lukeswitz/AntiHunter/docs/img/csi-motion.jpg

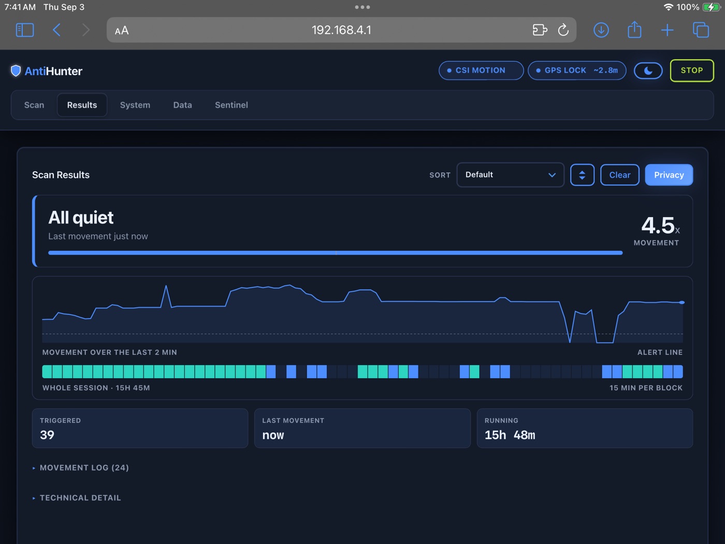
docs/img/csi-motion.jpg
