lukeswitz/AntiHunter/docs/img/hardware-node.jpg

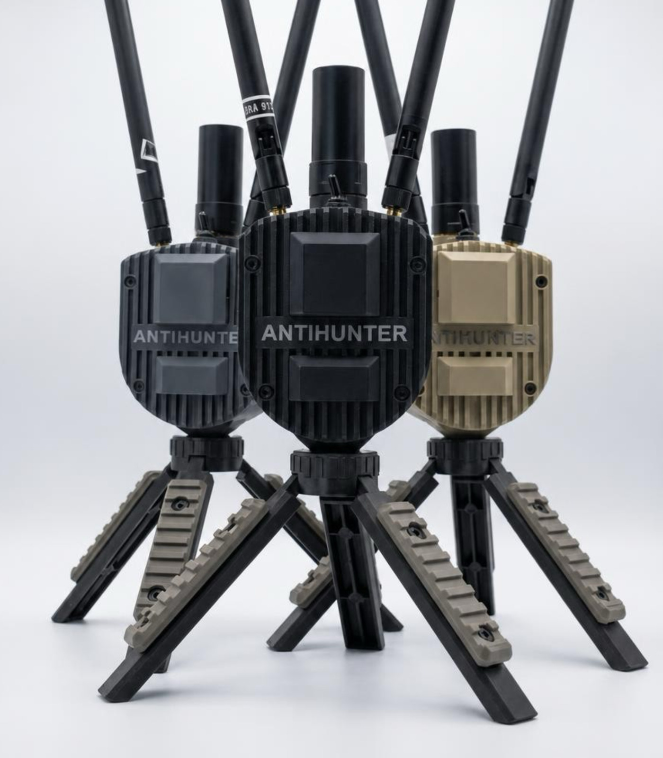
docs/img/hardware-node.jpg
