lukeswitz/AntiHunter/docs/img/node-photo.jpg

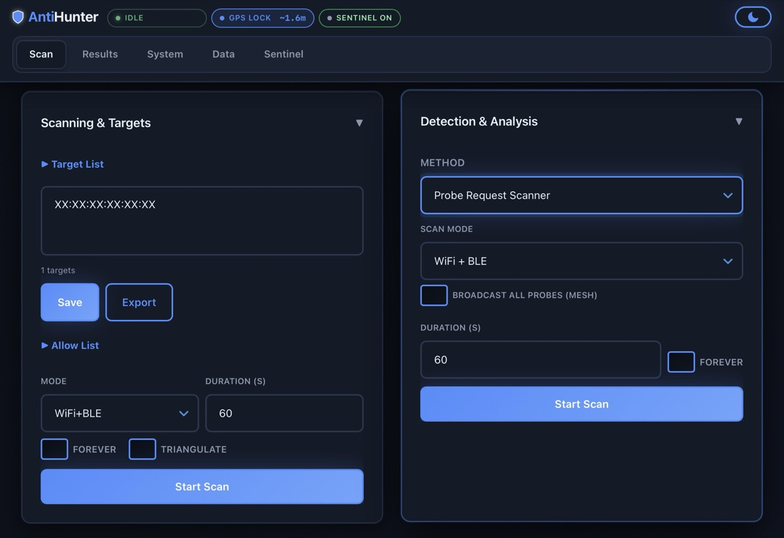
docs/img/node-photo.jpg
