lukeswitz/AntiHunter/hw/Prototype_STL_Files/AHPuckCase/puck_top.stl

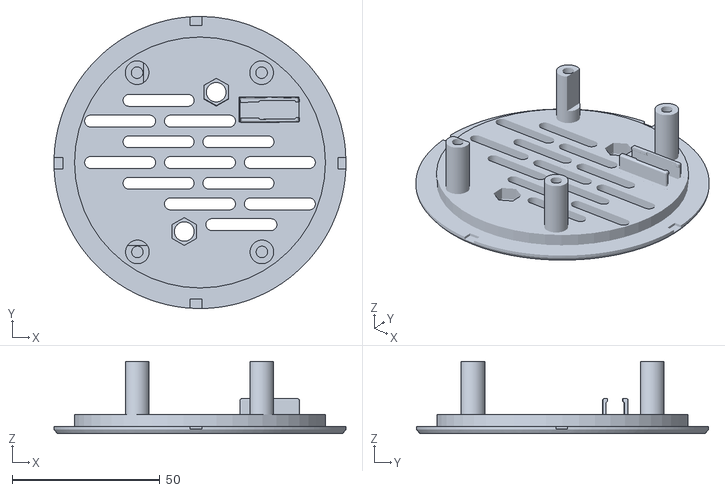
[picture p51: CAD file, 2025-11-10]
hw/Prototype_STL_Files/AHPuckCase/puck_top.stl
98.7 x 98.7 x 24.4
