lukeswitz/AntiHunter/hw/Prototype_STL_Files/AH-DIGINODE-v2/BackCover.stl

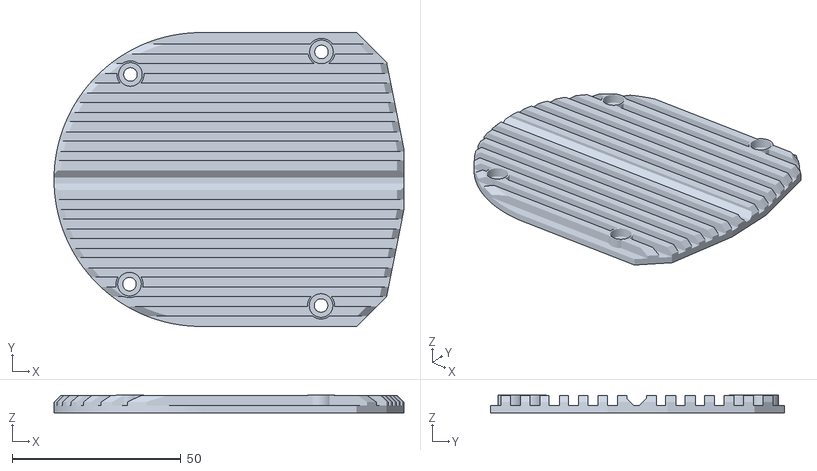
[picture p52: CAD file, 2026-02-04]
hw/Prototype_STL_Files/AH-DIGINODE-v2/BackCover.stl
103.6 x 87.0 x 5.30
