lukeswitz/AntiHunter/hw/Prototype_STL_Files/AH-DIGINODE-v2/Extentions/RadarMOD/Radar-extention-housing-fat.stl

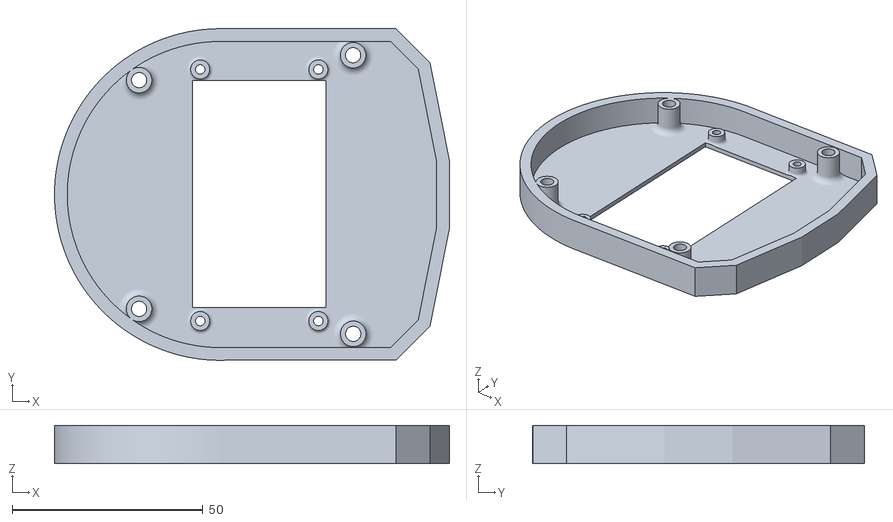
[picture p53: CAD file, 2026-02-06]
hw/Prototype_STL_Files/AH-DIGINODE-v2/Extentions/RadarMOD/Radar-extention-housing-fat.stl
103.6 x 87.0 x 10.0
