lukeswitz/AntiHunter/hw/Prototype_STL_Files/AH-DIGINODE-v2/Extentions/SEALS/Radar-SEAL.stl

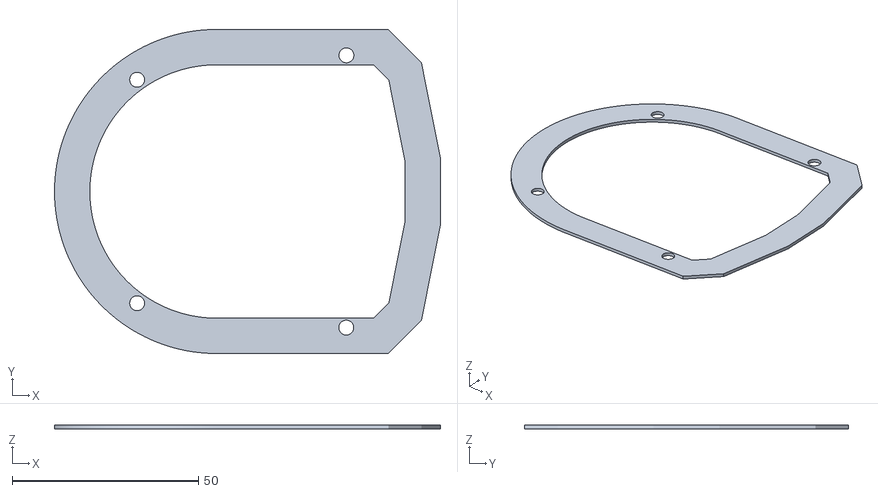
[picture p54: CAD file, 2026-02-06]
hw/Prototype_STL_Files/AH-DIGINODE-v2/Extentions/SEALS/Radar-SEAL.stl
103.6 x 87.0 x 1.00
