lukeswitz/AntiHunter/hw/Prototype_STL_Files/AHPuckCase/puck_body.stl

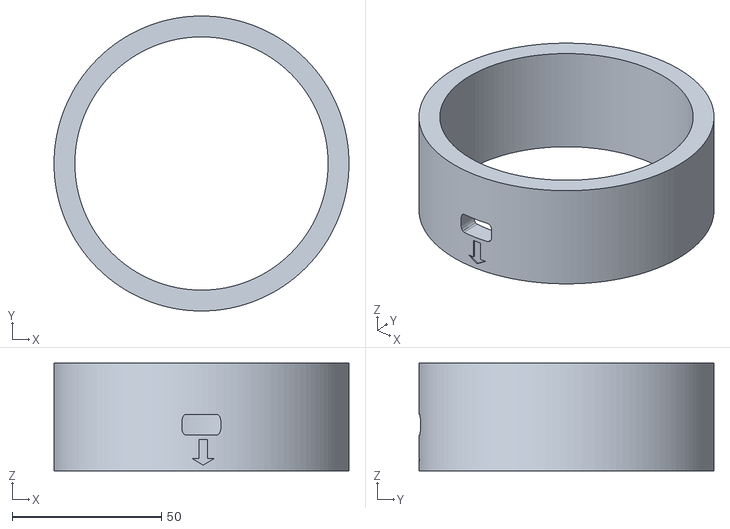
[picture p55: CAD file, 2025-11-10]
hw/Prototype_STL_Files/AHPuckCase/puck_body.stl
98.7 x 98.7 x 36.0
