lukeswitz/AntiHunter/hw/Prototype_STL_Files/AH-DIGINODE-v2/Extentions/SEALS/BatteryHousing-SEAL.stl

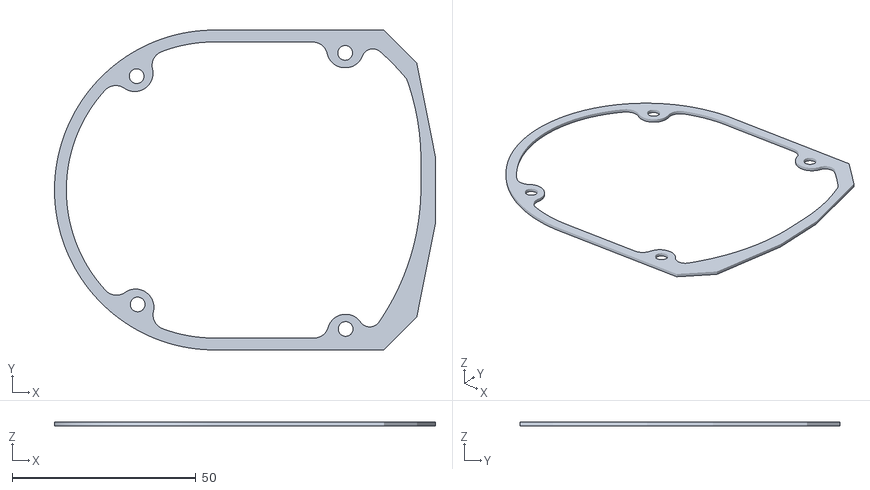
[picture p56: CAD file, 2026-02-04]
hw/Prototype_STL_Files/AH-DIGINODE-v2/Extentions/SEALS/BatteryHousing-SEAL.stl
103.6 x 87.0 x 1.00
