lukeswitz/AntiHunter/hw/Prototype_STL_Files/AH-DIGINODE-v2/FrontCover-Hidden-Fan.stl

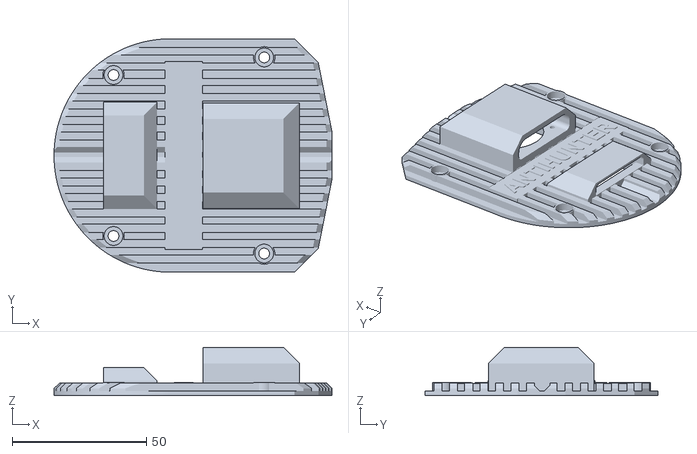
[picture p57: CAD file, 2026-02-04]
hw/Prototype_STL_Files/AH-DIGINODE-v2/FrontCover-Hidden-Fan.stl
103.6 x 87.0 x 18.0
