lukeswitz/AntiHunter/hw/Prototype_STL_Files/AH-DIGINODE-v2/Extentions/SEALS/GPS-TPU-SEAL.stl

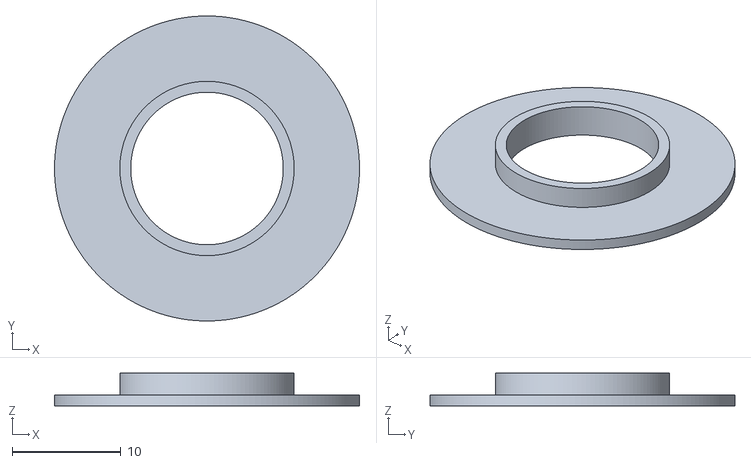
[picture p58: CAD file, 2026-02-04]
hw/Prototype_STL_Files/AH-DIGINODE-v2/Extentions/SEALS/GPS-TPU-SEAL.stl
28.0 x 28.0 x 3.00
