lukeswitz/AntiHunter/Antihunter/full/src/network.cpp

#include "network.h"
#include "baseline.h"
#include "triangulation.h"
#include "hardware.h"
#include "scanner.h"
#include "main.h"
#include "detect.h"
#include "pcap.h"
#include <AsyncTCP.h>
#include <RTClib.h>
#include <esp_timer.h>
#include <algorithm>
#include <deque>
#include <memory>

extern "C"
{
#include "esp_wifi.h"
#include "esp_wifi_types.h"
#include "esp_coexist.h"
#include "lwip/err.h"
#include "lwip/sockets.h"
}

// Network and LoRa
AsyncWebServer *server = nullptr;
static String customApSsid = "";
static String customApPass = "";
const int MAX_RETRIES = 10;
bool meshEnabled = true;
bool hbEnabled = false;
uint32_t hbInterval = 600000;
// Runtime gate for vibration mesh broadcasts (NVS key: "vibEnabled").
// Detection and USB logging always run; this only controls Serial1 TX.
bool vibrationEnabled = true;
unsigned long meshSendInterval = 3000;
std::atomic<bool> g_eraseWipeBusy{false};
volatile uint32_t apScanSuppressUntilMs = 0;
bool triangulationOrchestratorAssigned = false;


// Scanner vars
extern std::atomic<bool> scanning;
extern std::atomic<int> totalHits;
extern UniqueMacsSet uniqueMacs;

// Module refs
extern Preferences prefs;
extern std::atomic<bool> stopRequested;
extern ScanMode currentScanMode;
extern std::vector<uint8_t> CHANNELS;
extern TaskHandle_t workerTaskHandle;
extern TaskHandle_t blueTeamTaskHandle;
extern String macFmt6(const uint8_t *m);
extern bool parseMac6(const String &in, uint8_t out[6]);
extern void parseChannelsCSV(const String &csv);
extern void randomizeMacAddress();


// T114 handling
SerialRateLimiter rateLimiter;
SemaphoreHandle_t serial1Mutex = nullptr;
SerialRateLimiter::SerialRateLimiter() : tokens(MAX_TOKENS), lastRefill(millis()) {}

bool SerialRateLimiter::canSend(size_t messageLength) {
    refillTokens();
    return tokens >= messageLength;
}

void SerialRateLimiter::consume(size_t messageLength) {
    if (tokens >= messageLength) {
        tokens -= messageLength;
    }
}

void SerialRateLimiter::refillTokens() {
    unsigned long now = millis();
    if (now - lastRefill >= REFILL_INTERVAL) {
        tokens = min(tokens + TOKENS_PER_REFILL, MAX_TOKENS);
        lastRefill = now;
    }
}

void SerialRateLimiter::flush() {
    tokens = MAX_TOKENS;
    lastRefill = millis();
    Serial.println("[MESH] Rate limiter flushed");
}



bool sendToSerial1(const String &message, bool canDelay) {
    if (serial1Mutex == nullptr) {
        return false;
    }

#if !AH_CS_BLE
    if (message.indexOf(": BLE_ATTACK") >= 0) {
        return false;
    }
#endif

    bool isTriangulationMessage = message.indexOf("STOP_ACK") >= 0 ||
                                  message.indexOf("TRI_START_ACK") >= 0 ||
                                  message.indexOf("@ALL TRIANGULATE_START") >= 0 ||
                                  message.indexOf("@ALL TRI_CYCLE_START") >= 0 ||
                                  message.indexOf("TRIANGULATE_STOP") >= 0 ||
                                  message.indexOf(": T_F:") >= 0 ||
                                  message.indexOf(": T_C:") >= 0 ||
                                  message.indexOf(": T_D:") >= 0;

    if (triangulationActive && !isTriangulationMessage) {
        meshTxDroppedTriGate.fetch_add(1);
        return false;
    }

    bool isPriority = isTriangulationMessage;
    size_t msgLen = message.length() + 2;

    TickType_t timeout = isPriority ? pdMS_TO_TICKS(5000) : pdMS_TO_TICKS(1000);
    if (xSemaphoreTake(serial1Mutex, timeout) != pdTRUE) {
        Serial.printf("[MESH] Mutex timeout\n");
        return false;
    }

    // Phase 1 + review fix A: rate-limit check INSIDE mutex so canSend/consume are atomic.
    // Two concurrent senders could otherwise both pass canSend then both consume, oversubscribing the bucket.
    if (!isPriority && !rateLimiter.canSend(msgLen)) {
        meshTxDroppedRateLimit.fetch_add(1);
        Serial.printf("[MESH] DROP rate-limit: barrel_free=%u/%u need=%u msg=\"%.32s\"\n",
                      rateLimiter.available(), SerialRateLimiter::capacity(), (unsigned)msgLen, message.c_str());
        xSemaphoreGive(serial1Mutex);
        return false;
    }

    if (isPriority) {
        uint32_t waitStart = millis();
        while (Serial1.availableForWrite() < (int)msgLen) {
            if (millis() - waitStart > 5000) {
                Serial.printf("[MESH] Priority message timeout waiting for buffer space\n");
                xSemaphoreGive(serial1Mutex);
                return false;
            }
            xSemaphoreGive(serial1Mutex);
            delay(10);
            if (xSemaphoreTake(serial1Mutex, timeout) != pdTRUE) {
                Serial.printf("[MESH] Mutex timeout on retry\n");
                return false;
            }
        }
    } else {
        if (Serial1.availableForWrite() < (int)msgLen) {
            meshTxDroppedBufFull.fetch_add(1);
            Serial.printf("[MESH] DROP buf-full: avail=%d need=%u msg=\"%.32s\"\n",
                          Serial1.availableForWrite(), (unsigned)msgLen, message.c_str());
            xSemaphoreGive(serial1Mutex);
            return false;
        }
    }

    Serial1.println(message);
    Serial.printf("[MESH TX] %s\n", message.c_str());

    Serial1.flush();

    // Review fix A (completion): consume INSIDE mutex so canSend/consume are fully atomic.
    if (!isPriority) {
        rateLimiter.consume(msgLen);
    }

    {
        uint32_t total = meshDrainTotal.load();
        if (total > 0) {
            uint32_t idx = meshDrainSent.load() + meshMsgUnits(message);
            if (idx > total) idx = total;
            Serial.printf("[MESH] barrel_free=%u/%uB  drain %u/%u\n",
                          rateLimiter.available(), SerialRateLimiter::capacity(), idx, total);
        } else {
            Serial.printf("[MESH] barrel_free=%u/%uB\n",
                          rateLimiter.available(), SerialRateLimiter::capacity());
        }
    }

    xSemaphoreGive(serial1Mutex);

    return true;
}

// ------------- Network ------------- 

void restart_callback(void* arg) {
  ESP.restart();
}

void initializeNetwork()
{
  esp_coex_preference_set(ESP_COEX_PREFER_WIFI);
  Serial.println("Initializing mesh UART...");
  initializeMesh();
  memMark("mesh");

  Serial.println("Starting AP...");

  WiFi.mode(WIFI_AP_STA);
  delay(100);
  memMark("wifi mode");
  esp_wifi_stop();
  randomizeMacAddress();
  esp_wifi_start();
  
  customApSsid = prefsGetString("apSsid", AP_SSID);
  customApPass = prefsGetString("apPass", AP_PASS);
  
  if (customApSsid.length() == 0) customApSsid = AP_SSID;
  if (customApPass.length() < 8) customApPass = AP_PASS;
  
  wifi_auth_mode_t apAuth = prefs.getUChar("apAuth", 0) == 1 ? WIFI_AUTH_WPA2_PSK
                                                             : WIFI_AUTH_WPA2_WPA3_PSK;
  bool apHidden = prefs.getBool("apHidden", false);
  WiFi.softAPConfig(IPAddress(192, 168, 4, 1), IPAddress(192, 168, 4, 1), IPAddress(255, 255, 255, 0));
  bool apOk = WiFi.softAP(customApSsid.c_str(), customApPass.c_str(),
                          AP_CHANNEL, apHidden ? 1 : 0, 4, false,
                          apAuth);
  {
    wifi_config_t apCfg = {};
    if (esp_wifi_get_config(WIFI_IF_AP, &apCfg) == ESP_OK) {
      apCfg.ap.pmf_cfg.capable = true;
      apCfg.ap.pmf_cfg.required = false;
      esp_wifi_set_config(WIFI_IF_AP, &apCfg);
    }
  }
  Serial.printf("[WIFI] AP %s %s start (PMF capable): %s\n",
                apAuth == WIFI_AUTH_WPA2_PSK ? "WPA2-PSK" : "WPA2/WPA3-PSK mixed",
                apHidden ? "hidden" : "broadcast",
                apOk ? "OK" : "FAIL");
  memMark("softap");
  // SoftAP force-deauths an idle STA after inactive time (IDF default 300s). A sleeping
  // browser stops polling and gets kicked mid-scan. Not stored in flash - re-applied each boot.
  {
    esp_err_t itErr = esp_wifi_set_inactive_time(WIFI_IF_AP, AP_INACTIVE_TIME_SEC);
    Serial.printf("[WIFI] AP inactive time %us: %s\n", (unsigned)AP_INACTIVE_TIME_SEC,
                  itErr == ESP_OK ? "OK" : esp_err_to_name(itErr));
  }
  delay(500);
  WiFi.setHostname("antihunter");
  delay(100);


  WiFi.onEvent([](arduino_event_t *e) {
      if (e->event_id == ARDUINO_EVENT_WIFI_AP_STADISCONNECTED) {
          const auto &d = e->event_info.wifi_ap_stadisconnected;
          Serial.printf("[AP] STA disconnect mac=%02X:%02X:%02X:%02X:%02X:%02X aid=%u reason=%u\n",
                        d.mac[0],d.mac[1],d.mac[2],d.mac[3],d.mac[4],d.mac[5],
                        (unsigned)d.aid, (unsigned)d.reason);
          detect_onSoftApDisconnect(d.mac, (uint8_t)d.reason);
          if (d.reason != 8) apScanSuppressUntilMs = millis() + 5000;
      } else if (e->event_id == ARDUINO_EVENT_WIFI_AP_STACONNECTED) {
          detect_onSoftApConnect(e->event_info.wifi_ap_staconnected.mac);
          apScanSuppressUntilMs = millis() + 5000;
      } else if (e->event_id == ARDUINO_EVENT_WIFI_AP_PROBEREQRECVED) {
          const uint8_t *mac = e->event_info.wifi_ap_probereqrecved.mac;
          int8_t rssi = e->event_info.wifi_ap_probereqrecved.rssi;
          detect_onSoftApProbeReq(mac, rssi);
      }
  });

  esp_wifi_set_ps(WIFI_PS_NONE);

  Serial.println("Starting web server...");
  startWebServer();
  memMark("web server");
}

// ------------- AP HTML -------------

#include "web_index_html.h"

static void sendSdLog(AsyncWebServerRequest *req, const char *path, const char *mime, int missCode, const char *missMsg) {
    if (!SD.exists(path)) { req->send(missCode, missCode == 200 ? mime : "text/plain", missMsg); return; }
    if (!req->hasParam("bytes")) { req->send(SD, path, mime); return; }
    File f = SD.open(path, FILE_READ);
    if (!f) { req->send(500, "text/plain", "Open failed"); return; }
    const size_t size = f.size();
    long want = req->getParam("bytes")->value().toInt();
    if (want < 1024) want = 1024;
    if (want > 65536) want = 65536;
    size_t end = size;
    if (req->hasParam("before")) {
        long b = req->getParam("before")->value().toInt();
        if (b >= 0 && (size_t)b < size) end = (size_t)b;
    }
    size_t start = end > (size_t)want ? end - (size_t)want : 0;
    auto body = std::make_shared<PsramJsonString>();
    body->resize(end - start);
    size_t got = 0;
    if (end > start && f.seek(start)) got = f.read(reinterpret_cast<uint8_t *>(&(*body)[0]), end - start);
    f.close();
    body->resize(got);
    if (start > 0) {
        size_t nl = body->find('\n');
        if (nl != PsramJsonString::npos) { body->erase(0, nl + 1); start += nl + 1; }
    }
    AsyncWebServerResponse *res = req->beginChunkedResponse(mime,
        [body](uint8_t *buffer, size_t maxLen, size_t index) -> size_t {
            size_t total = body->size();
            if (index >= total) return 0;
            size_t n = total - index;
            if (n > maxLen) n = maxLen;
            memcpy(buffer, body->data() + index, n);
            return n;
        });
    res->addHeader("X-Start", String((unsigned long)start));
    res->addHeader("X-Size", String((unsigned long)size));
    req->send(res);
}

void registerRemainingRoutes();

// Owns scanning/handle state so a failed create can never leave a phantom "scanning" node.
static bool ahStartScanTask(TaskFunction_t fn, const char *name, uint32_t stack, int secs,
                            bool forever, TaskHandle_t *handle)
{
    scanning = true;
    if (ahCreateTask(fn, name, stack,
                     reinterpret_cast<void *>(static_cast<intptr_t>(forever ? 0 : secs)),
                     1, handle, 1) != pdPASS) {
        scanning = false;
        *handle = nullptr;
        Serial.printf("[SCAN] Task create failed: %s\n", name);
        return false;
    }
    return true;
}

void startWebServer()
{
  if (!server)
    server = new AsyncWebServer(80);

    DefaultHeaders::Instance().addHeader("Access-Control-Allow-Origin", "*");
    DefaultHeaders::Instance().addHeader("Access-Control-Allow-Methods", "GET, POST, OPTIONS");
    DefaultHeaders::Instance().addHeader("Access-Control-Allow-Headers", "Content-Type");

  server->on("/", HTTP_GET, [](AsyncWebServerRequest *r)
             {
        // ETag revalidation: 336KB page returns a tiny 304 on repeat loads, re-sent only on new fw
        static const char *ETAG = "\"" AH_GIT_SHA "\"";
        if (r->hasHeader("If-None-Match") && r->header("If-None-Match") == ETAG) { r->send(304); return; }
        AsyncWebServerResponse* res = r->beginResponse(200, "text/html", reinterpret_cast<const uint8_t*>(INDEX_HTML), strlen_P(INDEX_HTML));
        res->addHeader("ETag", ETAG);
        res->addHeader("Cache-Control", "no-cache");
        r->send(res); });

  server->on("/export", HTTP_GET, [](AsyncWebServerRequest *r)
             { r->send(200, "text/plain", getTargetsList()); });

  server->on("/results", HTTP_GET, [](AsyncWebServerRequest *r) {

      auto body = std::make_shared<PsramJsonString>();
      {
          std::lock_guard<std::mutex> lock(antihunter::lastResultsMutex);
          if (antihunter::lastResults.empty()) body->assign("None yet.");
          else body->assign(antihunter::lastResults.data(), antihunter::lastResults.size());
      }

      if (triangulationActive) {
          static String cachedTriResults = "";
          static uint32_t lastTriCalc = 0;

          if (millis() - lastTriCalc >= 1000) {
              cachedTriResults = calculateTriangulation();
              lastTriCalc = millis();
          }

          if (body->find("=== Triangulation Results") != PsramJsonString::npos) {
              body->assign(cachedTriResults.c_str(), cachedTriResults.length());
          } else {
              body->append("\n\n");
              body->append(cachedTriResults.c_str(), cachedTriResults.length());
          }
      }

      AsyncWebServerResponse *res = r->beginChunkedResponse("text/plain",
          [body](uint8_t *buffer, size_t maxLen, size_t index) -> size_t {
              size_t total = body->size();
              if (index >= total) return 0;
              size_t n = total - index;
              if (n > maxLen) n = maxLen;
              memcpy(buffer, body->data() + index, n);
              return n;
          });
      r->send(res);
  });

  server->on("/save", HTTP_POST, [](AsyncWebServerRequest *req)
             {
        if (!req->hasParam("list", true)) {
            req->send(400, "text/plain", "Missing 'list'");
            return;
        }
        String txt = req->getParam("list", true)->value();
        saveTargetsList(txt);
        saveConfiguration();
        req->send(200, "text/plain", "Saved"); });

  server->on("/node-id", HTTP_POST, [](AsyncWebServerRequest *req) {
      String id = req->hasParam("id", true) ?
          req->getParam("id", true)->value() : "";
      id.trim();
      id.toUpperCase();
      
      if (id.length() < 2 || id.length() > 5) {
          req->send(400, "text/plain", "Node ID must be 2-5 characters");
          return;
      }
      
      for (size_t i = 0; i < id.length(); i++) {
          if (!isalnum(id[i])) {
              req->send(400, "text/plain", "Only alphanumeric characters (A-Z, 0-9) allowed");
              return;
          }
      }
      
      setNodeId(id);
      saveConfiguration();
      req->send(200, "text/plain", "Node ID updated to " + id);
  });

  server->on("/node-id", HTTP_GET, [](AsyncWebServerRequest *r)
             {
    String j = "{\"nodeId\":\"" + getNodeId() + "\"}";
    r->send(200, "application/json", j); });

  server->on("/scan", HTTP_POST, [](AsyncWebServerRequest *req) {
      if (scanning || workerTaskHandle || blueTeamTaskHandle || triangulationActive) {
          req->send(409, "text/plain", "Radio busy - stop the running scan first");
          return;
      }

      int secs = 60;
      bool forever = false;
      ScanMode mode = SCAN_WIFI;
      
      if (req->hasParam("forever", true)) forever = true;
      if (req->hasParam("secs", true)) {
          int v = req->getParam("secs", true)->value().toInt();
          if (v < 0) v = 0;
          if (v > 86400) v = 86400;
          secs = v;
      }
      if (req->hasParam("mode", true)) {
          int m = req->getParam("mode", true)->value().toInt();
          if (m >= 0 && m <= 2) mode = (ScanMode)m;
      }
      if (req->hasParam("ch", true)) {
          String ch = req->getParam("ch", true)->value();
          parseChannelsCSV(ch);
      }
      saveConfiguration();
      currentScanMode = mode;
      stopRequested = false; 
      
      if (req->hasParam("triangulate", true) && req->hasParam("targetMac", true)) {
          String targetMac = req->getParam("targetMac", true)->value();
          uint8_t rfEnv = RF_ENV_INDOOR;
          if (req->hasParam("rfEnv", true)) {
              rfEnv = req->getParam("rfEnv", true)->value().toInt();
              if (rfEnv > RF_ENV_INDUSTRIAL) rfEnv = RF_ENV_INDOOR;
          }
          setRFEnvironment((RFEnvironment)rfEnv);

          distanceTuning.wifi_multiplier = 1.0f;
          distanceTuning.ble_multiplier = 1.0f;
          distanceTuning.enabled = false;

          if (req->hasParam("wifiPwr", true)) {
              float wifiPwr = req->getParam("wifiPwr", true)->value().toFloat();
              if (wifiPwr >= 0.1f && wifiPwr <= 5.0f) {
                  distanceTuning.wifi_multiplier = wifiPwr;
                  distanceTuning.enabled = true;
              }
          }

          if (req->hasParam("blePwr", true)) {
              float blePwr = req->getParam("blePwr", true)->value().toFloat();
              if (blePwr >= 0.1f && blePwr <= 5.0f) {
                  distanceTuning.ble_multiplier = blePwr;
                  distanceTuning.enabled = true;
              }
          }

          String triErr;
          if (!startTriangulation(targetMac, secs, &triErr)) {
              req->send(400, "text/plain", triErr.length() ? triErr : String("Triangulation failed to start"));
              return;
          }
          // requested scan mode here - it is what the user selected, not what was found.
          String response = "Triangulation starting for " + String(secs) + "s (env=" + String(rfEnv);
          if (distanceTuning.enabled) {
              response += ", WiFi=" + String(distanceTuning.wifi_multiplier, 1) + "x, BLE=" + String(distanceTuning.ble_multiplier, 1) + "x";
          }
          response += ")";
          req->send(200, "text/plain", response);
          return;
      }
      
      String modeStr = (mode == SCAN_WIFI) ? "WiFi" : (mode == SCAN_BLE) ? "BLE" : "WiFi+BLE";

      if (!workerTaskHandle) {
          scanning = true;
          if (ahCreateTask(listScanTask, "scan", 8192, reinterpret_cast<void*>(static_cast<intptr_t>(forever ? 0 : secs)), 1, &workerTaskHandle, 1) != pdPASS) {
              scanning = false;
              workerTaskHandle = nullptr;
              req->send(500, "text/plain", "Failed to start scan task");
              return;
          }
      }
      req->send(200, "text/plain", forever ? ("Scan starting (forever) - " + modeStr) : ("Scan starting for " + String(secs) + "s - " + modeStr));
  });

  server->on("/baseline/status", HTTP_GET, [](AsyncWebServerRequest *req) {
      String json = "{";
      json += "\"scanning\":" + String(scanning ? "true" : "false") + ",";
      {
          std::lock_guard<std::mutex> lock(baselineMutex);
          json += "\"established\":" + String(baselineEstablished ? "true" : "false") + ",";
          json += "\"devices\":" + String(baselineDeviceCount);
      }
      json += "}";

      req->send(200, "application/json", json);
  });

  server->on("/baseline/stats", HTTP_GET, [](AsyncWebServerRequest *req) {
      String json = "{";
      {
          std::lock_guard<std::mutex> lock(baselineMutex);
          json += "\"scanning\":" + String(baselineStats.isScanning ? "true" : "false") + ",";
          json += "\"phase1Complete\":" + String(baselineStats.phase1Complete ? "true" : "false") + ",";
          json += "\"established\":" + String(baselineEstablished ? "true" : "false") + ",";
          json += "\"wifiDevices\":" + String(baselineStats.wifiDevices) + ",";
          json += "\"bleDevices\":" + String(baselineStats.bleDevices) + ",";
          json += "\"totalDevices\":" + String(baselineStats.totalDevices) + ",";
          json += "\"wifiHits\":" + String(baselineStats.wifiHits) + ",";
          json += "\"bleHits\":" + String(baselineStats.bleHits) + ",";
          json += "\"anomalies\":" + String(anomalyCount) + ",";
          json += "\"elapsedTime\":" + String(baselineStats.elapsedTime) + ",";
          json += "\"totalDuration\":" + String(baselineStats.totalDuration);
      }
      json += "}";

      req->send(200, "application/json", json);
  });

server->on("/baseline/config", HTTP_GET, [](AsyncWebServerRequest *req)
        {
    String json = "{";
    json += "\"rssiThreshold\":" + String(getBaselineRssiThreshold()) + ",";
    json += "\"baselineDuration\":" + String(baselineDuration / 1000) + ",";
    json += "\"ramCacheSize\":" + String(getBaselineRamCacheSize()) + ",";
    json += "\"sdMaxDevices\":" + String(getBaselineSdMaxDevices()) + ",";
    json += "\"absenceThreshold\":" + String(getDeviceAbsenceThreshold() / 1000) + ",";
    json += "\"reappearanceWindow\":" + String(getReappearanceAlertWindow() / 1000) + ",";
    json += "\"rssiChangeDelta\":" + String(getSignificantRssiChange()) + ",";
    json += "\"enabled\":" + String(baselineDetectionEnabled ? "true" : "false") + ",";
    {
        std::lock_guard<std::mutex> lock(baselineMutex);
        json += "\"established\":" + String(baselineEstablished ? "true" : "false") + ",";
        json += "\"deviceCount\":" + String(baselineDeviceCount) + ",";
        json += "\"anomalyCount\":" + String(anomalyCount);
    }
    json += "}";

    req->send(200, "application/json", json);
  });

 server->on("/baseline/config", HTTP_POST, [](AsyncWebServerRequest *req) {
      if (req->hasParam("rssiThreshold", true)) {
          int8_t threshold = req->getParam("rssiThreshold", true)->value().toInt();
          setBaselineRssiThreshold(threshold);
          prefs.putInt("blRssi", threshold);
      }
      
      if (req->hasParam("baselineDuration", true)) {
          int v = req->getParam("baselineDuration", true)->value().toInt();
          if (v < 0) v = 0;
          if (v > 86400) v = 86400;
          baselineDuration = (uint32_t)v * 1000;
          prefs.putUInt("blDuration", baselineDuration);
      }
      
      if (req->hasParam("ramCacheSize", true)) {
          uint32_t ramSize = req->getParam("ramCacheSize", true)->value().toInt();
          setBaselineRamCacheSize(ramSize);
          prefs.putUInt("blRamSize", ramSize);
      }
      
      if (req->hasParam("sdMaxDevices", true)) {
          uint32_t sdMax = req->getParam("sdMaxDevices", true)->value().toInt();
          setBaselineSdMaxDevices(sdMax);
          prefs.putUInt("blSdMax", sdMax);
      }
      
      if (req->hasParam("absenceThreshold", true)) {
          uint32_t absence = req->getParam("absenceThreshold", true)->value().toInt() * 1000;
          setDeviceAbsenceThreshold(absence);
          prefs.putUInt("absenceThresh", absence);
      }
      
      if (req->hasParam("reappearanceWindow", true)) {
          uint32_t reappear = req->getParam("reappearanceWindow", true)->value().toInt() * 1000;
          setReappearanceAlertWindow(reappear);
          prefs.putUInt("reappearWin", reappear);
      }
      
      if (req->hasParam("rssiChangeDelta", true)) {
          int8_t delta = req->getParam("rssiChangeDelta", true)->value().toInt();
          setSignificantRssiChange(delta);
          prefs.putInt("rssiChange", delta);
      }
      
      saveConfiguration();
      req->send(200, "text/plain", "Baseline configuration updated");
  });

  server->on("/baseline/reset", HTTP_POST, [](AsyncWebServerRequest *req)
             {
        resetBaselineDetection();
        req->send(200, "text/plain", "Baseline reset complete"); });

  server->on("/baseline/mark", HTTP_POST, [](AsyncWebServerRequest *req)
             {
        if (baselineSetMarker()) req->send(200, "text/plain", "A/B marker set");
        else req->send(409, "text/plain", "Baseline scan not running"); });

  server->on("/gps", HTTP_GET, [](AsyncWebServerRequest *r)
             {
    String gpsInfo = "GPS Data: " + getGPSData() + "\n";
    if (gpsValid) {
        gpsInfo += "Latitude: " + String(gpsLat, 6) + "\n";
        gpsInfo += "Longitude: " + String(gpsLon, 6) + "\n";
    } else {
        gpsInfo += "GPS: No valid fix\n";
    }
    r->send(200, "text/plain", gpsInfo); });

  server->on("/sd-status", HTTP_GET, [](AsyncWebServerRequest *r)
             {
    String status;
    if (!sdAvailable) {
        status = "SD card: Not available";
    } else {
        uint64_t cardSize = SD.cardSize() / (1024 * 1024);

        uint32_t logSize = 0;
        File logFile = SafeSD::open("/antihunter.log", FILE_READ);
        if (logFile) {
            logSize = logFile.size();
            logFile.close();
        }

        status = "SD Card: Available\n";
        status += "Card Size: " + String(cardSize) + " MB\n";
        status += "Log File Size: " + String(logSize / 1024) + " KB (" + String(logSize) + " bytes)";
    }
    r->send(200, "text/plain", status); });

  server->on("/mesh-tx/cancel", HTTP_POST, [](AsyncWebServerRequest *req) {
      if (!meshTxPending()) {
          req->send(200, "text/plain", "Mesh TX queue already empty");
          return;
      }
      stopMeshDrain.store(true);
      req->send(200, "text/plain", "Mesh TX queue cleared, scan left running");
  });

  server->on("/sd-repair", HTTP_GET, [](AsyncWebServerRequest *req) {
      String j = "{\"auto\":" + String(sdAutoRepair ? "true" : "false") +
                 ",\"mounted\":" + String(sdAvailable ? "true" : "false") +
                 ",\"mountFailures\":" + String(SafeSD::mountFailureCount()) +
                 ",\"pending\":" + String(sdRepairPending ? "true" : "false") + "}";
      req->send(200, "application/json", j);
  });

  server->on("/sd-repair", HTTP_POST, [](AsyncWebServerRequest *req) {
      if (req->hasParam("now", true)) {
          sdRepairPending = true;
          req->send(200, "text/plain", "SD repair queued - the card is erased if it will not mount");
          return;
      }
      if (req->hasParam("auto", true)) setSdAutoRepair(req->getParam("auto", true)->value() == "1");
      req->send(200, "text/plain", sdAutoRepair ? "SD auto-repair on" : "SD auto-repair off");
  });

  server->on("/stop", HTTP_GET, [](AsyncWebServerRequest *req) {
      attack_responseCancel();
      stopAllScans();
      req->send(200, "text/plain", scanBusy() ? "Stopping all scans" : "Scan stopped");
      if (triangulationActive || triangulationInitiator) requestTriangulationStop();
  });
  registerRemainingRoutes();
}


static std::mutex s_schedMutex;
static String s_sched;
static int64_t s_schedClockOff = 0;

static time_t schedNow() {
  time_t e = getRTCEpoch();
  if (e > 1609459200) return e;
  return s_schedClockOff ? (time_t)(s_schedClockOff + esp_timer_get_time() / 1000000) : 0;
}

static void schedLearnClock(AsyncWebServerRequest *req) {
  const AsyncWebParameter *p = req->hasParam("now", true) ? req->getParam("now", true)
                             : req->hasParam("now") ? req->getParam("now") : nullptr;
  if (!p) return;
  int64_t e = p->value().toInt();
  if (e > 1609459200) s_schedClockOff = e - esp_timer_get_time() / 1000000;
}

static bool schedPathOk(const String &p) {
  return p == "/scan" || p == "/sniffer" || p == "/drone";
}

int fleetSend(String node, String cmd, String &msg) {
  node.trim();
  node.toUpperCase();
  cmd.trim();
  bool nodeOk = node.length() >= 2 && node.length() <= 5 && node != getNodeId();
  for (size_t i = 0; nodeOk && i < node.length(); i++) nodeOk = isalnum((unsigned char)node[i]);
  if (!nodeOk) { msg = "Bad node ID"; return 400; }
  static const char *const kAllowed[] = {"SCHED_ADD:", "DEVICE_SCAN_START:", "SCAN_START:", "STOP", "STATUS"};
  bool cmdOk = false;
  for (const char *p : kAllowed) {
    size_t n = strlen(p);
    if (p[n - 1] == ':' ? cmd.startsWith(p) : cmd == p) { cmdOk = true; break; }
  }
  String line = "@" + node + " " + cmd;
  for (size_t i = 0; cmdOk && i < line.length(); i++) cmdOk = line[i] >= 32 && line[i] <= 126;
  if (!cmdOk) { msg = "Command not allowed"; return 400; }
  if ((int)line.length() > MAX_MESH_SIZE) { msg = "Too long for one mesh message"; return 413; }
  if (!sendToSerial1(line, true)) { msg = "Mesh busy - retry"; return 503; }
  msg = "Sent to " + node;
  return 200;
}

static int schedPost(const String &path, const String &body) {
  int s = lwip_socket(AF_INET, SOCK_STREAM, 0);
  if (s < 0) { Serial.println("[SCHED] socket failed"); return 0; }
  struct sockaddr_in a = {};
  a.sin_family = AF_INET;
  a.sin_port = htons(80);
  a.sin_addr.s_addr = htonl(INADDR_LOOPBACK);
  struct timeval tv = {3, 0};
  lwip_setsockopt(s, SOL_SOCKET, SO_RCVTIMEO, &tv, sizeof(tv));
  lwip_setsockopt(s, SOL_SOCKET, SO_SNDTIMEO, &tv, sizeof(tv));
  char resp[128] = {0};
  if (lwip_connect(s, reinterpret_cast<struct sockaddr *>(&a), sizeof(a)) == 0) {
    String req = "POST " + path + " HTTP/1.1\r\nHost: 127.0.0.1\r\n"
                 "Content-Type: application/x-www-form-urlencoded\r\nContent-Length: " +
                 String(body.length()) + "\r\nConnection: close\r\n\r\n" + body;
    lwip_send(s, req.c_str(), req.length(), 0);
    lwip_recv(s, resp, sizeof(resp) - 1, 0);
  }
  lwip_close(s);
  char *eol = strchr(resp, '\r');
  if (eol) *eol = 0;
  Serial.printf("[SCHED] %s -> %s\n", path.c_str(), resp[0] ? resp : "no response");
  int code = 0;
  if (sscanf(resp, "HTTP/%*d.%*d %d", &code) != 1) code = 0;
  return code;
}

static uint32_t schedBodyGetSecs(const String &body) {
  int p = body.startsWith("secs=") ? 0 : body.indexOf("&secs=");
  if (p < 0) return 0;
  p += body.startsWith("secs=") ? 5 : 6;
  return (uint32_t)body.substring(p).toInt();
}

static String schedBodySetSecs(const String &body, uint32_t secs) {
  String out;
  int p = 0;
  while (p <= (int)body.length()) {
    int amp = body.indexOf('&', p);
    if (amp < 0) amp = body.length();
    String kv = body.substring(p, amp);
    if (kv.length() && !kv.startsWith("secs=")) out += (out.length() ? "&" : "") + kv;
    p = amp + 1;
  }
  return out + (out.length() ? "&" : "") + "secs=" + String(secs);
}

int schedAddBlock(const String &at, long period, const String &path, const String &body, String &msg) {
  int y, mo, d, h, mi;
  if (sscanf(at.c_str(), "%d-%d-%dT%d:%d", &y, &mo, &d, &h, &mi) != 5 ||
      mo < 1 || mo > 12 || d < 1 || d > 31 || h < 0 || h > 23 || mi < 0 || mi > 59) {
    msg = "Invalid start time";
    return 400;
  }
  long next = (long)nodeLocalToEpoch(y, mo, d, h, mi);
  if (next < 1609459200 || period < 0 || (period > 0 && period < 600) || period > 2678400) {
    msg = "Invalid start time or repeat";
    return 400;
  }
  if (!schedPathOk(path) || body.indexOf('\n') >= 0 || body.indexOf('|') >= 0 || body.length() > 1024) {
    msg = "Invalid scan request";
    return 400;
  }
  String ln = String((uint32_t)next) + "|" + String(period) + "|" + path + "|" + body + "\n";
  std::lock_guard<std::mutex> lk(s_schedMutex);
  int count = 0;
  for (unsigned i = 0; i < s_sched.length(); i++) if (s_sched[i] == '\n') count++;
  if (count >= 8 || s_sched.length() + ln.length() > 3800) {
    msg = "Schedule full: 8 blocks or 3800 bytes of NVS per schedule";
    return 413;
  }
  s_sched += ln;
  prefs.putString("sched", s_sched);
  msg = "Block added";
  return 200;
}

bool schedDelLine(const String &del) {
  std::lock_guard<std::mutex> lk(s_schedMutex);
  String out;
  bool found = false;
  int p = 0;
  while (p < (int)s_sched.length()) {
    int nl = s_sched.indexOf('\n', p);
    if (nl < 0) nl = s_sched.length();
    String ln = s_sched.substring(p, nl);
    p = nl + 1;
    if (!found && ln == del) { found = true; continue; }
    out += ln + "\n";
  }
  if (!found) return false;
  s_sched = out;
  prefs.putString("sched", s_sched);
  return true;
}

String schedListText() {
  std::lock_guard<std::mutex> lk(s_schedMutex);
  return s_sched;
}

static String s_runPath, s_runBody, s_resumePath, s_resumeBody;
static uint32_t s_runEndMs = 0;

bool schedulerYieldRadio(const char *who) {
  if (!s_runEndMs || !scanBusy()) return false;
  int32_t left = (int32_t)(s_runEndMs - millis()) / 1000;
  s_runEndMs = 0;
  if (left >= 10) {
    s_resumePath = s_runPath;
    s_resumeBody = schedBodySetSecs(s_runBody, (uint32_t)left);
  }
  Serial.printf("[SCHED] %s interrupts scheduled scan, %lds left%s\n", who, (long)left, left >= 10 ? ", resumes after" : "");
  stopAllScans();
  return true;
}

static void schedMarkRunning(const String &path, const String &body) {
  s_runPath = path;
  s_runBody = body;
  uint32_t secs = schedBodyGetSecs(body);
  s_runEndMs = millis() + (secs ? secs : 60) * 1000UL;
  if (!s_runEndMs) s_runEndMs = 1;
}

void scheduleTick() {
  static uint32_t last = 0;
  if (millis() - last < 5000) return;
  last = millis();
  if (s_runEndMs && !scanBusy()) s_runEndMs = 0;
  if (scanBusy() || triangulationActive) return;
  if (attack_responsePending() || vibAutoScanWaiting()) return;
  if (s_resumePath.length()) {
    int rc = schedPost(s_resumePath, s_resumeBody);
    if (rc == 0 || rc == 409) return;
    if (rc >= 200 && rc < 300) schedMarkRunning(s_resumePath, s_resumeBody);
    s_resumePath = "";
    s_resumeBody = "";
    return;
  }
  time_t now = schedNow();
  if (!now) return;
  String fireLine;
  {
    std::lock_guard<std::mutex> lk(s_schedMutex);
    if (!s_sched.length()) return;
    String out;
    bool dropped = false;
    int p = 0;
    while (p < (int)s_sched.length()) {
      int nl = s_sched.indexOf('\n', p);
      if (nl < 0) nl = s_sched.length();
      String ln = s_sched.substring(p, nl);
      p = nl + 1;
      int a = ln.indexOf('|'), b = ln.indexOf('|', a + 1), c = ln.indexOf('|', b + 1);
      if (a < 0 || b < 0 || c < 0 || !schedPathOk(ln.substring(b + 1, c))) { dropped = true; continue; }
      if (!fireLine.length() && (time_t)ln.substring(0, a).toInt() <= now) fireLine = ln;
      out += ln + "\n";
    }
    if (dropped) {
      s_sched = out;
      prefs.putString("sched", s_sched);
    }
  }
  if (!fireLine.length()) return;
  int a = fireLine.indexOf('|'), b = fireLine.indexOf('|', a + 1), c = fireLine.indexOf('|', b + 1);
  int code = schedPost(fireLine.substring(b + 1, c), fireLine.substring(c + 1));
  if (code == 0 || code == 409) return;
  if (code >= 200 && code < 300) schedMarkRunning(fireLine.substring(b + 1, c), fireLine.substring(c + 1));
  std::lock_guard<std::mutex> lk(s_schedMutex);
  String out;
  bool done = false;
  int p = 0;
  while (p < (int)s_sched.length()) {
    int nl = s_sched.indexOf('\n', p);
    if (nl < 0) nl = s_sched.length();
    String ln = s_sched.substring(p, nl);
    p = nl + 1;
    if (!done && ln == fireLine) {
      done = true;
      time_t next = (time_t)ln.substring(0, a).toInt();
      uint32_t period = (uint32_t)ln.substring(a + 1, b).toInt();
      if (!period) continue;
      while (next <= now) next = (period % 86400 == 0) ? nodeLocalAddDays(next, period / 86400) : next + period;
      ln = String((uint32_t)next) + ln.substring(a);
    }
    out += ln + "\n";
  }
  if (done) {
    s_sched = out;
    prefs.putString("sched", s_sched);
  }
}

void registerRemainingRoutes() {
  {
    std::lock_guard<std::mutex> lk(s_schedMutex);
    s_sched = prefs.getString("sched", "");
  }

  server->on("/schedule", HTTP_GET, [](AsyncWebServerRequest *req) {
      schedLearnClock(req);
      time_t now = schedNow();
      String out = (now ? nodeLocalString(now) : String("")) + "|" + nodeTZAbbrev(now) + "\n";
      {
        std::lock_guard<std::mutex> lk(s_schedMutex);
        int p = 0;
        while (p < (int)s_sched.length()) {
          int nl = s_sched.indexOf('\n', p);
          if (nl < 0) nl = s_sched.length();
          String ln = s_sched.substring(p, nl);
          p = nl + 1;
          out += nodeLocalString((time_t)ln.substring(0, ln.indexOf('|')).toInt()) + "|" + ln + "\n";
        }
      }
      req->send(200, "text/plain", out);
  });

  server->on("/schedule", HTTP_POST, [](AsyncWebServerRequest *req) {
      schedLearnClock(req);
      if (req->hasParam("del", true)) {
        if (!schedDelLine(req->getParam("del", true)->value())) {
          req->send(404, "text/plain", "Block changed since the list loaded - refresh and retry");
          return;
        }
        req->send(200, "text/plain", "Block removed");
        return;
      }
      if (!req->hasParam("at", true) || !req->hasParam("period", true) ||
          !req->hasParam("path", true) || !req->hasParam("body", true)) {
        req->send(400, "text/plain", "Missing at, period, path or body");
        return;
      }
      String msg;
      int code = schedAddBlock(req->getParam("at", true)->value(), req->getParam("period", true)->value().toInt(),
                               req->getParam("path", true)->value(), req->getParam("body", true)->value(), msg);
      req->send(code, "text/plain", msg);
  });

  server->on("/api/time", HTTP_POST, [](AsyncWebServerRequest *req) {
      if (!req->hasParam("epoch", true)) {
          req->send(400, "text/plain", "Missing epoch");
          return;
      }
      
      time_t epoch = req->getParam("epoch", true)->value().toInt();
      
      if (epoch < 1609459200 || epoch > 2147483647) {
          req->send(400, "text/plain", "Invalid epoch");
          return;
      }
      
      if (setRTCTimeFromEpoch(epoch)) {
          req->send(200, "text/plain", "OK");
      } else {
          req->send(500, "text/plain", "Failed");
      }
  });

  server->on("/config/autoerase", HTTP_GET, [](AsyncWebServerRequest *req)
             {
    // Update setup mode status before sending response
    updateSetupModeStatus();

    String response = "{";
    response += "\"enabled\":" + String(autoEraseEnabled ? "true" : "false") + ",";
    response += "\"delay\":" + String(autoEraseDelay) + ",";
    response += "\"cooldown\":" + String(autoEraseCooldown) + ",";
    response += "\"vibrationsRequired\":" + String(vibrationsRequired) + ",";
    response += "\"detectionWindow\":" + String(detectionWindow) + ",";
    response += "\"setupDelay\":" + String(setupDelay) + ",";
    response += "\"inSetupMode\":" + String(inSetupMode ? "true" : "false") + ",";
    response += "\"setupStartTime\":" + String(setupStartTime) + ",";
    response += "\"currentTime\":" + String(millis()) + ",";
    response += "\"tamperActive\":" + String(tamperEraseActive ? "true" : "false");
    response += "}";
    req->send(200, "application/json", response); });

  server->on("/config/autoerase", HTTP_POST, [](AsyncWebServerRequest *req)
             {
    Serial.println("\n==================== [AUTOERASE] POST HANDLER CALLED ====================");
    Serial.printf("[AUTOERASE] Total params: %d\n", req->params());

    // Debug all parameters
    for(int i=0; i<req->params(); i++){
      const AsyncWebParameter* p = req->getParam(i);
      Serial.printf("[AUTOERASE] Param[%d]: name='%s' value='%s' isPost=%d\n", i, p->name().c_str(), p->value().c_str(), p->isPost());
    }

    if (!req->hasParam("enabled", true)) {
        Serial.println("[AUTOERASE] ERROR: Missing enabled parameter");
        req->send(400, "text/plain", "Missing enabled parameter");
        return;
    }
    if (!req->hasParam("delay", true)) {
        Serial.println("[AUTOERASE] ERROR: Missing delay parameter");
        req->send(400, "text/plain", "Missing delay parameter");
        return;
    }
    if (!req->hasParam("cooldown", true)) {
        Serial.println("[AUTOERASE] ERROR: Missing cooldown parameter");
        req->send(400, "text/plain", "Missing cooldown parameter");
        return;
    }
    if (!req->hasParam("vibrationsRequired", true)) {
        Serial.println("[AUTOERASE] ERROR: Missing vibrationsRequired parameter");
        req->send(400, "text/plain", "Missing vibrationsRequired parameter");
        return;
    }
    if (!req->hasParam("detectionWindow", true)) {
        Serial.println("[AUTOERASE] ERROR: Missing detectionWindow parameter");
        req->send(400, "text/plain", "Missing detectionWindow parameter");
        return;
    }
    if (!req->hasParam("setupDelay", true)) {
        Serial.println("[AUTOERASE] ERROR: Missing setupDelay parameter");
        req->send(400, "text/plain", "Missing setupDelay parameter");
        return;
    }

    if (!req->hasParam("confirm", true) || !erasePskUserSet() ||
        req->getParam("confirm", true)->value() != erasePSK) {
        req->send(403, "text/plain", "Wrong key, or no key set");
        return;
    }

    String enabledParam = req->getParam("enabled", true)->value();
    Serial.printf("[AUTOERASE] Received enabled parameter: '%s'\n", enabledParam.c_str());

    autoEraseEnabled = (enabledParam == "true" || enabledParam == "1" || enabledParam == "on");
    autoEraseDelay = req->getParam("delay", true)->value().toInt();
    autoEraseCooldown = req->getParam("cooldown", true)->value().toInt();
    vibrationsRequired = req->getParam("vibrationsRequired", true)->value().toInt();
    detectionWindow = req->getParam("detectionWindow", true)->value().toInt();
    setupDelay = req->getParam("setupDelay", true)->value().toInt();

    Serial.printf("[AUTOERASE] autoEraseEnabled set to: %s\n", autoEraseEnabled ? "TRUE" : "FALSE");

    // Validate ranges
    autoEraseDelay = max(10000, min(300000, (int)autoEraseDelay));
    autoEraseCooldown = max(60000, min(3600000, (int)autoEraseCooldown));
    vibrationsRequired = max(2, min(10, (int)vibrationsRequired));
    detectionWindow = max(5000, min(120000, (int)detectionWindow));
    setupDelay = max(30000, min(600000, (int)setupDelay));  // 30s - 10min

    // Start setup mode when auto-erase is enabled
    if (autoEraseEnabled) {
        inSetupMode = true;
        setupStartTime = millis();

        Serial.printf("[SETUP] Setup mode started - auto-erase activates in %us\n", setupDelay/1000);

        String setupMsg = getNodeId() + ": SETUP_MODE: Auto-erase activates in " + String(setupDelay/1000) + "s";
        sendToSerial1(setupMsg, false);
    } else {
        // Clear setup mode and tamper state when disabled
        inSetupMode = false;
        setupStartTime = 0;
        tamperEraseActive = false;
        tamperSequenceStart = 0;

        Serial.println("[SETUP] Auto-erase disabled - clearing setup mode and tamper state");
    }

    saveConfiguration();
    Serial.printf("[AUTOERASE] After save - autoEraseEnabled is: %s\n", autoEraseEnabled ? "TRUE" : "FALSE");
    req->send(200, "text/plain", "Auto-erase config updated"); });

  server->on("/config", HTTP_GET, [](AsyncWebServerRequest *r) {
      extern RFScanConfig rfConfig;
      
      String configJson = "{\n";
      configJson += "\"nodeId\":\"" + jsonEscape(prefsGetString("nodeId", "")) + "\",\n";
      configJson += "\"scanMode\":" + String(currentScanMode) + ",\n";
      configJson += "\"channels\":\"" + jsonEscape(rfConfig.wifiChannels) + "\",\n";
      configJson += "\"targets\":\"" + jsonEscape(prefsGetString("maclist", "")) + "\"\n";
      configJson += "}";
      
      r->send(200, "application/json", configJson);
  });

  server->on("/config", HTTP_POST, [](AsyncWebServerRequest *req)
             {
      if (scanning || workerTaskHandle || blueTeamTaskHandle || triangulationActive) {
          req->send(409, "text/plain", "Radio busy - stop scan before changing config");
          return;
      }
      if (!req->hasParam("channels", true) || !req->hasParam("targets", true)) {
          req->send(400, "text/plain", "Missing parameters");
          return;
      }

      String channelsCSV = req->getParam("channels", true)->value();
      parseChannelsCSV(channelsCSV);
      prefs.putString("channels", channelsCSV);

      String targets = req->getParam("targets", true)->value();
      saveTargetsList(targets);
      prefs.putString("maclist", targets);

      saveConfiguration();
      req->send(200, "text/plain", "Configuration updated"); });

  server->on("/drone", HTTP_POST, [](AsyncWebServerRequest *req)
             {
        // Radio-busy guard: reject if any scan task is already running
        if (scanning || workerTaskHandle || blueTeamTaskHandle || triangulationActive) {
            req->send(409, "text/plain", "Radio busy - stop the running scan first");
            return;
        }

        int secs = 60;
        bool forever = false;

        if (req->hasParam("forever", true)) forever = true;
        if (req->hasParam("secs", true)) {
            int v = req->getParam("secs", true)->value().toInt();
            if (v < 0) v = 0;
            if (v > 86400) v = 86400;
            secs = v;
        }
        
        ScanMode dMode = SCAN_BOTH;
        if (req->hasParam("droneScanMode", true)) {
            int m = req->getParam("droneScanMode", true)->value().toInt();
            if (m == 0) dMode = SCAN_WIFI;
            else if (m == 1) dMode = SCAN_BLE;
        }
        String dModeStr = (dMode == SCAN_WIFI) ? "WiFi" : (dMode == SCAN_BLE) ? "BLE" : "WiFi+BLE";

        currentScanMode = dMode;
        stopRequested = false;

        if (!ahStartScanTask(droneDetectorTask, "drone", 12288, secs, forever, &workerTaskHandle)) {
            req->send(500, "text/plain", "Failed to start drone detection task");
            return;
        }
        req->send(200, "text/plain", forever ?
                  ("Drone detection starting (forever) - " + dModeStr) :
                  ("Drone detection starting for " + String(secs) + "s - " + dModeStr)); });

  server->on("/drone-results", HTTP_GET, [](AsyncWebServerRequest *r)
             { r->send(200, "text/plain", getDroneDetectionResults()); });

  server->on("/drone-log", HTTP_GET, [](AsyncWebServerRequest *r)
             { r->send(200, "application/json", getDroneEventLog()); });

  server->on("/drone/status", HTTP_GET, [](AsyncWebServerRequest *r)
             {
        String status = "{";
        status += "\"enabled\":" + String(droneDetectionEnabled ? "true" : "false") + ",";
        status += "\"count\":" + String(droneDetectionCount) + ",";
        size_t uniqueN;
        { std::lock_guard<std::mutex> lock(detectedDronesMutex); uniqueN = detectedDrones.size(); }
        status += "\"unique\":" + String(uniqueN);
        status += "}";
        r->send(200, "application/json", status); });

  server->on("/mesh", HTTP_POST, [](AsyncWebServerRequest *req)
             {
        if (req->hasParam("enabled", true)) {
            meshEnabled = req->getParam("enabled", true)->value() == "true";
            prefs.putBool("meshEnabled", meshEnabled);
            if (!meshEnabled) meshTxFlushQueue();
            Serial.printf("[MESH] %s\n", meshEnabled ? "Enabled" : "Disabled");
            req->send(200, "text/plain", meshEnabled ? "Mesh enabled" : "Mesh disabled");
        } else {
            req->send(400, "text/plain", "Missing enabled parameter");
        } });

  server->on("/vibration", HTTP_POST, [](AsyncWebServerRequest *req)
             {
        if (req->hasParam("enabled", true)) {
            vibrationEnabled = req->getParam("enabled", true)->value() == "true";
            lastSaveTime = 0;
            saveConfiguration();
            Serial.printf("[VIB] Vibration alerts %s via web UI\n", vibrationEnabled ? "enabled" : "disabled");
            req->send(200, "text/plain", vibrationEnabled ? "Vibration alerts enabled" : "Vibration alerts disabled");
        } else {
            req->send(400, "text/plain", "Missing enabled parameter");
        } });

  server->on("/vibration-scan", HTTP_GET, [](AsyncWebServerRequest *req)
             {
        String j = "{";
        j += "\"enabled\":" + String(vibAutoScanEnabled ? "true" : "false") + ",";
        j += "\"mode\":" + String(vibAutoScanMode) + ",";
        j += "\"duration\":" + String(vibAutoScanDuration) + ",";
        j += "\"cooldown\":" + String(vibAutoScanCooldownMs / 1000) + ",";
        j += "\"preempt\":" + String(vibAutoScanPreempt ? "true" : "false");
        j += "}";
        req->send(200, "application/json", j); });

  server->on("/vibration-scan", HTTP_POST, [](AsyncWebServerRequest *req)
             {
        if (req->hasParam("enabled", true)) {
            String e = req->getParam("enabled", true)->value();
            vibAutoScanEnabled = (e == "true" || e == "1" || e == "on");
        }
        if (req->hasParam("mode", true)) {
            int m = req->getParam("mode", true)->value().toInt();
            if (m < 0) m = 0;
            if (m > 8) m = 8;
            vibAutoScanMode = (uint8_t)m;
        }
        if (req->hasParam("duration", true)) {
            long d = req->getParam("duration", true)->value().toInt();
            if (d < 0) d = 0;
            if (d > 65535) d = 65535;
            vibAutoScanDuration = (uint16_t)d;
        }
        if (req->hasParam("cooldown", true)) {
            long c = req->getParam("cooldown", true)->value().toInt();
            if (c < 5) c = 5;
            if (c > 86400) c = 86400;
            vibAutoScanCooldownMs = (uint32_t)c * 1000UL;
        }
        if (req->hasParam("preempt", true)) {
            String e = req->getParam("preempt", true)->value();
            vibAutoScanPreempt = (e == "true" || e == "1" || e == "on");
        }
        lastSaveTime = 0;
        saveConfiguration();
        Serial.printf("[VIBSCAN] Config set via web UI: en=%d mode=%u dur=%u cd=%ums preempt=%d\n",
                      vibAutoScanEnabled ? 1 : 0, vibAutoScanMode, vibAutoScanDuration, vibAutoScanCooldownMs,
                      vibAutoScanPreempt ? 1 : 0);
        req->send(200, "text/plain", "Vibration auto-scan saved"); });

  server->on("/mesh-hb", HTTP_POST, [](AsyncWebServerRequest *req)
             {
        if (req->hasParam("enabled", true)) {
            hbEnabled = req->getParam("enabled", true)->value() == "true";
            prefs.putBool("hbEnabled", hbEnabled);
            lastSaveTime = 0;
            saveConfiguration();
            Serial.printf("[HB] Status heartbeat %s\n", hbEnabled ? "ENABLED" : "DISABLED");
            req->send(200, "text/plain", hbEnabled ? "Heartbeat enabled" : "Heartbeat disabled");
        } else {
            req->send(400, "text/plain", "Missing enabled parameter");
        } });

  server->on("/mesh-hb-interval", HTTP_POST, [](AsyncWebServerRequest *req)
             {
        if (req->hasParam("interval", true)) {
            uint32_t minutes = req->getParam("interval", true)->value().toInt();
            if (minutes < 1) minutes = 1;
            if (minutes > 60) minutes = 60;
            hbInterval = minutes * 60000;
            prefs.putUInt("hbInterval", hbInterval);
            saveConfiguration();
            Serial.printf("[HB] Interval set to %u min\n", minutes);
            req->send(200, "text/plain", "Heartbeat interval set to " + String(minutes) + " min");
        } else {
            req->send(400, "text/plain", "Missing interval parameter");
        } });

  server->on("/mesh-test", HTTP_GET, [](AsyncWebServerRequest *r)
             {
        char test_msg[] = "Antihunter: Test mesh notification";
        Serial.printf("[MESH] Test: %s\n", test_msg);
        sendToSerial1(test_msg);
        r->send(200, "text/plain", "Test message sent to mesh"); });

  server->on("/mesh-interval", HTTP_POST, [](AsyncWebServerRequest *req) {
    if (!req->hasParam("interval", true)) {
        req->send(400, "text/plain", "Missing interval parameter");
        return;
    }
    
    unsigned long interval = req->getParam("interval", true)->value().toInt();
    
    if (interval < 1500 || interval > 30000) {
        req->send(400, "text/plain", "Interval must be 1500-30000ms");
        return;
    }
    
    meshSendInterval = interval;
    prefs.putULong("meshInterval", interval);
    saveConfiguration();
    
    req->send(200, "text/plain", "Mesh interval updated to " + String(interval) + "ms");
  });

  server->on("/mesh-interval", HTTP_GET, [](AsyncWebServerRequest *req) {
    String json = "{\"interval\":" + String(meshSendInterval) + "}";
    req->send(200, "application/json", json);
  });

  server->on("/mesh-dedup-ttl", HTTP_GET, [](AsyncWebServerRequest *req) {
    String json = "{\"ttl\":" + String(getMeshDedupTtlSec()) +
                  ",\"min\":" + String(MESH_DEDUP_TTL_MIN_S) +
                  ",\"max\":" + String(MESH_DEDUP_TTL_MAX_S) +
                  ",\"session\":" + String(getMeshSessionDedup() ? "true" : "false") +
                  ",\"count\":" + String(meshDedupCount()) + "}";
    req->send(200, "application/json", json);
  });

  server->on("/mesh-dedup-ttl", HTTP_POST, [](AsyncWebServerRequest *req) {
    if (!req->hasParam("ttl", true)) {
      req->send(400, "text/plain", "Missing ttl parameter (0=disabled, 1-3600 seconds)");
      return;
    }
    long ttl = req->getParam("ttl", true)->value().toInt();
    if (ttl < 0 || ttl > (long)MESH_DEDUP_TTL_MAX_S) {
      req->send(400, "text/plain", "ttl must be 0-3600 (0=disable, value=seconds)");
      return;
    }
    setMeshDedupTtlSec((uint32_t)ttl);
    prefs.putUInt("meshDedupTtl", (uint32_t)ttl);
    saveConfiguration();
    String msg = "Mesh dedup TTL set to " + String(ttl) + "s";
    if (ttl == 0) msg += " (dedup DISABLED — every scan broadcasts every device)";
    req->send(200, "text/plain", msg);
  });

  server->on("/mesh-dedup-clear", HTTP_POST, [](AsyncWebServerRequest *req) {
    meshDedupClear();
    req->send(200, "text/plain", "Dedup cache cleared");
  });

  server->on("/mesh-session-dedup", HTTP_POST, [](AsyncWebServerRequest *req) {
    if (!req->hasParam("on", true)) {
      req->send(400, "text/plain", "Missing on parameter (0|1)");
      return;
    }
    bool on = req->getParam("on", true)->value().toInt() != 0;
    setMeshSessionDedup(on);
    prefs.putBool("meshSessDedup", on);
    saveConfiguration();
    req->send(200, "text/plain", on
      ? "Session dedup ON - re-scans send only new devices"
      : "Session dedup OFF - every scan re-broadcasts all devices");
  });

  server->on("/mesh/drain/status", HTTP_GET, [](AsyncWebServerRequest *req) {
    String json = "{\"draining\":" + String(meshTxDraining.load() ? "true" : "false") +
                  ",\"sent\":" + String(meshDrainSent.load()) +
                  ",\"total\":" + String(meshDrainTotal.load()) +
                  ",\"dedupCount\":" + String(meshDedupCount()) + "}";
    req->send(200, "application/json", json);
  });

  server->on("/api/mesh", HTTP_GET, [](AsyncWebServerRequest *req) {
    req->send(200, "application/json", meshFleetJson());
  });

  server->on("/api/mesh/ping", HTTP_POST, [](AsyncWebServerRequest *req) {
    if (!meshEnabled) {
      req->send(409, "application/json", "{\"ok\":false,\"error\":\"mesh disabled\"}");
      return;
    }
    sendMeshCommand("@ALL STATUS");
    req->send(200, "application/json", "{\"ok\":true}");
  });

  server->on("/api/fleet/send", HTTP_POST, [](AsyncWebServerRequest *req) {
    if (!meshEnabled) {
      req->send(409, "text/plain", "Mesh disabled");
      return;
    }
    if (!req->hasParam("node", true) || !req->hasParam("cmd", true)) {
      req->send(400, "text/plain", "Missing node or cmd");
      return;
    }
    String msg;
    int code = fleetSend(req->getParam("node", true)->value(), req->getParam("cmd", true)->value(), msg);
    req->send(code, "text/plain", msg);
  });

  server->on("/api/mesh/clear", HTTP_POST, [](AsyncWebServerRequest *req) {
    meshFleetClear();
    req->send(200, "application/json", "{\"ok\":true}");
  });

  server->on("/diag", HTTP_GET, [](AsyncWebServerRequest *r)
             {
        String s = getDiagnostics();
        r->send(200, "text/plain", s); });

  server->on("/erase/psk-status", HTTP_GET, [](AsyncWebServerRequest *req) {
      String json = String("{\"pskSet\":") + (erasePSK.length() > 0 ? "true" : "false") +
                    ",\"custom\":" + (erasePskUserSet() ? "true" : "false") +
                    ",\"apDefault\":" + (prefsGetString("apPass", AP_PASS) == AP_PASS ? "true" : "false") + "}";
      req->send(200, "application/json", json);
  });

  server->on("/erase/status", HTTP_GET, [](AsyncWebServerRequest *req) {
      String status;
      
      if (eraseStatus == "COMPLETED") {
          status = "COMPLETED";
      }
      else if (eraseInProgress) {
          status = eraseStatus;
      }
      else if (tamperEraseActive) {
          uint32_t timeLeft = autoEraseDelay - (millis() - tamperSequenceStart);
          status = "ACTIVE - Tamper erase countdown: " + String(timeLeft / 1000) + " seconds remaining";
      } else {
          status = "INACTIVE";
      }
      
      req->send(200, "text/plain", status);
  });

  server->on("/erase/request", HTTP_POST, [](AsyncWebServerRequest *req)
             {
    if (!req->hasParam("confirm", true)) {
        req->send(400, "text/plain", "Missing confirmation");
        return;
    }
    
    String confirm = req->getParam("confirm", true)->value();
    bool authed = erasePskUserSet() && confirm == erasePSK;
    if (!authed) {
        req->send(403, "text/plain", "Invalid confirmation");
        return;
    }

    if (g_eraseWipeBusy.exchange(true)) {
        req->send(409, "text/plain", "Erase/wipe already in progress");
        return;
    }
    String reason = req->hasParam("reason", true) ? req->getParam("reason", true)->value() : "Manual web request";
    req->send(200, "text/plain", "Secure erase initiated");

    String* reasonPtr = new String(reason);
    if (xTaskCreate([](void* param) {
        String* rp = static_cast<String*>(param);
        delay(1000); // Give web server time to send response
        bool success = executeSecureErase(*rp);
        Serial.println(success ? "Erase completed" : "Erase failed");
        delete rp;
        g_eraseWipeBusy.store(false);
        vTaskDelete(NULL);
    }, "secure_erase", 8192, reasonPtr, 1, NULL) != pdPASS) {
        delete reasonPtr;
        g_eraseWipeBusy.store(false);
    } });

  server->on("/erase/cancel", HTTP_POST, [](AsyncWebServerRequest *req)
             {
    if (!req->hasParam("confirm", true) || !erasePskUserSet() ||
        req->getParam("confirm", true)->value() != erasePSK) {
        req->send(403, "text/plain", "Wrong key, or no key set");
        return;
    }
    cancelTamperErase();
    req->send(200, "text/plain", "Tamper erase canceled"); });

  server->on("/erase/psk", HTTP_POST, [](AsyncWebServerRequest *req) {
    if (!req->hasParam("confirm", true) || !req->hasParam("key", true) || erasePSK.length() == 0 ||
        req->getParam("confirm", true)->value() != erasePSK) {
        req->send(403, "text/plain", "Wrong key, or no key set");
        return;
    }
    String key = req->getParam("key", true)->value();
    if (!erasePskValid(key)) {
        req->send(400, "text/plain", "Erase key must be 8-64 chars, no ':'");
        return;
    }
    setErasePSK(key);
    saveConfiguration();
    Serial.println("[ERASE] PSK changed via web");
    req->send(200, "text/plain", "Erase PSK changed");
  });

  server->on("/factory-wipe", HTTP_POST, [](AsyncWebServerRequest *req) {
    if (!req->hasParam("confirm", true)) {
        req->send(400, "text/plain", "Missing confirm");
        return;
    }
    String confirm = req->getParam("confirm", true)->value();
    bool authed = erasePskUserSet() && confirm == erasePSK;
    if (!authed) {
        req->send(403, "text/plain", "Invalid confirm code");
        return;
    }
    String tier = req->hasParam("tier", true) ? req->getParam("tier", true)->value() : "full";
    if (tier != "full" && tier != "config" && tier != "data") {
        req->send(400, "text/plain", "Invalid tier");
        return;
    }
    if (g_eraseWipeBusy.exchange(true)) {
        req->send(409, "text/plain", "Erase/wipe already in progress");
        return;
    }
    req->send(200, "text/plain", "Factory reset (" + tier + ") initiated — device will reboot");
    String* tierPtr = new String(tier);
    if (xTaskCreate([](void* param) {
        String* tp = static_cast<String*>(param);
        String t = *tp;
        delete tp;
        delay(800); // let response flush
        Serial.printf("[FACTORY] Reset requested: %s\n", t.c_str());
        bool ok;
        if (t == "config")      ok = performConfigReset();
        else if (t == "data")   ok = performDataReset();
        else                    ok = performSecureWipe();
        Serial.printf("[FACTORY] Reset %s %s — rebooting\n", t.c_str(), ok ? "OK" : "FAILED");
        delay(300);
        ESP.restart();
    }, "factory_wipe", 8192, tierPtr, 1, NULL) != pdPASS) {
        delete tierPtr;
        g_eraseWipeBusy.store(false);
    }
  });

  server->on("/secure/status", HTTP_GET, [](AsyncWebServerRequest *req) {
      String status = tamperEraseActive ? 
          "TAMPER_ACTIVE:" + String((autoEraseDelay - (millis() - tamperSequenceStart))/1000) + "s" : 
          "INACTIVE";
      req->send(200, "text/plain", status);
  });

  server->on("/secure/abort", HTTP_POST, [](AsyncWebServerRequest *req)
             {
    if (!req->hasParam("confirm", true) || !erasePskUserSet() ||
        req->getParam("confirm", true)->value() != erasePSK) {
        req->send(403, "text/plain", "Wrong key, or no key set");
        return;
    }
    cancelTamperErase();
    req->send(200, "text/plain", "Canceled"); });

  // Battery Saver endpoint
  server->on("/battery-saver", HTTP_GET, [](AsyncWebServerRequest *req) {
    String action = req->hasParam("action") ? req->getParam("action")->value() : "status";

    if (action == "start") {
      uint32_t intervalMinutes = req->hasParam("interval") ? req->getParam("interval")->value().toInt() : 5;
      if (intervalMinutes < 1) intervalMinutes = 1;
      if (intervalMinutes > 30) intervalMinutes = 30;
      enterBatterySaver(intervalMinutes * 60000);
      req->send(200, "text/plain", "Battery saver enabled");
    } else if (action == "stop") {
      exitBatterySaver();
      req->send(200, "text/plain", "Battery saver disabled");
    } else {
      // status
      String json = "{\"enabled\":" + String(batterySaverEnabled ? "true" : "false");
      json += ",\"interval\":" + String(batterySaverHeartbeatInterval / 60000);
      uint32_t nextHB = 0;
      if (batterySaverEnabled && lastBatterySaverHeartbeat > 0) {
        uint32_t elapsed = millis() - lastBatterySaverHeartbeat;
        if (elapsed < batterySaverHeartbeatInterval) {
          nextHB = (batterySaverHeartbeatInterval - elapsed) / 1000;
        }
      }
      json += ",\"nextHeartbeat\":" + String(nextHB) + "}";
      req->send(200, "application/json", json);
    }
  });

  server->on("/sniffer", HTTP_POST, [](AsyncWebServerRequest *req) {
        // Radio-busy guard: reject if any scan task is already running
        if (scanning || workerTaskHandle || blueTeamTaskHandle || triangulationActive) {
            req->send(409, "text/plain", "Radio busy - stop the running scan first");
            return;
        }

        g_sweepHopChannels = false;
        if (req->hasParam("ch", true)) {
            String ch = req->getParam("ch", true)->value();
            if (ch.length() > 0) {
                if (req->hasParam("split", true)) splitChannelsBegin(ch);
                else parseChannelsCSV(ch);
            }
        }

        String detection = req->hasParam("detection", true) ? req->getParam("detection", true)->value() : "device-scan";
        int secs = req->hasParam("secs", true) ? req->getParam("secs", true)->value().toInt() : 60;
        bool forever = req->hasParam("forever", true);

        if (detection == "deauth") {
            if (secs < 0) secs = 0;
            if (secs > 86400) secs = 86400;

            stopRequested = false;
            if (!ahStartScanTask(blueTeamTask, "blueteam", 12288, secs, forever, &blueTeamTaskHandle)) {
                req->send(500, "text/plain", "Failed to start deauth task");
                return;
            }
            req->send(200, "text/plain", forever ? "Deauth detection starting (forever)" : ("Deauth detection starting for " + String(secs) + "s"));

        } else if (detection == "baseline") {
            if (secs < 0) secs = 0;
            if (secs > 86400) secs = 86400;

            stopRequested = false;
            currentScanMode = SCAN_BOTH;
            if (!ahStartScanTask(baselineDetectionTask, "baseline", 12288, secs, forever, &workerTaskHandle)) {
                req->send(500, "text/plain", "Failed to start baseline task");
                return;
            }
            req->send(200, "text/plain",
                    forever ? "Baseline detection starting (forever)" :
                    ("Baseline detection starting for " + String(secs) + "s"));

        } else if (detection == "randomization-detection") {
            int scanMode = SCAN_BOTH;
            if (req->hasParam("randomizationMode", true)) {
                int mode = req->getParam("randomizationMode", true)->value().toInt();
                if (mode >= 0 && mode <= 2) {
                    scanMode = mode;
                }
            }
            
            if (secs < 0) secs = 0;
            if (secs > 86400) secs = 86400;

            stopRequested = false;

            String modeStr = (scanMode == SCAN_WIFI) ? "WiFi" :
                            (scanMode == SCAN_BLE) ? "BLE" : "WiFi+BLE";

            currentScanMode = (ScanMode)scanMode;
            {
                std::lock_guard<std::mutex> lock(antihunter::lastResultsMutex);
                antihunter::lastResults = "MAC Randomization Detection Results\nActive Sessions: 0\nDevice Identities: 0\n\n(Starting...)\n";
            }
            if (!ahStartScanTask(randomizationDetectionTask, "randdetect", 8192, secs, forever, &workerTaskHandle)) {
                req->send(500, "text/plain", "Failed to start randomization task");
                return;
            }
            req->send(200, "text/plain",
                    forever ? ("Randomization detection starting (forever) - " + modeStr) :
                    ("Randomization detection starting for " + String(secs) + "s - " + modeStr));

        } else if (detection == "device-scan") {
            int scanMode = SCAN_BOTH;
            if (req->hasParam("deviceScanMode", true)) {
                int mode = req->getParam("deviceScanMode", true)->value().toInt();
                if (mode >= 0 && mode <= 2) {
                    scanMode = mode;
                }
            }
            
            if (secs < 0) secs = 0;
            if (secs > 86400) secs = 86400;

            stopRequested = false;

            String modeStr = (scanMode == SCAN_WIFI) ? "WiFi" :
                            (scanMode == SCAN_BLE) ? "BLE" : "WiFi+BLE";

            currentScanMode = (ScanMode)scanMode;
            bool captureProbes = req->hasParam("captureProbes", true);
            if (captureProbes) {
                probeDetectionEnabled = true;
                if (probeRequestQueue == nullptr) {
                    probeRequestQueue = xQueueCreateWithCaps(256, sizeof(ProbeRequestEvent), MALLOC_CAP_SPIRAM | MALLOC_CAP_8BIT);
                } else {
                    xQueueReset(probeRequestQueue);
                }
            }
            if (!ahStartScanTask(snifferScanTask, "sniffer", 12288, secs, forever, &workerTaskHandle)) {
                req->send(500, "text/plain", "Failed to start device scan task");
                return;
            }
            req->send(200, "text/plain",
                    forever ? ("Device scan starting (forever) - " + modeStr) :
                    ("Device scan starting for " + String(secs) + "s - " + modeStr));

        } else if (detection == "probe-scan") {
            int scanMode = SCAN_BOTH;
            if (req->hasParam("probeScanMode", true)) {
                int mode = req->getParam("probeScanMode", true)->value().toInt();
                if (mode >= 0 && mode <= 2) {
                    scanMode = mode;
                }
            }

            bool broadcastAll = req->hasParam("broadcastAll", true);

            if (secs < 0) secs = 0;
            if (secs > 86400) secs = 86400;

            stopRequested = false;

            String modeStr = (scanMode == SCAN_WIFI) ? "WiFi" :
                            (scanMode == SCAN_BLE) ? "BLE" : "WiFi+BLE";

            currentScanMode = (ScanMode)scanMode;
            probeBroadcastAll.store(broadcastAll);
            if (!ahStartScanTask(probeDetectionTask, "probedet", 8192, secs, forever, &workerTaskHandle)) {
                req->send(500, "text/plain", "Failed to start probe scan task");
                return;
            }
            req->send(200, "text/plain",
                    forever ? ("Probe scan starting (forever) - " + modeStr + (broadcastAll ? " [ALL]" : "")) :
                    ("Probe scan starting for " + String(secs) + "s - " + modeStr + (broadcastAll ? " [ALL]" : "")));

        } else if (detection == "drone-detection") {
            if (secs < 0) secs = 0;
            if (secs > 86400) secs = 86400;

            ScanMode dMode = SCAN_BOTH;
            if (req->hasParam("droneScanMode", true)) {
                int m = req->getParam("droneScanMode", true)->value().toInt();
                if (m == 0) dMode = SCAN_WIFI;
                else if (m == 1) dMode = SCAN_BLE;
            }

            stopRequested = false;
            currentScanMode = dMode;
            if (!ahStartScanTask(droneDetectorTask, "drone", 12288, secs, forever, &workerTaskHandle)) {
                req->send(500, "text/plain", "Failed to start drone detection task");
                return;
            }
            req->send(200, "text/plain",
                    forever ? "Drone detection starting (forever)" :
                    ("Drone detection starting for " + String(secs) + "s"));

        } else if (detection == "pcap") {
            if (secs < 0) secs = 0;
            if (secs > 86400) secs = 86400;

            if (forever || secs == 0) {
                req->send(400, "text/plain", "Packet capture needs a duration in seconds");
                return;
            }

            if (!SafeSD::isAvailable()) {
                req->send(409, "text/plain", "No SD card - packet capture needs SD storage");
                return;
            }
            if (workerTaskHandle) {
                req->send(409, "text/plain", "Radio busy - stop the running scan");
                return;
            }

            uint8_t radio = req->hasParam("pcapRadio", true)
                          ? (uint8_t)req->getParam("pcapRadio", true)->value().toInt() : PCAP_RADIO_WIFI;
            uint8_t band = req->hasParam("pcapBand", true)
                         ? (uint8_t)req->getParam("pcapBand", true)->value().toInt() : PCAP_BAND_24;
            String pcapCh = req->hasParam("pcapChannels", true)
                          ? req->getParam("pcapChannels", true)->value() : String("");
            uint16_t dwell = req->hasParam("pcapDwell", true)
                           ? (uint16_t)req->getParam("pcapDwell", true)->value().toInt() : 250;
            if (req->hasParam("pcapMaxFile", true)) {
                setPcapMaxFileMB((uint32_t)req->getParam("pcapMaxFile", true)->value().toInt());
            }
            setPcapConfig(radio, band, pcapCh, dwell, req->hasParam("pcapMgmtOnly", true));

            stopRequested = false;
            if (!ahStartScanTask(pcapCaptureTask, "pcap", 8192, secs, false, &workerTaskHandle)) {
                scanSetCountdown(0, false);
                req->send(500, "text/plain", "Failed to start packet capture task");
                return;
            }
            req->send(200, "text/plain", "Packet capture starting for " + String(secs) + "s");

        } else {
            req->send(400, "text/plain", "Unknown detection mode");
        }
    });

  server->on("/pcap/status", HTTP_GET, [](AsyncWebServerRequest *r) {
      r->send(200, "application/json", getPcapStatusJson());
  });

  server->on("/pcap/list", HTTP_GET, [](AsyncWebServerRequest *r) {
      r->send(200, "application/json", getPcapListJson());
  });

  server->on("/pcap/download", HTTP_GET, [](AsyncWebServerRequest *r) {
      String path;
      if (r->hasParam("f")) {
          const String name = r->getParam("f")->value();
          if (!pcapNameIsValid(name)) {
              r->send(400, "text/plain", "Bad capture name");
              return;
          }
          path = "/pcap/" + name;
      } else {
          path = getPcapFilePath();
      }
      if (path.length() == 0 || !SafeSD::isAvailable() || !SafeSD::exists(path.c_str())) {
          r->send(404, "text/plain", "No capture file");
          return;
      }
      String name = path.substring(path.lastIndexOf('/') + 1);
      AsyncWebServerResponse *res = r->beginResponse(SD, path, "application/vnd.tcpdump.pcap", true);
      res->addHeader("Content-Disposition", "attachment; filename=\"" + name + "\"");
      r->send(res);
  });

  server->on("/pcap/delete", HTTP_POST, [](AsyncWebServerRequest *r) {
      if (!r->hasParam("f", true)) {
          r->send(400, "text/plain", "Missing capture name");
          return;
      }
      const String name = r->getParam("f", true)->value();
      if (!pcapNameIsValid(name)) {
          r->send(400, "text/plain", "Bad capture name");
          return;
      }
      if (!pcapDeleteFile(name)) {
          r->send(409, "text/plain", "Could not delete - capture missing or still recording");
          return;
      }
      r->send(200, "text/plain", "Deleted " + name);
  });

  server->on("/pcap/limits", HTTP_POST, [](AsyncWebServerRequest *r) {
      uint32_t budget = getPcapAutoBudgetMB();
      uint32_t floor = getPcapFreeFloorMB();
      if (r->hasParam("budgetMB", true)) budget = (uint32_t)r->getParam("budgetMB", true)->value().toInt();
      if (r->hasParam("floorMB", true)) floor = (uint32_t)r->getParam("floorMB", true)->value().toInt();
      setPcapAutoLimits(budget, floor);
      if (r->hasParam("maxFileMB", true)) {
          setPcapMaxFileMB((uint32_t)r->getParam("maxFileMB", true)->value().toInt());
      }
      r->send(200, "text/plain", "Auto-capture budget " + String(getPcapAutoBudgetMB()) +
                                 " MB, keep " + String(getPcapFreeFloorMB()) +
                                 " MB free, capture file cap " + String(getPcapMaxFileMB()) + " MB");
  });

  server->on("/pcap/delete-all", HTTP_POST, [](AsyncWebServerRequest *r) {
      const uint32_t n = pcapDeleteAll();
      r->send(200, "text/plain", "Deleted " + String(n) + " capture" + (n == 1 ? "" : "s"));
  });

  server->on("/deauth-results", HTTP_GET, [](AsyncWebServerRequest *r) {
      std::lock_guard<std::mutex> lock(deauthLogMutex);
      String results = "Deauth Attack Detection Results\n\n";
      results += "Deauth frames: " + String(deauthCount) + "\n";
      results += "Disassoc frames: " + String(disassocCount) + "\n";
      results += "Total attacks: " + String(deauthLog.size()) + "\n\n";
      
      if (deauthLog.empty()) {
          results += "No attacks detected.\n";
      } else {
          results += "Attack Details:\n";
          results += "===============\n\n";
          
          int show = min((int)deauthLog.size(), 100);
          for (int i = 0; i < show; i++) {
              const auto &hit = deauthLog[i];
              
              results += String(hit.isDisassoc ? "DISASSOCIATION" : "DEAUTHENTICATION");
              
              if (hit.isBroadcast) {
                  results += " [BROADCAST ATTACK]\n";
              } else {
                  results += " [TARGETED]\n";
              }
              
              results += "  From: " + macFmt6(hit.srcMac) + "\n";
              results += "  To: " + macFmt6(hit.destMac) + "\n";
              results += "  Network: " + macFmt6(hit.bssid) + "\n";
              results += "  Signal: " + String(hit.rssi) + " dBm\n";
              results += "  Channel: " + String(hit.channel) + "\n";
              results += "  Reason: " + getDeauthReasonText(hit.reasonCode) + "\n";
              
              uint32_t age = (millis() - hit.timestamp) / 1000;
              if (age < 60) {
                  results += "  Time: " + String(age) + " seconds ago\n";
              } else {
                  results += "  Time: " + String(age / 60) + " minutes ago\n";
              }
              results += "\n";
          }
          
          if ((int)deauthLog.size() > show) {
              results += "... (" + String(deauthLog.size() - show) + " more)\n";
          }
      }
      
      r->send(200, "text/plain", results);
  });

  server->on("/sniffer-cache", HTTP_GET, [](AsyncWebServerRequest *r)
             { r->send(200, "text/plain", getSnifferCache()); });

    server->on("/randomization-results", HTTP_GET, [](AsyncWebServerRequest *r) {
      static String cachedRandResults = "";
      static uint32_t lastRandCalc = 0;

      // Increased cache to 5 seconds to reduce mutex contention
      if (millis() - lastRandCalc >= 5000) {
          cachedRandResults = getRandomizationResults();
          lastRandCalc = millis();
      }

      r->send(200, "text/plain", cachedRandResults);
  });

  server->on("/randomization/reset", HTTP_POST, [](AsyncWebServerRequest *r) {
      if (scanning || workerTaskHandle) {
          r->send(409, "text/plain", "Radio busy - stop detection before reset");
          return;
      }
      resetRandomizationDetection();
      r->send(200, "text/plain", "Randomization detection reset");
  });

  server->on("/randomization/clear-old", HTTP_POST, [](AsyncWebServerRequest *req) {
      uint32_t now = millis();
      uint32_t ageThreshold = 3600000; // 1 hour

      if (req->hasParam("age", true)) {
          ageThreshold = req->getParam("age", true)->value().toInt() * 1000;
      }

      size_t removed = 0;
      {
          std::lock_guard<std::mutex> lock(randMutex);
          std::vector<String> toRemove;
          for (const auto& entry : deviceIdentities) {
              if (entry.second.lastSeen == 0 || (now - entry.second.lastSeen) > ageThreshold) {
                  toRemove.push_back(entry.first);
              }
          }
          for (const auto& key : toRemove) {
              deviceIdentities.erase(key);
          }
          removed = toRemove.size();
      }

      saveDeviceIdentities();

      Serial.printf("[RAND] Clear-old removed %u identities\n", (unsigned)removed);
      req->send(200, "text/plain", "Removed " + String(removed) + " old identities");
  });

  server->on("/randomization/identities", HTTP_GET, [](AsyncWebServerRequest *r) {
      std::lock_guard<std::mutex> lock(randMutex);
      
      String json = "[";
      bool first = true;
      
      for (const auto& entry : deviceIdentities) {
          if (!first) json += ",";
          first = false;
          
          const DeviceIdentity& track = entry.second;
          
          int16_t avgRssi = 0;
          if (track.signature.rssiHistoryCount > 0) {
              int32_t sum = 0;
              for (uint8_t i = 0; i < track.signature.rssiHistoryCount; i++) {
                  sum += track.signature.rssiHistory[i];
              }
              avgRssi = sum / track.signature.rssiHistoryCount;
          }
          
          String deviceType = track.isBLE ? "BLE Device" : "WiFi Device";
          
          json += "{";
          json += "\"identityId\":\"" + String(track.identityId) + "\",";
          json += "\"sessions\":" + String(track.observedSessions) + ",";
          json += "\"confidence\":" + String(track.confidence, 2) + ",";
          json += "\"avgRssi\":" + String(avgRssi) + ",";
          json += "\"deviceType\":\"" + deviceType + "\",";
          json += "\"sequenceTracking\":" + String(track.sequenceValid ? "true" : "false") + ",";
          json += "\"hasFullSig\":" + String(track.signature.hasFullSignature ? "true" : "false") + ",";
          json += "\"hasMinimalSig\":" + String(track.signature.hasMinimalSignature ? "true" : "false") + ",";
          json += "\"intervalConsistency\":" + String(track.signature.intervalConsistency, 2) + ",";
          json += "\"rssiConsistency\":" + String(track.signature.rssiConsistency, 2) + ",";
          json += "\"observations\":" + String(track.signature.observationCount) + ",";
          
          if (track.hasKnownGlobalMac) {
              json += "\"globalMac\":\"" + macFmt6(track.knownGlobalMac) + "\",";
          }
          
          json += "\"macs\":[";
          for (size_t i = 0; i < track.macs.size(); i++) {
              if (i > 0) json += ",";
              const uint8_t* mac = track.macs[i].bytes.data();
              char macStr[18];
              snprintf(macStr, sizeof(macStr), "%02X:%02X:%02X:%02X:%02X:%02X",
                       mac[0], mac[1], mac[2], mac[3], mac[4], mac[5]);
              json += "\"" + String(macStr) + "\"";
          }
          json += "]}";
      }
      
      json += "]";
      r->send(200, "application/json", json);
  });

  server->on("/api/identity-map", HTTP_GET, [](AsyncWebServerRequest *r) {
      std::lock_guard<std::mutex> lock(randMutex);
      String json = "{";
      bool first = true;
      for (const auto& entry : deviceIdentities) {
          const DeviceIdentity& id = entry.second;
          for (const auto& mac : id.macs) {
              if (!first) json += ",";
              first = false;
              json += "\"" + macFmt6(mac.bytes.data()) + "\":\"" + String(id.identityId) + "\"";
          }
          if (id.hasKnownGlobalMac) {
              if (!first) json += ",";
              first = false;
              json += "\"" + macFmt6(id.knownGlobalMac) + "\":\"" + String(id.identityId) + "\"";
          }
      }
      json += "}";
      AsyncWebServerResponse* res = r->beginResponse(200, "application/json", json);
      res->addHeader("Cache-Control", "no-store");
      r->send(res);
  });

  server->on("/allowlist-export", HTTP_GET, [](AsyncWebServerRequest *r)
           { r->send(200, "text/plain", getAllowlistText()); });

  server->on("/allowlist-save", HTTP_POST, [](AsyncWebServerRequest *req)
            {
        if (scanning || workerTaskHandle || blueTeamTaskHandle || triangulationActive) {
            req->send(409, "text/plain", "Radio busy - stop scan before changing allowlist");
            return;
        }
        if (!req->hasParam("list", true)) {
            req->send(400, "text/plain", "Missing 'list'");
            return;
        }
        String txt = req->getParam("list", true)->value();
        saveAllowlist(txt);
        saveConfiguration();
        req->send(200, "text/plain", "Allowlist saved"); });

  server->on("/triangulate/start", HTTP_POST, [](AsyncWebServerRequest *req) {
      if (scanning || workerTaskHandle || blueTeamTaskHandle || triangulationActive) {
          req->send(409, "text/plain", "Radio busy - stop the running scan first");
          return;
      }

      if (!req->hasParam("mac", true) || !req->hasParam("duration", true)) {
        req->send(400, "text/plain", "Missing mac or duration parameter");
        return;
      }

      String targetMac = req->getParam("mac", true)->value();
      int duration = req->getParam("duration", true)->value().toInt();

      if (duration < 20) {
        req->send(400, "text/plain", "Error: Triangulation requires minimum 20 seconds duration");
        return;
      }

      uint8_t macBytes[6];
      if (!parseMac6(targetMac, macBytes)) {
        req->send(400, "text/plain", "Error: Invalid MAC address format");
        return;
      }

      // Set RF environment if specified (0=OpenSky, 1=Suburban, 2=Indoor, 3=IndoorDense, 4=Industrial)
      uint8_t rfEnv = RF_ENV_INDOOR;
      if (req->hasParam("rfEnv", true)) {
          rfEnv = req->getParam("rfEnv", true)->value().toInt();
          if (rfEnv > RF_ENV_INDUSTRIAL) rfEnv = RF_ENV_INDOOR;
      }
      setRFEnvironment((RFEnvironment)rfEnv);

      distanceTuning.wifi_multiplier = 1.0f;
      distanceTuning.ble_multiplier = 1.0f;
      distanceTuning.enabled = false;

      if (req->hasParam("wifiPwr", true)) {
          float wifiPwr = req->getParam("wifiPwr", true)->value().toFloat();
          if (wifiPwr >= 0.1f && wifiPwr <= 5.0f) {
              distanceTuning.wifi_multiplier = wifiPwr;
              distanceTuning.enabled = true;
          }
      }

      if (req->hasParam("blePwr", true)) {
          float blePwr = req->getParam("blePwr", true)->value().toFloat();
          if (blePwr >= 0.1f && blePwr <= 5.0f) {
              distanceTuning.ble_multiplier = blePwr;
              distanceTuning.enabled = true;
          }
      }

      String triErr;
      if (!startTriangulation(targetMac, duration, &triErr)) {
          req->send(400, "text/plain", triErr.length() ? triErr : String("Triangulation failed to start"));
          return;
      }

      String response = "Triangulation started for " + targetMac + " (" + String(duration) + "s, env=" + String(rfEnv);
      if (distanceTuning.enabled) {
          response += ", WiFi=" + String(distanceTuning.wifi_multiplier, 2) + "x, BLE=" + String(distanceTuning.ble_multiplier, 2) + "x";
      }
      response += ")";
      req->send(200, "text/plain", response);
  });

  server->on("/triangulate/stop", HTTP_POST, [](AsyncWebServerRequest *req) {
    requestTriangulationStop();
    req->send(200, "text/plain", "Triangulation stopping");
  });

  server->on("/triangulate/status", HTTP_GET, [](AsyncWebServerRequest *req) {
    size_t nodeCount;
    {
        std::lock_guard<std::mutex> lock(triangulationMutex);
        nodeCount = triangulationNodes.size();
    }
    String json = "{";
    json += "\"active\":" + String(triangulationActive ? "true" : "false") + ",";
    json += "\"target\":\"" + triangulationTargetStr() + "\",";
    json += "\"duration\":" + String(triangulationDuration) + ",";
    json += "\"elapsed\":" + String((millis() - triangulationStart) / 1000) + ",";
    json += "\"nodes\":" + String(nodeCount);
    json += "}";
    req->send(200, "application/json", json);
  });

  server->on("/triangulate/results", HTTP_GET, [](AsyncWebServerRequest *req) {
    bool noNodes;
    {
        std::lock_guard<std::mutex> lock(triangulationMutex);
        noNodes = (triangulationNodes.size() == 0);
    }
    if (noNodes) {
      req->send(200, "text/plain", "No triangulation data available");
      return;
    }

    static String cachedTriResults = "";
    static uint32_t lastTriCalc = 0;

    // Recalculate every 1 second for more responsive updates during active triangulation
    if (millis() - lastTriCalc >= 1000) {
      cachedTriResults = calculateTriangulation();
      lastTriCalc = millis();
    }

    req->send(200, "text/plain", cachedTriResults);
  });

  server->on("/triangulate/calibrate", HTTP_POST, [](AsyncWebServerRequest *req) {
      if (!req->hasParam("mac", true) || !req->hasParam("distance", true)) {
          req->send(400, "text/plain", "Missing mac or distance parameter");
          return;
      }

      String targetMac = req->getParam("mac", true)->value();
      float distance = req->getParam("distance", true)->value().toFloat();

      calibratePathLoss(targetMac, distance);
      req->send(200, "text/plain", "Path loss calibration started for " + targetMac + " at " + String(distance) + "m");
  });

  server->on("/triangulate/nodes", HTTP_GET, [](AsyncWebServerRequest *req) {
      // Return triangulation node data as JSON for map display
      String json = "{";
      json += "\"target\":\"" + triangulationTargetStr() + "\",";
      json += "\"active\":" + String(triangulationActive ? "true" : "false") + ",";

      // Add final result if available
      {
          std::lock_guard<std::mutex> lock(triangulationMutex);
          if (apFinalResult.hasResult) {
              json += "\"finalResult\":{";
              json += "\"lat\":" + String(apFinalResult.latitude, 6) + ",";
              json += "\"lon\":" + String(apFinalResult.longitude, 6) + ",";
              json += "\"confidence\":" + String(apFinalResult.confidence * 100.0, 1) + ",";
              json += "\"uncertainty\":" + String(apFinalResult.uncertainty, 1) + ",";
              json += "\"coordinator\":\"" + apFinalResult.coordinatorNodeId + "\"";
              json += "},";
          }
      }

      // Add nodes array
      std::vector<TriangulationNode> nodesSnapshot;
      {
          std::lock_guard<std::mutex> lock(triangulationMutex);
          nodesSnapshot = triangulationNodes;
      }
      json += "\"nodes\":[";
      for (size_t i = 0; i < nodesSnapshot.size(); i++) {
          const auto& node = nodesSnapshot[i];
          json += "{";
          json += "\"id\":\"" + node.nodeId + "\",";
          json += "\"hasGPS\":" + String(node.hasGPS ? "true" : "false") + ",";
          if (node.hasGPS) {
              json += "\"lat\":" + String(node.lat, 6) + ",";
              json += "\"lon\":" + String(node.lon, 6) + ",";
              json += "\"hdop\":" + String(node.hdop, 1) + ",";
          }
          json += "\"rssi\":" + String(node.filteredRssi, 1) + ",";
          json += "\"hits\":" + String(node.hitCount) + ",";
          json += "\"quality\":" + String(node.signalQuality * 100.0, 1) + ",";
          json += "\"type\":\"" + String(node.isBLE ? "BLE" : "WiFi") + "\",";
          json += "\"distance\":" + String(node.distanceEstimate, 1);
          json += "}";
          if (i < nodesSnapshot.size() - 1) {
              json += ",";
          }
      }
      json += "]";
      json += "}";

      req->send(200, "application/json", json);
  });

  server->on("/rf-config", HTTP_GET, [](AsyncWebServerRequest *req) {
    extern RFScanConfig rfConfig;
    
    String channelsCSV = "";
    for (size_t i = 0; i < CHANNELS.size(); i++) {
        channelsCSV += String(CHANNELS[i]);
        if (i < CHANNELS.size() - 1) {
            channelsCSV += ",";
        }
    }
    
    String json = "{";
    json += "\"preset\":" + String(rfConfig.preset) + ",";
    json += "\"wifiChannelTime\":" + String(rfConfig.wifiChannelTime) + ",";
    json += "\"wifiScanInterval\":" + String(rfConfig.wifiScanInterval) + ",";
    json += "\"bleScanInterval\":" + String(rfConfig.bleScanInterval) + ",";
    json += "\"bleScanDuration\":" + String(rfConfig.bleScanDuration) + ",";
    json += "\"wifiChannels\":\"" + rfConfig.wifiChannels + "\",";
    json += "\"globalRssiThreshold\":" + String(rfConfig.globalRssiThreshold) + ",";
    json += "\"rfEnv\":" + String((int)currentRFEnvironment);
    json += "}";
    req->send(200, "application/json", json);
  });

  server->on("/rf-config", HTTP_POST, [](AsyncWebServerRequest *req) {
    if (scanning || workerTaskHandle || blueTeamTaskHandle || triangulationActive) {
        req->send(409, "text/plain", "Radio busy - stop scan before changing RF config");
        return;
    }
    bool updated = false;

    if (req->hasParam("rfEnv", true)) {
        int env = req->getParam("rfEnv", true)->value().toInt();
        if (env >= 0 && env <= RF_ENV_INDUSTRIAL) {
            setRFEnvironment((RFEnvironment)env);
            prefs.putUChar("rfEnv", (uint8_t)env);
            updated = true;
        }
    }
    
    if (req->hasParam("preset", true)) {
        uint8_t preset = req->getParam("preset", true)->value().toInt();
        if (preset <= 2) {
            setRFPreset(preset);
            updated = true;
            
            if (req->hasParam("globalRssiThreshold", true)) {
                int8_t threshold = req->getParam("globalRssiThreshold", true)->value().toInt();
                rfConfig.globalRssiThreshold = constrain(threshold, -100, -10);
                prefs.putInt("globalRSSI", rfConfig.globalRssiThreshold);
            }
        }
    } else if (req->hasParam("wifiChannelTime", true)) {
        uint32_t wct = req->getParam("wifiChannelTime", true)->value().toInt();
        uint32_t wsi = req->hasParam("wifiScanInterval", true) ?
                       (uint32_t)req->getParam("wifiScanInterval", true)->value().toInt() : rfConfig.wifiScanInterval;
        uint32_t bsi = req->hasParam("bleScanInterval", true) ?
                       (uint32_t)req->getParam("bleScanInterval", true)->value().toInt() : rfConfig.bleScanInterval;
        uint32_t bsd = req->hasParam("bleScanDuration", true) ?
                       (uint32_t)req->getParam("bleScanDuration", true)->value().toInt() : rfConfig.bleScanDuration;
        int8_t rssiThreshold = req->hasParam("globalRssiThreshold", true) ? 
                              req->getParam("globalRssiThreshold", true)->value().toInt() : rfConfig.globalRssiThreshold;
        String channels = req->hasParam("wifiChannels", true) ? 
                        req->getParam("wifiChannels", true)->value() : rfConfig.wifiChannels;
        setCustomRFConfig(wct, wsi, bsi, bsd, channels, rssiThreshold);
        updated = true;
    } else if (req->hasParam("globalRssiThreshold", true)) {
        int8_t threshold = req->getParam("globalRssiThreshold", true)->value().toInt();
        rfConfig.globalRssiThreshold = constrain(threshold, -100, -10);
        prefs.putInt("globalRSSI", rfConfig.globalRssiThreshold);
        updated = true;
    }
    
    if (updated) {
        saveConfiguration();
        
        String json = "{";
        json += "\"preset\":" + String(rfConfig.preset) + ",";
        json += "\"wifiChannelTime\":" + String(rfConfig.wifiChannelTime) + ",";
        json += "\"wifiScanInterval\":" + String(rfConfig.wifiScanInterval) + ",";
        json += "\"bleScanInterval\":" + String(rfConfig.bleScanInterval) + ",";
        json += "\"bleScanDuration\":" + String(rfConfig.bleScanDuration) + ",";
        json += "\"wifiChannels\":\"" + String(rfConfig.wifiChannels) + "\",";
        json += "\"globalRssiThreshold\":" + String(rfConfig.globalRssiThreshold);
        json += "}";
        req->send(200, "application/json", json);
    } else {
        req->send(400, "text/plain", "Missing parameters");
    }
  });

  server->on("/wifi-config", HTTP_GET, [](AsyncWebServerRequest *req) {
    String ssid = prefsGetString("apSsid", AP_SSID);
    String pass = prefsGetString("apPass", AP_PASS);
    
    if (ssid.length() == 0) ssid = AP_SSID;
    if (pass.length() == 0) pass = AP_PASS;
    
    String json = "{";
    json += "\"ssid\":\"" + ssid + "\",";
    json += "\"pass\":\"" + pass + "\",";
    json += "\"auth\":" + String(prefs.getUChar("apAuth", 0)) + ",";
    json += "\"hidden\":" + String(prefs.getBool("apHidden", false) ? "true" : "false");
    json += "}";
    req->send(200, "application/json", json);
  });

  server->on("/clear-results", HTTP_POST, [](AsyncWebServerRequest *req) {
      {
          std::lock_guard<std::mutex> lock(antihunter::lastResultsMutex);
          antihunter::lastResults.clear();
      }
      req->send(200, "text/plain", "Results cleared");
  });

  // Probe database endpoints
  server->on("/api/probedb", HTTP_GET, [](AsyncWebServerRequest *req) {
      auto body = std::make_shared<PsramJsonString>(getProbeDBJson());
      AsyncWebServerResponse *res = req->beginChunkedResponse("application/json",
          [body](uint8_t *buffer, size_t maxLen, size_t index) -> size_t {
              size_t total = body->size();
              if (index >= total) return 0;
              size_t n = total - index;
              if (n > maxLen) n = maxLen;
              memcpy(buffer, body->data() + index, n);
              return n;
          });
      req->send(res);
  });

  server->on("/api/probedb/clear", HTTP_POST, [](AsyncWebServerRequest *req) {
      clearProbeDB();
      req->send(200, "text/plain", "Probe database cleared");
  });

  server->on("/api/devicedb", HTTP_GET, [](AsyncWebServerRequest *req) {
      auto body = std::make_shared<PsramJsonString>(getDeviceDBJson());
      AsyncWebServerResponse *res = req->beginChunkedResponse("application/json",
          [body](uint8_t *buffer, size_t maxLen, size_t index) -> size_t {
              size_t total = body->size();
              if (index >= total) return 0;
              size_t n = total - index;
              if (n > maxLen) n = maxLen;
              memcpy(buffer, body->data() + index, n);
              return n;
          });
      req->send(res);
  });

  server->on("/api/devicedb/clear", HTTP_POST, [](AsyncWebServerRequest *req) {
      clearDeviceDB();
      req->send(200, "text/plain", "Device database cleared");
  });

  server->on("/api/probes.jsonl", HTTP_GET, [](AsyncWebServerRequest *req) {
      if (!SD.exists("/probes.jsonl")) {
          req->send(404, "text/plain", "No probe log file");
          return;
      }
      auto body = std::make_shared<PsramJsonString>(getProbeEventsJsonl());
      AsyncWebServerResponse *res = req->beginChunkedResponse("application/x-ndjson",
          [body](uint8_t *buffer, size_t maxLen, size_t index) -> size_t {
              size_t total = body->size();
              if (index >= total) return 0;
              size_t n = total - index;
              if (n > maxLen) n = maxLen;
              memcpy(buffer, body->data() + index, n);
              return n;
          });
      req->send(res);
  });

  server->on("/api/probes/clear", HTTP_POST, [](AsyncWebServerRequest *req) {
      SafeSD::remove("/probes.jsonl");
      SafeSD::remove("/probes_old.jsonl");
      req->send(200, "text/plain", "Probe log cleared");
  });

  // --- Data tab API endpoints ---

  server->on("/api/deauth.jsonl", HTTP_GET, [](AsyncWebServerRequest *req) {
      sendSdLog(req, "/deauth.jsonl", "application/x-ndjson", 404, "No deauth log file");
  });

  server->on("/api/deauth/clear", HTTP_POST, [](AsyncWebServerRequest *req) {
      { std::lock_guard<std::mutex> lock(deauthLogMutex); deauthLog.clear(); }
      deauthCount = 0;
      disassocCount = 0;
      SafeSD::remove("/deauth.jsonl");
      SafeSD::remove("/deauth_old.jsonl");
      req->send(200, "text/plain", "Deauth log cleared");
  });

  server->on("/api/drones.jsonl", HTTP_GET, [](AsyncWebServerRequest *req) {
      sendSdLog(req, "/drones.jsonl", "application/x-ndjson", 404, "No drone log file");
  });

  server->on("/api/drones/clear", HTTP_POST, [](AsyncWebServerRequest *req) {
      { std::lock_guard<std::mutex> lock(detectedDronesMutex); droneEventLog.clear(); detectedDrones.clear(); }
      droneDetectionCount = 0;
      SafeSD::remove("/drones.jsonl");
      SafeSD::remove("/drones_old.jsonl");
      req->send(200, "text/plain", "Drone log cleared");
  });

  server->on("/api/vibrations.jsonl", HTTP_GET, [](AsyncWebServerRequest *req) {
      sendSdLog(req, "/vibrations.jsonl", "application/x-ndjson", 404, "No vibration log file");
  });

  server->on("/api/vibrations/clear", HTTP_POST, [](AsyncWebServerRequest *req) {
      SafeSD::remove("/vibrations.jsonl");
      SafeSD::remove("/vibrations_old.jsonl");
      req->send(200, "text/plain", "Vibration log cleared");
  });

  server->on("/api/antihunter.log", HTTP_GET, [](AsyncWebServerRequest *req) {
      sendSdLog(req, "/antihunter.log", "text/plain", 404, "No system log file");
  });

  server->on("/api/antihunter.log/clear", HTTP_POST, [](AsyncWebServerRequest *req) {
      SafeSD::remove("/antihunter.log");
      req->send(200, "text/plain", "System log cleared");
  });

  server->on("/wifi-config", HTTP_POST, [](AsyncWebServerRequest *req) {
      if (!req->hasParam("ssid", true)) {
          req->send(400, "text/plain", "Missing SSID parameter");
          return;
      }
      
      String ssid = req->getParam("ssid", true)->value();
      ssid.trim();
      
      if (ssid.length() == 0 || ssid.length() > 32) {
          req->send(400, "text/plain", "SSID must be 1-32 characters");
          return;
      }
      
      String pass = "";
      if (req->hasParam("pass", true)) {
          pass = req->getParam("pass", true)->value();
          if (pass.length() > 0 && (pass.length() < 8 || pass.length() > 63)) {
              req->send(400, "text/plain", "Password must be 8-63 characters or empty");
              return;
          }
      }
      
      prefs.putString("apSsid", ssid);
      if (pass.length() > 0) {
          prefs.putString("apPass", pass);
          ensureErasePSK();
      }
      if (req->hasParam("auth", true)) {
          uint8_t auth = req->getParam("auth", true)->value().toInt() == 1 ? 1 : 0;
          prefs.putUChar("apAuth", auth);
      }
      if (req->hasParam("hidden", true)) {
          prefs.putBool("apHidden", req->getParam("hidden", true)->value().toInt() == 1);
      }

      saveConfiguration();
      
      req->send(200, "text/plain", "WiFi settings saved. Restarting in 3s...");
      esp_timer_handle_t timer;
      esp_timer_create_args_t timer_args = {
        .callback = restart_callback,
        .arg = NULL,
      };
      esp_timer_create(&timer_args, &timer);
      esp_timer_start_once(timer, 3000000);
  });

  // Onboarding disclaimer — persisted in NVS
  server->on("/api/onboarding", HTTP_GET, [](AsyncWebServerRequest *r) {
      bool done = prefs.getBool("obDone", false);
      r->send(200, "application/json", done ? "{\"accepted\":true}" : "{\"accepted\":false}");
  });
  server->on("/api/onboarding", HTTP_POST, [](AsyncWebServerRequest *r) {
      prefs.putBool("obDone", true);
      r->send(200, "application/json", "{\"accepted\":true}");
  });

  // ====== Phase 1-3: /detect endpoints ======

  // Phase 1: attack-signature jsonl getters (RAM log, recent events)
  server->on("/api/pmkid.jsonl", HTTP_GET, [](AsyncWebServerRequest *r) {
      r->send(200, "application/x-ndjson", detect_getPmkidJsonl());
  });
  server->on("/api/eviltwin.jsonl", HTTP_GET, [](AsyncWebServerRequest *r) {
      r->send(200, "application/x-ndjson", detect_getEvilTwinJsonl());
  });
  server->on("/api/ssid_confusion.jsonl", HTTP_GET, [](AsyncWebServerRequest *r) {
      r->send(200, "application/x-ndjson", detect_getSsidConfusionJsonl());
  });
  server->on("/api/sae_dos.jsonl", HTTP_GET, [](AsyncWebServerRequest *r) {
      r->send(200, "application/x-ndjson", detect_getSaeDosJsonl());
  });
  server->on("/api/owe_abuse.jsonl", HTTP_GET, [](AsyncWebServerRequest *r) {
      r->send(200, "application/x-ndjson", detect_getOweAbuseJsonl());
  });
  server->on("/api/fragattack.jsonl", HTTP_GET, [](AsyncWebServerRequest *r) {
      r->send(200, "application/x-ndjson", detect_getFragAttackJsonl());
  });
  server->on("/api/ble_malformed.jsonl", HTTP_GET, [](AsyncWebServerRequest *r) {
      r->send(200, "application/x-ndjson", detect_getBleMalformedJsonl());
  });
  server->on("/api/jamming.jsonl", HTTP_GET, [](AsyncWebServerRequest *r) {
      if (SD.exists("/jamming.jsonl")) r->send(SD, "/jamming.jsonl", "application/x-ndjson");
      else r->send(200, "application/x-ndjson", "");
  });
  server->on("/api/jamming/clear", HTTP_POST, [](AsyncWebServerRequest *r) {
      SafeSD::remove("/jamming.jsonl"); r->send(200, "text/plain", "cleared");
  });
  server->on("/api/meshguard.jsonl", HTTP_GET, [](AsyncWebServerRequest *r) {
      if (SD.exists("/meshguard.jsonl")) r->send(SD, "/meshguard.jsonl", "application/x-ndjson");
      else r->send(200, "application/x-ndjson", "");
  });
  server->on("/api/meshguard/clear", HTTP_POST, [](AsyncWebServerRequest *r) {
      SafeSD::remove("/meshguard.jsonl"); r->send(200, "text/plain", "cleared");
  });

  // === tool / tool tool-fingerprint logs (NEW) ===
  server->on("/api/ble_attack.jsonl", HTTP_GET, [](AsyncWebServerRequest *r) {
      if (SD.exists("/ble_attack.jsonl"))    r->send(SD, "/ble_attack.jsonl",    "application/x-ndjson");
      else                                   r->send(200, "application/x-ndjson", "");
  });
  server->on("/api/probe_flood.jsonl", HTTP_GET, [](AsyncWebServerRequest *r) {
      if (SD.exists("/probe_flood.jsonl"))   r->send(SD, "/probe_flood.jsonl",   "application/x-ndjson");
      else                                   r->send(200, "application/x-ndjson", "");
  });
  server->on("/api/assoc_sleep.jsonl", HTTP_GET, [](AsyncWebServerRequest *r) {
      if (SD.exists("/assoc_sleep.jsonl"))   r->send(SD, "/assoc_sleep.jsonl",   "application/x-ndjson");
      else                                   r->send(200, "application/x-ndjson", "");
  });
  server->on("/api/pmkid_forge.jsonl", HTTP_GET, [](AsyncWebServerRequest *r) {
      if (SD.exists("/pmkid_forge.jsonl"))   r->send(SD, "/pmkid_forge.jsonl",   "application/x-ndjson");
      else                                   r->send(200, "application/x-ndjson", "");
  });
  server->on("/api/eapol_bait.jsonl", HTTP_GET, [](AsyncWebServerRequest *r) {
      if (SD.exists("/eapol_bait.jsonl"))    r->send(SD, "/eapol_bait.jsonl",    "application/x-ndjson");
      else                                   r->send(200, "application/x-ndjson", "");
  });
  server->on("/api/deauth_flood.jsonl", HTTP_GET, [](AsyncWebServerRequest *r) {
      if (SD.exists("/deauth_flood.jsonl")) r->send(SD, "/deauth_flood.jsonl", "application/x-ndjson");
      else                                  r->send(200, "application/x-ndjson", "");
  });
  server->on("/api/deauth_flood/clear", HTTP_POST, [](AsyncWebServerRequest *r) {
      SafeSD::remove("/deauth_flood.jsonl"); r->send(200, "text/plain", "cleared");
  });
  server->on("/api/deauth_ap.jsonl", HTTP_GET, [](AsyncWebServerRequest *r) {
      if (SD.exists("/deauth_ap.jsonl")) r->send(SD, "/deauth_ap.jsonl", "application/x-ndjson");
      else                               r->send(200, "application/x-ndjson", "");
  });
  server->on("/api/probe_ap.jsonl", HTTP_GET, [](AsyncWebServerRequest *r) {
      if (SD.exists("/probe_ap.jsonl")) r->send(SD, "/probe_ap.jsonl", "application/x-ndjson");
      else                              r->send(200, "application/x-ndjson", "");
  });
  server->on("/api/apclients.json", HTTP_GET, [](AsyncWebServerRequest *r) {
      r->send(200, "application/json", detect_getApClientsJson());
  });
  server->on("/api/ble_attack/clear", HTTP_POST, [](AsyncWebServerRequest *r) {
      SafeSD::remove("/ble_attack.jsonl"); r->send(200, "text/plain", "cleared");
  });
  server->on("/api/probe_flood/clear", HTTP_POST, [](AsyncWebServerRequest *r) {
      SafeSD::remove("/probe_flood.jsonl"); r->send(200, "text/plain", "cleared");
  });
  server->on("/api/assoc_sleep/clear", HTTP_POST, [](AsyncWebServerRequest *r) {
      SafeSD::remove("/assoc_sleep.jsonl"); r->send(200, "text/plain", "cleared");
  });
  server->on("/api/pmkid_forge/clear", HTTP_POST, [](AsyncWebServerRequest *r) {
      SafeSD::remove("/pmkid_forge.jsonl"); r->send(200, "text/plain", "cleared");
  });
  server->on("/api/eapol_bait/clear", HTTP_POST, [](AsyncWebServerRequest *r) {
      SafeSD::remove("/eapol_bait.jsonl"); r->send(200, "text/plain", "cleared");
  });

  // === Unified incidents log (all detector events local+peer) ===
  server->on("/api/incidents.json", HTTP_GET, [](AsyncWebServerRequest *r) {
      size_t maxN = 200;
      if (r->hasParam("limit")) {
          int v = r->getParam("limit")->value().toInt();
          if (v > 0 && v <= 200) maxN = (size_t)v;
      }
      r->send(200, "application/json", detect_getIncidentsJson(maxN));
  });
  server->on("/api/incidents.jsonl", HTTP_GET, [](AsyncWebServerRequest *r) {
      sendSdLog(r, "/incidents.jsonl", "application/x-ndjson", 200, "");
  });
  server->on("/api/mesh_cmd.jsonl", HTTP_GET, [](AsyncWebServerRequest *r) {
      if (SD.exists("/mesh_cmd.jsonl")) r->send(SD, "/mesh_cmd.jsonl", "application/x-ndjson");
      else                              r->send(200, "application/x-ndjson", "");
  });
  server->on("/api/mesh_cmd", HTTP_DELETE, [](AsyncWebServerRequest *r) {
      if (SD.exists("/mesh_cmd.jsonl")) SD.remove("/mesh_cmd.jsonl");
      r->send(200, "text/plain", "cleared");
  });
  server->on("/api/incidents", HTTP_DELETE, [](AsyncWebServerRequest *r) {
      detect_clearIncidents();
      r->send(200, "text/plain", "cleared");
  });
  server->on("/api/incidents/clear", HTTP_POST, [](AsyncWebServerRequest *r) {
      detect_clearIncidents();
      r->send(200, "text/plain", "cleared");
  });
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
