lukeswitz/AntiHunter/Antihunter/headless/src/detect.cpp

#include "detect.h"
#include "hardware.h"
#include "network.h"
#include "scanner.h"
#include "baseline.h"
#include "drone_detector.h"
#include "main.h"
#include "triangulation.h"
#include <SD.h>
#include <LittleFS.h>
#include <esp_timer.h>
#include <esp_attr.h>
#include <esp_wifi.h>
#include <esp_wifi_types.h>
#include <esp_event.h>
#include <esp_netif.h>
#include <driver/gpio.h>
#include <math.h>
#include <ArduinoJson.h>
#include <Preferences.h>
#include <algorithm>
#include <numeric>
#include <deque>
#include "detect_internal.h"

extern std::atomic<bool> g_detectVerbose;

namespace ah_detect {

static uint8_t g_selfApMac[6] = {0};
static bool g_selfApMacValid = false;
static char g_selfApSsid[33] = {0};

static inline bool isSelfMac(const uint8_t *m) {
    if (!g_selfApMacValid || !m) return false;
    return memcmp(m, g_selfApMac, 6) == 0;
}

static inline bool isSelfSsid(const char *ssid) {
    if (!g_selfApSsid[0] || !ssid) return false;
    return strncmp(ssid, g_selfApSsid, sizeof(g_selfApSsid)) == 0;
}

void detect_setSelfApIdentity(const uint8_t mac[6], const char *ssid) {
    if (mac) {
        memcpy(g_selfApMac, mac, 6);
        g_selfApMacValid = true;
    }
    if (ssid) {
        strncpy(g_selfApSsid, ssid, sizeof(g_selfApSsid) - 1);
        g_selfApSsid[sizeof(g_selfApSsid) - 1] = 0;
    }
}

bool detect_isSelfApMac(const uint8_t *mac) { return isSelfMac(mac); }

template <typename M, typename F> static void evictOldestBy(M &m, F key) {
    if (m.empty()) return;
    auto oldest = m.begin();
    for (auto it = m.begin(); it != m.end(); ++it) if (key(it->second) < key(oldest->second)) oldest = it;
    m.erase(oldest);
}
template <typename M> static void evictOldestTs(M &m) {
    evictOldestBy(m, [](const typename M::mapped_type &v) { return v; });
}

uint8_t classifyEapolMsg(uint16_t keyInfo);
void hshkRecord(const uint8_t *bssid, const uint8_t *sta, uint8_t msgNum,
                       uint64_t replayCtr, int8_t rssi, const char *nodeId, uint32_t now);
void persistSnapshot();
void loadSnapshot();
void attacker_kick(const uint8_t *mac, const char *attackType);
bool isPwnagotchiBeacon(const uint8_t *frame, uint16_t len);
void pwnagotchiObserve(const uint8_t *bssid, int8_t rssi,
                              const uint8_t *ie, uint16_t ieLen);
void karma_observeProbeResp(const uint8_t *bssid, const char *ssid, int8_t rssi);
bool karma_checkBaitMatch(const char *ssid, const uint8_t *bssid, int8_t rssi);

// =============================================================================
// State
// =============================================================================

std::atomic<bool> g_detectEnabled{true};

// Tunables
std::atomic<uint16_t> g_pmkidWindow{10000};
std::atomic<uint8_t>  g_pmkidMinBssids{3};
std::atomic<uint16_t> g_saeWindow{5000};
std::atomic<uint8_t>  g_saeUnmatchedThresh{10};
std::atomic<uint16_t> g_beaconDriftPermil{50};

// Frame queue (from sniffer_cb)
QueueHandle_t g_detectFrameQueue = nullptr;

// Mutex
std::recursive_mutex g_mtx;

// PMKID burst tracking — per src MAC, list of (bssid, ts)
struct PmkidBurst {
    PsramMap<uint64_t, uint32_t> bssidTs; // packed bssid -> ts
    PsramMap<uint64_t, uint64_t> hshkKeys;
    PsramSet<uint64_t> kdeBssids;
    uint32_t lastSeen{};
};
PsramMap<uint64_t, PmkidBurst> g_pmkidBursts;
static constexpr uint32_t PMKID_ORPHAN_SETTLE_MS = 1500;

static uint64_t eapolSessionKey(const uint8_t *bssid, const uint8_t *sta) {
    uint64_t kb = 0, ks = 0;
    for (int i = 0; i < 6; ++i) kb = (kb << 8) | bssid[i];
    for (int i = 0; i < 6; ++i) ks = (ks << 8) | sta[i];
    return kb ^ (ks * 0x9E3779B97F4A7C15ULL);
}

static constexpr uint32_t HSHK_EAPOL_TIMEOUT_MS = 5000;

static const char *hshkUsablePair(const HandshakeReconstruction &r, bool &authorized) {
    const char *challenge = nullptr;
    authorized = false;
    for (size_t i = 0; i < r.fragments.size(); ++i) {
        const HandshakeFragment &a = r.fragments[i];
        for (size_t j = 0; j < r.fragments.size(); ++j) {
            if (i == j) continue;
            const HandshakeFragment &b = r.fragments[j];
            uint32_t dt = (a.ts > b.ts) ? (a.ts - b.ts) : (b.ts - a.ts);
            if (dt > HSHK_EAPOL_TIMEOUT_MS) continue;
            if (a.msgNum == 2 && b.msgNum == 3 && b.replayCtr == a.replayCtr + 1) { authorized = true; return "M2M3"; }
            if (a.msgNum == 3 && b.msgNum == 4 && b.replayCtr == a.replayCtr)     { authorized = true; return "M3M4"; }
            if (a.msgNum == 1 && b.msgNum == 4 && b.replayCtr == a.replayCtr + 1) { authorized = true; return "M1M4"; }
            if (a.msgNum == 1 && b.msgNum == 2 && b.replayCtr == a.replayCtr && !challenge) challenge = "M1M2";
        }
    }
    return challenge;
}
PsramVec<PmkidHarvestEvent> g_pmkidLog;

// Evil-twin baseline (per BSSID) — struct ApBaseline now in detect_internal.h
PsramMap<uint64_t, ApBaseline> g_apBaseline;
PsramVec<EvilTwinEvent> g_evilTwinLog;
PsramVec<SsidConfusionEvent> g_ssidConfusionLog;
PsramVec<OweAbuseEvent> g_oweAbuseLog;

// SAE tracking
struct SaeCounter {
    uint16_t commits;
    uint16_t confirms;
    uint32_t windowStart;
    bool alerted;
};
PsramMap<uint64_t, SaeCounter> g_saeCounters;
PsramVec<SaeDosEvent> g_saeDosLog;

// Auth-frame flood (mdk4 mode a / Auth-DoS): open-system Auth (algo=0) flooded
// to one BSSID from many spoofed src MACs, none completing association.
// docs/detector-verification.md section 1. Always-on (like deauth), no toggle.
struct AuthFloodWindow {
    uint32_t windowStartMs{};
    uint16_t frames{};
    PsramSet<uint64_t> distinctSrc;
    int8_t   bestRssi{};
    uint8_t  channel{};
    bool     alerted{};
};
PsramMap<uint64_t, AuthFloodWindow> g_authFlood;
static constexpr size_t   MAX_AUTH_FLOOD_MAP = 32;
static constexpr uint32_t AUTH_FLOOD_WIN_MS  = 5000;
static constexpr uint16_t AUTH_FLOOD_DISTINCT_SRC = 16;  // spoofed-MAC fan-out
static constexpr uint16_t AUTH_FLOOD_FRAMES  = 60;        // raw rate floor in window

// In-progress fragmented-MSDU tracking for real FragAttacks signatures
// (CVE-2020-26146 non-consecutive PN, CVE-2020-26147 mixed enc/plaintext) —
// key = (srcMac<<4 | tid). Passive: reads FC MoreFrag + seq-ctrl frag# + CCMP PN.
struct FragMsdu {
    uint16_t seqNum;
    uint8_t  lastFrag;
    uint32_t lastFragPN;
    bool     started;
    bool     firstProtected;
    uint32_t lastSeen;
};
PsramMap<uint64_t, FragMsdu> g_fragMsdu;
PsramVec<FragAttackEvent> g_fragLog;
std::atomic<bool>    g_fragEnabled{false};

// WiFi-LAYER interference detection (Xu MobiHoc'05 PDR-vs-RSSI consistency).
// Per-channel 1s window: interference => collapsed PDR (CRC-fail frames) WHILE
// error-frame RSSI stays strong AND channel was alive. Weak-signal loss (low
// RSSI+low PDR) and idle channels are excluded. Needs FCSFAIL in the promiscuous
// filter to see CRC fails.
// SCOPE/LIMIT (honest): this only catches interference that still produces 802.11
// energy the ESP32 PHY tries to decode (deceptive/flood jammers, heavy collisions).
// It does NOT detect RF carrier jammers — nRF24/CC1101 CW or GFSK-flood (e.g. Bruce
// fw) and constant-AWGN blackout emit NO 802.11 frames -> zero RX -> looks idle.
// There is no CCA/energy-detect API on ESP32 WiFi. Detecting those needs a second
// radio (nRF24 RPD channel sweep, WatchDog-2.4 method) — not present on this HW.
std::atomic<bool>     g_jamEnabled{true};
static std::atomic<uint32_t> g_chanRx[15];
static std::atomic<uint32_t> g_jamValid[14];
static std::atomic<uint32_t> g_jamErr[14];
static std::atomic<int32_t>  g_jamErrRssi[14];
static uint32_t g_jamEverValid[14] = {0};
static uint32_t g_jamLastEmit[14]  = {0};
static uint32_t g_jamLastEval = 0;

// Mesh-channel disruption guard (text-layer, AntiHunter's own Meshtastic channel).
// Detects: self-ID spoof (we receive our own node id), channel flood (inbound rate),
// privileged-command injection from a sender with no benign history. Alerts log
// LOCALLY only (never re-broadcast — would amplify a flood). Replay/malformed
// dropped (weak/FP-prone).
std::atomic<bool> g_meshGuardEnabled{false};
static uint32_t g_meshInbWinMs = 0;
static uint32_t g_meshInbCount = 0;
static uint32_t g_meshLastFloodMs = 0;
static uint32_t g_meshLastSpoofMs = 0;
static uint32_t g_meshGuardHits = 0;

// Per-feature enable (local detection on/off)
std::atomic<bool> g_karmaEnabled{false};
std::atomic<bool> g_pmkidEnabled{true};
std::atomic<bool> g_eviltwinEnabled{true};
std::atomic<bool> g_ssidConfusionEnabled{true};
std::atomic<bool> g_saeEnabled{true};
std::atomic<bool> g_sentinelScanMode{false};
std::atomic<bool> g_oweEnabled{false};
std::atomic<bool> g_bleMalformedEnabled{false};
std::atomic<bool> g_hshkEnabled{true};
std::atomic<bool> g_pwnaEnabled{true};
std::atomic<bool> g_tsfEnabled{false};
std::atomic<bool> g_csaQuietEnabled{true};
std::atomic<bool> g_ridSpoofEnabled{false};
std::atomic<bool> g_bloomGossipEnabled{false};
std::atomic<bool> g_attackerTrilatEnabled{false};
std::atomic<uint8_t> g_attackRespMask{0};
std::atomic<uint16_t> g_arSecsTrilat{60};
std::atomic<uint16_t> g_arSecsPcap{120};
std::atomic<uint16_t> g_arSecsDevice{60};
std::atomic<uint16_t> g_arSecsProbe{60};
std::atomic<uint16_t> g_arSecsDrone{60};

// Per-feature mesh broadcast — 15 flags for 19 canonical events
std::atomic<bool> g_meshDeauth{true};      // DEAUTH_FORGE, DEAUTH_FLOOD, DEAUTH_AP_TARGETED
std::atomic<bool> g_meshBeacon{true};      // BEACON_FLOOD
std::atomic<bool> g_meshAuth{true};        // AUTH_FLOOD
std::atomic<bool> g_meshAssocSleep{true};  // ASSOC_SLEEP
std::atomic<bool> g_meshSae{true};         // SAE_DOS
std::atomic<bool> g_meshEviltwin{true};    // EVILTWIN
std::atomic<bool> g_meshOwe{true};         // OWE_ABUSE
std::atomic<bool> g_meshKarma{true};       // KARMA_CAND, KARMA_CONFIRMED
std::atomic<bool> g_meshPmkid{true};       // PMKID_HARVEST, PMKID_FORGE
std::atomic<bool> g_meshProbeFlood{true};  // PROBE_FLOOD, PROBE_FLOOD_AP
std::atomic<bool> g_meshHshk{true};        // HSHK, KRACK
std::atomic<bool> g_meshFrag{true};        // FRAG
std::atomic<bool> g_meshTsf{true};         // TSF (EVILTWIN w/ TSF reason)
std::atomic<bool> g_meshJam{true};         // JAM
std::atomic<bool> g_meshGuard{true};       // MESH_SPOOF_SELF, MESH_FLOOD (+ cmd provenance audit)
// Legacy atomics kept to avoid linker break — not in UI
std::atomic<bool> g_meshSsidConf{true};
std::atomic<bool> g_meshBleMalformed{false};
std::atomic<bool> g_meshKrack{true};
std::atomic<bool> g_meshTracker{true};
std::atomic<bool> g_meshPwna{true};
std::atomic<bool> g_meshRecon{true};
std::atomic<bool> g_meshAttackerHunt{true};
std::atomic<bool> g_meshEapolBait{true};

// BLE malformed
PsramVec<BleMalformedEvent> g_bleMalformedLog;

// Recon
PsramMap<String, ReconAlert> g_recon;

// RID claims (mesh-cooperative validation)
PsramMap<String, RidClaim> g_ridClaims;  // key = uavId

// Quorum
PsramMap<String, AlertCandidate> g_alerts;  // key = type+":"+key
PsramMap<String, uint8_t> g_quorumRequired;

// Bloom — local + neighbor union
BloomFilter g_localBloom;
BloomFilter g_neighborBloom;
uint32_t g_lastBloomGossip = 0;

// PPS
volatile uint64_t g_ppsAnchorMicros = 0;
volatile uint32_t g_ppsAnchorEpoch = 0;
volatile uint32_t g_ppsLastEdge = 0;
std::atomic<bool> g_ppsLocked{false};

// Channel partition (per-node assigned set; coordinator drives via mesh)
std::vector<uint8_t> g_myChannels;
PsramMap<String, std::vector<uint8_t>> g_chanAssignments;

// OUI category table
struct OuiTableEntry {
    uint8_t oui[3];
    uint8_t cat;
} __attribute__((packed));
PsramVec<OuiTableEntry> g_ouiTable;

// Log caps
static constexpr size_t MAX_PMKID_LOG = 100;
static constexpr size_t MAX_ET_LOG = 100;
static constexpr size_t MAX_SC_LOG = 100;
static constexpr size_t MAX_SAE_LOG = 100;
static constexpr size_t MAX_OWE_LOG = 50;
static constexpr size_t MAX_FRAG_LOG = 100;
static constexpr size_t MAX_BLEM_LOG = 100;

// =============================================================================
// Helpers
// =============================================================================

static PsramMap<String, uint32_t> g_meshRateMap;
static std::atomic<uint32_t> g_droppedWifi{0};
static std::atomic<uint32_t> g_droppedBle{0};
static std::atomic<uint32_t> g_meshGated{0};
bool meshRateGate(const String &type, uint32_t minIntervalMs) {
    uint32_t now = millis();
    auto it = g_meshRateMap.find(type);
    if (it != g_meshRateMap.end() && (now - it->second) < minIntervalMs) {
        g_meshGated.fetch_add(1);
        return false;
    }
    g_meshRateMap[type] = now;
    if (g_meshRateMap.size() > 256) {
        String oldestK;
        uint32_t oldestT = UINT32_MAX;
        for (const auto &kv : g_meshRateMap) if (kv.second < oldestT) { oldestT = kv.second; oldestK = kv.first; }
        g_meshRateMap.erase(oldestK);
    }
    return true;
}

// FNV-1a 32-bit
static uint32_t fnv1a(const uint8_t *data, size_t len) {
    uint32_t h = 0x811C9DC5;
    for (size_t i = 0; i < len; ++i) { h ^= data[i]; h *= 16777619u; }
    return h;
}

// IE hash — concatenate (tag, len) pairs (skip value where length variable like SSID/TIM)
// Captures IE order + presence; tolerates value churn that doesn't indicate spoof.
static uint32_t hashIeSet(const uint8_t *ie, uint16_t ieLen) {
    uint32_t h = 0x811C9DC5;
    uint16_t off = 0;
    while (off + 2 <= ieLen) {
        uint8_t tag = ie[off];
        uint8_t len = ie[off+1];
        if (off + 2 + len > ieLen) break;
        h ^= tag; h *= 16777619u;
        // For stable IEs (RSN, HT cap, VHT cap, Ext cap, Vendor) include value too
        if (tag == 48 || tag == 45 || tag == 191 || tag == 127 || tag == 221) {
            for (uint8_t i = 0; i < len; ++i) { h ^= ie[off+2+i]; h *= 16777619u; }
        }
        off += 2 + len;
    }
    return h;
}

static bool extractSSID(const uint8_t *ie, uint16_t ieLen, char *out, size_t outSz) {
    uint16_t off = 0;
    while (off + 2 <= ieLen) {
        uint8_t tag = ie[off];
        uint8_t len = ie[off+1];
        if (off + 2 + len > ieLen) break;
        if (tag == 0) {
            size_t n = std::min<size_t>(len, outSz - 1);
            memcpy(out, ie + off + 2, n);
            out[n] = 0;
            for (size_t i = 0; i < n; ++i) {
                if ((uint8_t)out[i] < 32 || (uint8_t)out[i] > 126) out[i] = '?';
            }
            return true;
        }
        off += 2 + len;
    }
    out[0] = 0;
    return false;
}

static bool hasOpenAuth(const uint8_t *ie, uint16_t ieLen) {
    // Open if no RSN (48) and no WPA vendor IE (221 with WPA OUI 00:50:F2 type 1)
    uint16_t off = 0;
    while (off + 2 <= ieLen) {
        uint8_t tag = ie[off];
        uint8_t len = ie[off+1];
        if (off + 2 + len > ieLen) break;
        if (tag == 48) return false;
        if (tag == 221 && len >= 4 &&
            ie[off+2] == 0x00 && ie[off+3] == 0x50 && ie[off+4] == 0xF2 && ie[off+5] == 0x01) {
            return false;
        }
        off += 2 + len;
    }
    return true;
}

// OWE Transition Mode element: vendor IE OUI 50:6F:9A type 0x1C
static bool extractOweTransition(const uint8_t *ie, uint16_t ieLen, uint8_t *outBssid) {
    uint16_t off = 0;
    while (off + 2 <= ieLen) {
        uint8_t tag = ie[off];
        uint8_t len = ie[off+1];
        if (off + 2 + len > ieLen) break;
        if (tag == 221 && len >= 10 &&
            ie[off+2] == 0x50 && ie[off+3] == 0x6F && ie[off+4] == 0x9A &&
            ie[off+5] == 0x1C) {
            memcpy(outBssid, ie + off + 6, 6);
            return true;
        }
        off += 2 + len;
    }
    return false;
}

// BloomFilter impl moved outside ah_detect namespace (defined below namespace block)

// =============================================================================
// PPS — GPS pulse-per-second time discipline
// =============================================================================
static int g_ppsGpio = -1;

static void IRAM_ATTR pps_isr(void *) {
    uint64_t now = esp_timer_get_time();  // µs since boot
    g_ppsAnchorMicros = now;
    g_ppsLastEdge = (uint32_t)now;
    // Epoch update happens in detectTask polling getRTCEpoch (avoid I2C from ISR)
}

void initGpsPps(int gpio) {
    if (gpio < 0) return;
    g_ppsGpio = gpio;
    gpio_config_t cfg = {};
    cfg.pin_bit_mask = (1ULL << gpio);
    cfg.mode = GPIO_MODE_INPUT;
    cfg.pull_up_en = GPIO_PULLUP_DISABLE;
    cfg.pull_down_en = GPIO_PULLDOWN_ENABLE;
    cfg.intr_type = GPIO_INTR_POSEDGE;
    gpio_config(&cfg);
    // ISR service is installed earlier by the SD SPI driver and/or Arduino attachInterrupt.
    // Try adding the handler directly; only install if not yet installed (ESP_ERR_INVALID_STATE).
    esp_err_t err = gpio_isr_handler_add((gpio_num_t)gpio, pps_isr, nullptr);
    if (err == ESP_ERR_INVALID_STATE) {
        if (gpio_install_isr_service(0) == ESP_OK) {
            err = gpio_isr_handler_add((gpio_num_t)gpio, pps_isr, nullptr);
        }
    }
    if (err != ESP_OK) {
        Serial.printf("[PPS] handler_add failed: %s\n", esp_err_to_name(err));
        return;
    }
    Serial.printf("[PPS] Armed on GPIO %d\n", gpio);
}

uint64_t getDisciplinedMicros() {
    uint64_t bootMicros = esp_timer_get_time();
    static portMUX_TYPE ppsMux = portMUX_INITIALIZER_UNLOCKED;
    uint32_t epoch;
    uint64_t anchor;
    portENTER_CRITICAL(&ppsMux);
    epoch = g_ppsAnchorEpoch;
    anchor = g_ppsAnchorMicros;
    portEXIT_CRITICAL(&ppsMux);
    if (epoch == 0 || anchor == 0) {
        time_t e = getRTCEpoch();
        return (uint64_t)e * 1000000ULL;
    }
    return ((uint64_t)epoch * 1000000ULL) + (bootMicros - anchor);
}

// =============================================================================
// EAPOL capture-bait witness store
// =============================================================================
// Tracks recent unicast deauths (src, dst, ts). When EAPOL traffic from dst
// appears within EAPOL_BAIT_WINDOW_MS, the src is flagged as a capture-bait
// attacker. tool capture_handshake() emits one targeted deauth to force a
// re-association so it can sniff EAPOL.
struct DeauthWitness {
    uint8_t src[6];
    uint8_t dst[6];
    uint32_t ts;
    int8_t rssi;
    uint8_t channel;
    uint8_t deauthCount;  // increments on repeat from same src
    bool forged;
    bool alerted;
};
static PsramVec<DeauthWitness> g_deauthWitness;
static constexpr size_t MAX_DEAUTH_WITNESS = 32;
static constexpr uint32_t EAPOL_BAIT_WINDOW_MS = 30000;
static constexpr uint32_t EAPOL_BAIT_FAST_MS = 1000;
static constexpr uint32_t EAPOL_BAIT_HIGH_MS = 2000;

void detect_correlateEapolBait(const uint8_t *sta, const uint8_t *apBssid, int8_t rssi, uint8_t channel);

void detect_witnessDeauth(const uint8_t *src, const uint8_t *dst, int8_t rssi, uint8_t channel, bool forged = false) {
    if (!src || !dst) return;
    uint32_t now = millis();
    std::lock_guard<std::recursive_mutex> lk(g_mtx);
    // Age out + look for existing entry from same src
    for (auto it = g_deauthWitness.begin(); it != g_deauthWitness.end(); ) {
        if (now - it->ts > EAPOL_BAIT_WINDOW_MS) { it = g_deauthWitness.erase(it); continue; }
        if (memcmp(it->src, src, 6) == 0 && memcmp(it->dst, dst, 6) == 0) {
            it->ts = now;
            if (forged) it->forged = true;
            if (it->deauthCount < 255) it->deauthCount++;
            return;
        }
        ++it;
    }
    if (g_deauthWitness.size() >= MAX_DEAUTH_WITNESS) {
        // evict oldest
        size_t oldestIdx = 0; uint32_t oldestTs = UINT32_MAX;
        for (size_t i = 0; i < g_deauthWitness.size(); ++i) {
            if (g_deauthWitness[i].ts < oldestTs) { oldestTs = g_deauthWitness[i].ts; oldestIdx = i; }
        }
        g_deauthWitness.erase(g_deauthWitness.begin() + oldestIdx);
    }
    DeauthWitness w{};
    memcpy(w.src, src, 6);
    memcpy(w.dst, dst, 6);
    w.ts = now;
    w.rssi = rssi;
    w.channel = channel;
    w.deauthCount = 1;
    w.forged = forged;
    w.alerted = false;
    g_deauthWitness.push_back(w);
}

void detect_correlateEapolBait(const uint8_t *sta, const uint8_t *apBssid, int8_t rssi, uint8_t channel) {
    if (!sta) return;
    uint32_t now = millis();
    std::lock_guard<std::recursive_mutex> lk(g_mtx);
    for (auto &w : g_deauthWitness) {
        if (now - w.ts > EAPOL_BAIT_WINDOW_MS) continue;
        bool dstMatch = memcmp(w.dst, sta, 6) == 0;
        bool wDstBcast = (w.dst[0] & w.dst[1] & w.dst[2] & w.dst[3] & w.dst[4] & w.dst[5]) == 0xFF;
        bool bcastBait = wDstBcast && apBssid && memcmp(w.src, apBssid, 6) == 0;
        if (!dstMatch && !bcastBait) continue;
        // Bait pattern: 1-3 deauths total from src X to STA Y, then EAPOL from Y.
        // >3 deauths = ongoing DoS attack, not bait sniff.
        if (w.deauthCount > 3) continue;
        if (w.alerted) continue;
        uint32_t latencyMs = now - w.ts;
        if (!w.forged && latencyMs > EAPOL_BAIT_FAST_MS) continue;
        w.alerted = true;
        const char *confidence = (w.forged && latencyMs <= EAPOL_BAIT_HIGH_MS) ? "high" : "medium";
        char srcBuf[18], dstBuf[18];
        snprintf(srcBuf, sizeof(srcBuf), "%02X:%02X:%02X:%02X:%02X:%02X",
                 w.src[0],w.src[1],w.src[2],w.src[3],w.src[4],w.src[5]);
        snprintf(dstBuf, sizeof(dstBuf), "%02X:%02X:%02X:%02X:%02X:%02X",
                 w.dst[0],w.dst[1],w.dst[2],w.dst[3],w.dst[4],w.dst[5]);
        String srcS(srcBuf);
        String dstS(dstBuf);
        char lineBuf[320];
        snprintf(lineBuf, sizeof(lineBuf),
                 "{\"src\":\"%s\",\"sta\":\"%s\",\"deauth_count\":%u,\"latency_ms\":%u,\"confidence\":\"%s\",\"rssi\":%d,\"ch\":%u,\"reason\":\"EAPOL_CAPTURE_BAIT\",\"ts\":%u}",
                 srcBuf, dstBuf, (unsigned)w.deauthCount, (unsigned)latencyMs,
                 confidence, (int)rssi, (unsigned)channel, (unsigned)now);
        String line(lineBuf);
        logEventToSD("/eapol_bait.jsonl", line);
        ::detect_logIncident(String("EAPOL_BAIT:") + srcS + ":" + dstS + ":" +
                             String(w.deauthCount) + ":" + String(rssi) + ":" + confidence, nullptr);
        if (meshEnabled && sentinel_isRunning() && g_meshEapolBait.load() && meshRateGate("EAPOL_BAIT_" + srcS + "_" + dstS, 60000)) {
            sendToSerial1(getNodeId() + ": EAPOL_BAIT:" + srcS + ":" + dstS +
                          ":" + String(w.deauthCount) + ":" + String(rssi) +
                          ":" + confidence, true);
        }
        quorum_addReport("EAPOL_BAIT", srcS, getNodeId(), rssi);
        // Only fire attacker-trilateration on HIGH confidence to avoid kicking
        // legit gear that did a normal deauth+reconnect.
        if (w.forged && latencyMs <= EAPOL_BAIT_HIGH_MS) attacker_kick(w.src, "EAPOL_BAIT");
        return;
    }
}

static std::atomic<uint32_t> g_lastRealDeauthMs{0};
static std::atomic<uint32_t> g_lastForgedDeauthMs{0};

struct DeauthPeerMark { uint32_t lastMs; uint32_t lastBurstMs; };
static PsramMap<uint64_t, DeauthPeerMark> g_deauthPeerTs;
static constexpr size_t MAX_DEAUTH_PEER_MAP = 96;
static constexpr uint32_t DEAUTH_ATTRIB_WIN_MS = 8000;

struct DeauthPairEntry { uint32_t winStartMs; uint16_t count; };
static PsramMap<uint64_t, DeauthPairEntry> g_deauthPair;
static constexpr size_t MAX_DEAUTH_PAIR_MAP = 96;
static constexpr uint32_t DEAUTH_PAIR_WIN_MS = 1000;
static constexpr uint16_t DEAUTH_PAIR_THRESH = 12;

static void deauthNotePeer(uint64_t k, uint32_t now, bool burst) {
    if (g_deauthPeerTs.size() >= MAX_DEAUTH_PEER_MAP && g_deauthPeerTs.find(k) == g_deauthPeerTs.end()) {
        uint32_t oldest = UINT32_MAX;
        uint64_t oldestK = 0;
        for (const auto &kv : g_deauthPeerTs) if (kv.second.lastMs < oldest) { oldest = kv.second.lastMs; oldestK = kv.first; }
        g_deauthPeerTs.erase(oldestK);
    }
    DeauthPeerMark &m = g_deauthPeerTs[k];
    m.lastMs = now;
    if (burst) m.lastBurstMs = now;
}

static bool deauthBurstForPeer(uint64_t k, uint32_t now, uint32_t win) {
    auto it = g_deauthPeerTs.find(k);
    return it != g_deauthPeerTs.end() && it->second.lastBurstMs != 0 &&
           (now - it->second.lastBurstMs) < win;
}

// PMKID detection
// =============================================================================
// EAPOL-Key in 802.11: data frame ftype=2, LLC/SNAP DSAP=0xAA SSAP=0xAA ctrl=0x03,
// OUI 00:00:00, Ethertype 0x88 0x8E. Key descriptor starts after.
// PMKID-request M1 has: key_info: pairwise=1, ack=1, install=0, mic=0; key_data has
// PMKID KDE (00:0F:AC, type 4) or is broadcast-induced.
// We detect: EAPOL-Key from src targeting >=N distinct BSSIDs within window.

static void handleEAPOL(const DetectFrameEvent &e) {
    if (!g_hshkEnabled.load() && !g_pmkidEnabled.load()) return;
    if (e.len < 34) return;
    int eapolOff = -1;
    int searchEnd = (int)e.len - 8;
    for (int i = 24; i < searchEnd; ++i) {
        if (e.payload[i] == 0xAA && e.payload[i+1] == 0xAA && e.payload[i+2] == 0x03 &&
            e.payload[i+3] == 0x00 && e.payload[i+4] == 0x00 && e.payload[i+5] == 0x00 &&
            e.payload[i+6] == 0x88 && e.payload[i+7] == 0x8E) {
            eapolOff = i + 8;
            break;
        }
    }
    if (eapolOff < 0 || eapolOff + 16 >= (int)e.len) return;
    if (e.payload[eapolOff + 1] != 0x03) return;
    uint16_t keyInfo = ((uint16_t)e.payload[eapolOff + 5] << 8) | e.payload[eapolOff + 6];
    uint8_t msgNum = classifyEapolMsg(keyInfo);
    if (::g_detectVerbose.load()) {
        bool vkde = false; const uint8_t *vb = e.payload + eapolOff; int vbl = (int)e.len - eapolOff;
        static const uint8_t VK[6] = {0xDD,0x14,0x00,0x0F,0xAC,0x04};
        for (int i = 0; i + 6 <= vbl; ++i) if (!memcmp(vb + i, VK, 6)) { vkde = true; break; }
        Serial.printf("[VERIFY-PMKID] EAPOL M%u keyinfo=0x%04X len=%u pmkid_kde=%d ch=%u\n",
                      (unsigned)msgNum, keyInfo, (unsigned)e.len, vkde ? 1 : 0, (unsigned)e.channel);
    }

    // EAPOL capture-bait correlation: if an EAPOL handshake frame is observed
    // from a STA that was recently (≤30s) the unicast target of a deauth from
    // some src X, and X has stayed silent (no follow-up frames), that's the
    // classic "knock-the-client-off and sniff re-association" pattern tool
    // uses in its handshake/PMKID capture mode.
    {
        const uint8_t *sta = e.payload + 10;  // tentative — refined below by FC
        // Re-compute correct STA addr from FC ToDS/FromDS (matches earlier logic).
        uint16_t fcCheck = (uint16_t)e.payload[0] | ((uint16_t)e.payload[1] << 8);
        uint8_t toDsX   = (fcCheck >> 8) & 1;
        uint8_t fromDsX = (fcCheck >> 9) & 1;
        const uint8_t *a1X = e.payload + 4;
        const uint8_t *a2X = e.payload + 10;
        if (toDsX == 1 && fromDsX == 0) sta = a2X;       // STA → AP: STA is src
        else if (toDsX == 0 && fromDsX == 1) sta = a1X;  // AP → STA: STA is dst
        // else use default a2X
        const uint8_t *baitBssid = (toDsX == 1 && fromDsX == 0) ? a1X
                                 : (toDsX == 0 && fromDsX == 1) ? a2X
                                                                : (e.payload + 16);
        detect_correlateEapolBait(sta, baitBssid, e.rssi, e.channel);
    }

    // tool EAPOL bad-msg1 / forged PMKID — WiFiScan.cpp lines 7889-7939.
    // Body uses a FIXED 16-byte PMKID: 11 22 33 44 55 66 77 88 99 AA BB CC DD EE FF 11
    // preceded by PMKID KDE: DD 14 00 0F AC 04. Combined with Key Info 0x00CA (WPA2)
    // or 0x00CB (WPA3), this is unambiguous.
    if (g_pmkidEnabled.load() && (keyInfo == 0x00CA || keyInfo == 0x00CB)) {
        static const uint8_t FORGE_PMKID_TEMPLATE[16] = {
            0x11, 0x22, 0x33, 0x44, 0x55, 0x66, 0x77, 0x88,
            0x99, 0xAA, 0xBB, 0xCC, 0xDD, 0xEE, 0xFF, 0x11
        };
        static const uint8_t PMKID_KDE_HDR[6] = {0xDD, 0x14, 0x00, 0x0F, 0xAC, 0x04};
        const uint8_t *body = e.payload + eapolOff;
        int bodyLen = (int)e.len - eapolOff;
        bool sigHit = false;
        // Scan for `DD 14 00 0F AC 04` + 16 bytes matching FORGE_PMKID_TEMPLATE
        for (int i = 0; i + (int)sizeof(PMKID_KDE_HDR) + 16 <= bodyLen; ++i) {
            if (memcmp(body + i, PMKID_KDE_HDR, sizeof(PMKID_KDE_HDR)) != 0) continue;
            if (memcmp(body + i + sizeof(PMKID_KDE_HDR), FORGE_PMKID_TEMPLATE, 16) == 0) {
                sigHit = true;
                break;
            }
        }
        if (sigHit) {
            const uint8_t *src = e.payload + 10;
            const uint8_t *bss = e.payload + 4;  // dst in M1-from-AP path is STA, BSSID = src
            char srBuf[18], bsBuf[18];
            snprintf(srBuf, sizeof(srBuf), "%02X:%02X:%02X:%02X:%02X:%02X",
                     src[0],src[1],src[2],src[3],src[4],src[5]);
            snprintf(bsBuf, sizeof(bsBuf), "%02X:%02X:%02X:%02X:%02X:%02X",
                     bss[0],bss[1],bss[2],bss[3],bss[4],bss[5]);
            String sr(srBuf);
            String bs(bsBuf);
            char lineBuf[260];
            snprintf(lineBuf, sizeof(lineBuf),
                     "{\"src\":\"%s\",\"sta\":\"%s\",\"keyinfo\":\"0x%04X\",\"reason\":\"FORGE_PMKID\",\"rssi\":%d,\"ch\":%u,\"ts\":%u}",
                     srBuf, bsBuf, (unsigned)keyInfo, (int)e.rssi, (unsigned)e.channel, (unsigned)millis());
            logEventToSD("/pmkid_forge.jsonl", String(lineBuf));
            Serial.printf("[DETECT] PMKID_FORGE tool=MARAUDER src=%s sta=%s keyinfo=0x%04X ch=%u rssi=%d\n",
                          srBuf, bsBuf, (unsigned)keyInfo, (unsigned)e.channel, (int)e.rssi);
            ::detect_logIncident(String("PMKID_FORGE:") + sr + ":" + bs, nullptr);
            if (meshEnabled && meshRateGate(String("PMKID_FORGE_") + sr, 30000)) {
                char meshBuf[80];
                snprintf(meshBuf, sizeof(meshBuf), "%s: PMKID_FORGE:%s:%s:%d",
                         getNodeId().c_str(), srBuf, bsBuf, (int)e.rssi);
                sendToSerial1(String(meshBuf), true);
            }
            quorum_addReport("PMKID_FORGE", sr, getNodeId(), e.rssi);
            attacker_kick(src, "PMKID_FORGE");
        }
    }

    // injected M1 w/ zeroed ANonce (not hcxdumptool, it randomizes ANonce)
    if (g_pmkidEnabled.load() && msgNum == 1 && eapolOff + 49 <= (int)e.len) {
        bool zeroNonce = true;
        for (int n = eapolOff + 17; n < eapolOff + 49; ++n) { if (e.payload[n] != 0) { zeroNonce = false; break; } }
        if (zeroNonce) {
            const uint8_t *src = e.payload + 10;
            static PsramMap<uint64_t, uint32_t> s_fakeM1;
            uint64_t fk = packMac(src); uint32_t nowm = millis();
            auto fit = s_fakeM1.find(fk);
            if (fit == s_fakeM1.end() || (nowm - fit->second) > 30000) {
                if (s_fakeM1.size() >= 32) evictOldestTs(s_fakeM1);
                s_fakeM1[fk] = nowm;
                char sb[18];
                snprintf(sb, sizeof(sb), "%02X:%02X:%02X:%02X:%02X:%02X", src[0],src[1],src[2],src[3],src[4],src[5]);
                Serial.printf("[DETECT] PMKID_FORGE tool=ROGUE_M1 src=%s (zero ANonce)\n", sb);
                logEventToSD("/pmkid_forge.jsonl", String("{\"src\":\"") + sb + "\",\"reason\":\"FAKE_M1_ZERONONCE\",\"rssi\":" + String((int)e.rssi) + ",\"ch\":" + String((unsigned)e.channel) + ",\"ts\":" + String((unsigned)nowm) + "}");
                ::detect_logIncident(String("PMKID_FORGE:") + sb + ":FAKE_M1", nullptr);
                quorum_addReport("PMKID_FORGE", String(sb), getNodeId(), e.rssi);
                if (meshEnabled && meshRateGate(String("PMKID_FORGE_") + sb, 30000)) {
                    sendToSerial1(getNodeId() + ": PMKID_FORGE:" + sb + ":FAKE_M1:" + String((int)e.rssi), true);
                }
                attacker_kick(src, "PMKID_FORGE");
            }
        }
    }

    uint16_t fc = (uint16_t)e.payload[0] | ((uint16_t)e.payload[1] << 8);
    uint8_t toDs   = (fc >> 8) & 1;
    uint8_t fromDs = (fc >> 9) & 1;
    const uint8_t *a1 = e.payload + 4;
    const uint8_t *a2 = e.payload + 10;
    const uint8_t *a3 = e.payload + 16;
    const uint8_t *bssid;
    const uint8_t *sta;
    if (toDs == 0 && fromDs == 1) { bssid = a2; sta = a1; }
    else if (toDs == 1 && fromDs == 0) { bssid = a1; sta = a2; }
    else if (toDs == 0 && fromDs == 0) { bssid = a3; sta = a2; }
    else return;

    uint64_t replayCtr = 0;
    for (int i = 0; i < 8; ++i) replayCtr = (replayCtr << 8) | e.payload[eapolOff + 9 + i];

    uint32_t now = millis();
    std::lock_guard<std::recursive_mutex> lk(g_mtx);

    if (msgNum >= 1 && msgNum <= 4) {
        hshkRecord(bssid, sta, msgNum, replayCtr, e.rssi, getNodeId().c_str(), now);
    }
    if (g_hshkEnabled.load() && msgNum >= 1 && msgNum <= 4) {
        bool forced = deauthBurstForPeer(packMac(bssid), now, DEAUTH_ATTRIB_WIN_MS) ||
                      deauthBurstForPeer(packMac(sta), now, DEAUTH_ATTRIB_WIN_MS);
        bool authorized = false;
        const char *pair = nullptr;
        auto sess = g_hshk.find(eapolSessionKey(bssid, sta));
        if (sess != g_hshk.end()) pair = hshkUsablePair(sess->second, authorized);
        if (::g_detectVerbose.load() && pair && !forced) {
            Serial.printf("[VERIFY-HSHK] pair=%s %s bssid=%s sta=%s suppressed (no deauth burst)\n",
                          pair, authorized ? "authorized" : "challenge",
                          macStr(bssid).c_str(), macStr(sta).c_str());
        }
        if (pair && forced) {
            static PsramMap<uint64_t,uint32_t> s_hshkInc;
            uint64_t hk = eapolSessionKey(bssid, sta);
            auto hit = s_hshkInc.find(hk);
            if (hit == s_hshkInc.end() || (now - hit->second) > 30000) {
                if (s_hshkInc.size() >= 32) evictOldestTs(s_hshkInc);
                s_hshkInc[hk] = now;
                Serial.printf("[DETECT] HSHK bssid=%s sta=%s pair=%s %s (deauth-forced)\n",
                              macStr(bssid).c_str(), macStr(sta).c_str(), pair,
                              authorized ? "authorized" : "challenge");
                ::detect_logIncident(String("HSHK:") + macStr(bssid) + ":" + macStr(sta) + ":" + pair, nullptr);
            }
        }
        if (pair && forced && meshEnabled && sentinel_isRunning() && g_meshHshk.load() && meshRateGate("HSHK", 1000)) {
            sendToSerial1(getNodeId() + ": HSHK:" + macStr(bssid) + ":" + macStr(sta) +
                          ":" + String(msgNum) + ":" + String((unsigned long)replayCtr) +
                          ":" + String(e.rssi), true);
        }
    }

    if (msgNum != 1 || !g_pmkidEnabled.load()) return;

    // hcxdumptool M1 replay counter (hcxdumptool.c:5237)
    if (replayCtr >= 0xF000ULL && replayCtr <= 0xFFFEULL) {
        const uint8_t *ap = e.payload + 10;
        static PsramMap<uint64_t, uint32_t> s_hcxM1;
        uint64_t hcxK = packMac(ap);
        auto hcxIt = s_hcxM1.find(hcxK);
        if (hcxIt == s_hcxM1.end() || (now - hcxIt->second) > 30000) {
            if (s_hcxM1.size() >= 32) evictOldestTs(s_hcxM1);
            s_hcxM1[hcxK] = now;
            char hb[18];
            snprintf(hb, sizeof(hb), "%02X:%02X:%02X:%02X:%02X:%02X",
                     ap[0],ap[1],ap[2],ap[3],ap[4],ap[5]);
            String hs(hb);
            Serial.printf("[DETECT] PMKID_HARVEST tool=HCXDUMPTOOL src=%s rc=%u\n",
                          hb, (unsigned)replayCtr);
            logEventToSD("/pmkid.jsonl",
                         String("{\"src\":\"") + hb + "\",\"tool\":\"HCXDUMPTOOL\",\"reason\":\"M1_RC_RANGE\",\"rc\":" +
                         String((unsigned)replayCtr) + ",\"rssi\":" + String((int)e.rssi) +
                         ",\"ch\":" + String((unsigned)e.channel) + ",\"ts\":" + String((unsigned)now) + "}");
            ::detect_logIncident(String("PMKID_HARVEST:") + hs + ":HCXDUMPTOOL", nullptr);
            if (meshEnabled && sentinel_isRunning() && g_meshPmkid.load() &&
                meshRateGate(String("PMKID_HCX_") + hs, 30000)) {
                sendToSerial1(getNodeId() + ": PMKID_HARVEST:" + hs + ":HCXDUMPTOOL:" + String((int)e.rssi), true);
            }
            quorum_addReport("PMKID", hs, getNodeId(), e.rssi);
            attacker_kick(ap, "PMKID");
        }
    }

    const uint8_t *src = sta;
    if (bssid[0] & 0x02) return;

    bool kdePresent = false;
    {
        static const uint8_t KDE[6] = {0xDD,0x14,0x00,0x0F,0xAC,0x04};
        const uint8_t *body = e.payload + eapolOff;
        int bodyLen = (int)e.len - eapolOff;
        for (int i = 0; i + 22 <= bodyLen; ++i) {
            if (memcmp(body + i, KDE, 6) != 0) continue;
            for (int j = 0; j < 16; ++j) if (body[i + 6 + j]) { kdePresent = true; break; }
            break;
        }
    }
    uint64_t srcK = packMac(src);
    PmkidBurst &b = g_pmkidBursts[srcK];
    b.lastSeen = now;
    uint64_t bssK = packMac(bssid);
    b.bssidTs[bssK] = now;
    b.hshkKeys[bssK] = eapolSessionKey(bssid, src);
    if (kdePresent) b.kdeBssids.insert(bssK);
    uint16_t win = g_pmkidWindow.load();
    for (auto it = b.bssidTs.begin(); it != b.bssidTs.end(); ) {
        if (now - it->second > win) {
            b.hshkKeys.erase(it->first);
            b.kdeBssids.erase(it->first);
            it = b.bssidTs.erase(it);
        } else ++it;
    }
    uint8_t orphaned = 0;
    for (const auto &kv : b.bssidTs) {
        if ((now - kv.second) < PMKID_ORPHAN_SETTLE_MS) continue;
        auto hk = b.hshkKeys.find(kv.first);
        if (hk == b.hshkKeys.end()) continue;
        auto hs = g_hshk.find(hk->second);
        if (hs != g_hshk.end() && (hs->second.seenMask & 0x02) == 0) orphaned++;
    }
    bool fire = orphaned >= g_pmkidMinBssids.load();
    if (fire) {
        PmkidHarvestEvent ev{};
        memcpy(ev.srcMac, src, 6);
        memcpy(ev.bssid, bssid, 6);
        ev.rssi = e.rssi;
        ev.channel = e.channel;
        ev.ts = now;
        g_pmkidLog.push_back(ev);
        if (g_pmkidLog.size() > MAX_PMKID_LOG) g_pmkidLog.erase(g_pmkidLog.begin());

        char bsBuf[18], srBuf[18];
        snprintf(bsBuf, sizeof(bsBuf), "%02X:%02X:%02X:%02X:%02X:%02X",
                 bssid[0],bssid[1],bssid[2],bssid[3],bssid[4],bssid[5]);
        snprintf(srBuf, sizeof(srBuf), "%02X:%02X:%02X:%02X:%02X:%02X",
                 src[0],src[1],src[2],src[3],src[4],src[5]);
        String bs(bsBuf);
        String sr(srBuf);
        char lineBuf[280];
        snprintf(lineBuf, sizeof(lineBuf),
                 "{\"src\":\"%s\",\"bssid\":\"%s\",\"rssi\":%d,\"ch\":%u,\"ts\":%u,\"distinct_peers\":%u,\"orphan_m1\":%u,\"kde\":%s}",
                 srBuf, bsBuf, (int)ev.rssi, (unsigned)ev.channel, (unsigned)now,
                 (unsigned)b.bssidTs.size(), (unsigned)orphaned,
                 (b.kdeBssids.size() ? "true" : "false"));
        Serial.printf("[DETECT] PMKID_HARVEST sta=%s orphan_m1=%u peers=%u kde=%u\n",
                      srBuf, (unsigned)orphaned, (unsigned)b.bssidTs.size(),
                      (unsigned)b.kdeBssids.size());
        logEventToSD("/pmkid.jsonl", String(lineBuf));
        ::detect_logIncident(String("PMKID_HARVEST:") + sr + ":" + bs, nullptr);
        if (meshEnabled && sentinel_isRunning() && g_meshPmkid.load() && meshRateGate("PMKID_HARVEST", 5000)) {
            char meshBuf[80];
            snprintf(meshBuf, sizeof(meshBuf), "%s: PMKID_HARVEST:%s:%s:%d",
                     getNodeId().c_str(), srBuf, bsBuf, (int)ev.rssi);
            sendToSerial1(String(meshBuf), true);
        }
        quorum_addReport("PMKID", sr, getNodeId(), ev.rssi);
        attacker_kick(src, "PMKID");
        b.bssidTs.clear();
        b.hshkKeys.clear();
        b.kdeBssids.clear();
    }
}

// =============================================================================
// Beacon / Evil-Twin / SSID Confusion / OWE
// =============================================================================
// tool + tool static beacon-spam template fingerprint at TSF bytes 24-31.
// Both tools ship with this exact constant burned into their beacon template.
static const uint8_t BEACON_FORGERY_TSF[8] = {0x83, 0x51, 0xF7, 0x8F, 0x0F, 0x00, 0x00, 0x00};
// Bruce karma_attack.cpp:1285 sendBeaconFrameHelper — hardcoded rogue BSSID
static const uint8_t KARMA_BRUCE_BSSID[6] = {0x12, 0x34, 0x56, 0x78, 0x9A, 0xBC};
static PsramMap<uint64_t, uint32_t> g_beaconForgeFired;  // bssid -> reason mask seen
static constexpr size_t MAX_BEACON_FORGE_MAP = 64;

// Beacon-flood detector: counts DISTINCT BSSIDs seen in a rolling window.
// Real environments have a handful of APs; spam tools spew dozens of new
// BSSIDs/sec. This catches ALL beacon-flood tools (template-independent) and,
// while active, suppresses evil-twin/SSID-collision emits (those collisions are
// spam artifacts, not a real twin) -> fixes beacon-spam-as-EVILTWIN misclassify.
static PsramSet<uint64_t> g_beaconFloodBssids;
static uint32_t g_beaconFloodWinStart = 0;
static uint32_t g_beaconFloodLastEmit = 0;
static bool     g_beaconFloodActive = false;
static constexpr uint32_t BEACON_FLOOD_WIN_MS    = 10000;
static constexpr size_t   BEACON_FLOOD_DISTINCT  = 40;     // distinct NEAR BSSIDs/10s
static constexpr size_t   BEACON_FLOOD_MAP_CAP   = 256;
static constexpr uint32_t BEACON_FLOOD_COOLDOWN  = 10000;
// Only count beacons stronger than this. A beacon-spam attacker is in the room
// (-10..-40 dBm in tests); ambient/neighbor APs at -70..-90 are NOT spam. Without
// this gate a dense RF area trivially shows 25+ distinct BSSIDs -> false positive
// (observed firing at rssi=-82/-86). Gating to near beacons kills that FP.
static constexpr int8_t   BEACON_FLOOD_RSSI_MIN  = -65;

// Common Espressif OUI prefixes — found in nearly every tool/tool build
// because they run on ESP32-S3/C3. Used as confidence bump for Evil-Portal.
static const uint8_t ESP_OUIS[][3] = {
    {0x24,0x0A,0xC4}, {0x24,0x6F,0x28}, {0x30,0xAE,0xA4}, {0x3C,0x71,0xBF},
    {0x7C,0x9E,0xBD}, {0x84,0xF3,0xEB}, {0xAC,0x67,0xB2}, {0x84,0xCC,0xA8},
    {0xC8,0x2B,0x96}, {0xCC,0x50,0xE3}, {0xDC,0x54,0x75}, {0x30,0xC6,0xF7},
    {0x80,0x7D,0x3A}, {0x90,0x38,0x0C}, {0x8C,0xCE,0x4E}, {0x78,0xE3,0x6D},
    {0x78,0x21,0x84}, {0x7C,0xDF,0xA1}, {0x94,0xB9,0x7E}, {0x98,0xCD,0xAC},
    {0xA0,0xDD,0x6C}, {0xAC,0x0B,0xFB}, {0xB4,0x8A,0x0A}, {0xB8,0xD6,0x1A},
    {0xBC,0xDD,0xC2}, {0xC4,0xDD,0x57}, {0xD8,0xBC,0x38}, {0xE0,0x98,0x06},
    {0xE8,0x9F,0x6D}, {0xEC,0xDA,0x3B}, {0xF0,0x08,0xD1}, {0xF4,0xCF,0xA2},
    {0xF8,0xB7,0x62}, {0xFC,0xF5,0xC4},
};
static constexpr size_t ESP_OUI_COUNT = sizeof(ESP_OUIS) / sizeof(ESP_OUIS[0]);
static bool isEspOui(const uint8_t *mac) {
    for (size_t i = 0; i < ESP_OUI_COUNT; ++i) {
        if (memcmp(mac, ESP_OUIS[i], 3) == 0) return true;
    }
    return false;
}

// Captive-portal lure SSID substrings (lowercase).
// Hit any of these on an open AP and there is a strong chance of Evil-Portal.
static const char *LURE_SSIDS[] = {
    "free wifi", "free_wifi", "freewifi", "free internet",
    "guest", "public wifi", "public_wifi",
    "starbucks", "mcdonald", "airport", "hotel",
    "captive", "portal", "login", "wifi-auth", "wifi_auth", "wifi auth",
    "evil_portal", "evilportal", "phish",
    "xfinity", "attwifi", "att wi-fi", "spectrum",
};
static constexpr size_t LURE_SSID_COUNT = sizeof(LURE_SSIDS) / sizeof(LURE_SSIDS[0]);

static bool containsLureSsid(const char *ssid) {
    if (!ssid || !ssid[0]) return false;
    char lower[34] = {0};
    size_t n = strnlen(ssid, 32);
    for (size_t i = 0; i < n; ++i) {
        char c = ssid[i];
        lower[i] = (c >= 'A' && c <= 'Z') ? (c + ('a' - 'A')) : c;
    }
    for (size_t i = 0; i < LURE_SSID_COUNT; ++i) {
        if (strstr(lower, LURE_SSIDS[i])) return true;
    }
    return false;
}

static bool beaconHasCsaOrQuiet(const uint8_t *p, uint16_t len) {
    if (len < 36) return false;
    const uint8_t *ie = p + 36;
    uint16_t ieLen = len - 36, off = 0;
    while (off + 2 <= ieLen) {
        uint8_t t = ie[off], l = ie[off + 1];
        if ((size_t)off + 2 + l > (size_t)ieLen) break;
        if (t == 37 || t == 60 || t == 40) return true;
        off += 2 + l;
    }
    return false;
}

static const char *classifyBeaconForgery(const uint8_t *p, uint16_t len) {
    if (len < 36) return nullptr;
    if (memcmp(p + 10, KARMA_BRUCE_BSSID, 6) == 0) return "FORGE_KARMA_BRUCE";
    if (memcmp(p + 24, BEACON_FORGERY_TSF, 8) == 0) return "FORGE_TSF_STATIC";
    uint16_t bi = (uint16_t)p[32] | ((uint16_t)p[33] << 8);
    if (bi == 1000) return "FORGE_BI_1000";
    if (len > 36) {
        uint16_t off = 36;
        while (off + 2 <= len) {
            uint8_t tag = p[off];
            uint8_t l   = p[off + 1];
            if ((size_t)off + 2 + l > (size_t)len) break;
            // CSA IE value = {switch_mode, new_channel, switch_count}; the count is
            // the tell (Marauder WiFiScan.cpp:8523 post_csa = 25 03 01 00 ff).
            if (tag == 0x25 && l >= 3 && p[off + 4] == 0xFF) return "FORGE_CSA_FF";
            off += 2 + l;
        }
    }
    return nullptr;
}

static void emitBeaconForgery(const uint8_t *bssid, const char *ssid, uint16_t bi,
                              uint32_t ieHash, int8_t rssi, uint8_t channel,
                              const char *reason);

static uint8_t beaconAdvertisedChannel(const uint8_t *ie, uint16_t ieLen) {
    uint16_t off = 0;
    uint8_t dsChan = 0, htChan = 0;
    while (off + 2 <= ieLen) {
        uint8_t tag = ie[off];
        uint8_t len = ie[off + 1];
        if ((size_t)off + 2 + len > (size_t)ieLen) break;
        if (tag == 3 && len == 1)      dsChan = ie[off + 2];
        else if (tag == 61 && len >= 1) htChan = ie[off + 2];
        off += 2 + len;
    }
    if (dsChan) return dsChan;
    return htChan;
}

static void handleBeacon(const DetectFrameEvent &e) {
    if (e.len < 36) return;
    if (isSelfMac(e.payload + 10)) return;
    const uint8_t *bssid_early = e.payload + 16;
    bool isLaaBssid = (bssid_early[0] & 0x02) != 0;

    // --- Beacon-flood detection (distinct-BSSID churn). Runs before per-detector
    // gates so it catches spam regardless of which detectors are on.
    // CRITICAL: once a flood is active, do NOT keep logging/processing each spam
    // beacon — that per-frame String/SD/map work is what exhausts heap and crashes.
    // Detect once, alert (rate-gated), then bail out of the whole handler. ---
    {
        uint64_t bk = packMac(bssid_early);
        uint32_t tnow = millis();
        std::lock_guard<std::recursive_mutex> lkF(g_mtx);
        if (g_beaconFloodWinStart == 0 || (tnow - g_beaconFloodWinStart) > BEACON_FLOOD_WIN_MS) {
            g_beaconFloodWinStart = tnow;
            g_beaconFloodBssids.clear();
            g_beaconFloodActive = false;
        }
        if (!g_beaconFloodActive) {
            // Only count NEAR beacons. Ambient/neighbor APs (weak RSSI) are not spam.
            if (e.rssi >= BEACON_FLOOD_RSSI_MIN) {
                g_beaconFloodBssids.insert(bk);
                if (g_beaconFloodBssids.size() >= BEACON_FLOOD_DISTINCT) {
                    g_beaconFloodActive = true;
                    g_beaconFloodBssids.clear();   // free the set; flag carries state
                }
            }
        }
        if (g_beaconFloodActive) {
            // Rate-gated alert; everything else about this beacon is skipped.
            if (g_beaconFloodLastEmit == 0 || (tnow - g_beaconFloodLastEmit) > BEACON_FLOOD_COOLDOWN) {
                g_beaconFloodLastEmit = tnow;
                const char *floodTool = classifyBeaconForgery(e.payload, e.len);
                if (!floodTool) floodTool = "-";
                Serial.printf("[DETECT] BEACON_FLOOD active ch=%u rssi=%d tool=%s\n",
                              (unsigned)e.channel, (int)e.rssi, floodTool);
                ::detect_logIncident(String("BEACON_FLOOD:ch") + String(e.channel) + ":" + String((int)e.rssi) + "dBm", nullptr);
                char lb[200];
                snprintf(lb, sizeof(lb),
                         "{\"distinct_bssid\":%u,\"win_ms\":%u,\"ch\":%u,\"rssi\":%d,\"reason\":\"BEACON_FLOOD\",\"tool\":\"%s\",\"ts\":%u}",
                         (unsigned)BEACON_FLOOD_DISTINCT, (unsigned)BEACON_FLOOD_WIN_MS,
                         (unsigned)e.channel, (int)e.rssi, floodTool, (unsigned)tnow);
                logEventToSD("/eviltwin.jsonl", String(lb));
                if (floodTool[0] != '-') {
                    uint16_t fbi = (uint16_t)e.payload[32] | ((uint16_t)e.payload[33] << 8);
                    emitBeaconForgery(bssid_early, "", fbi, 0, e.rssi, e.channel, floodTool);
                }
                if (meshEnabled && sentinel_isRunning() && g_meshBeacon.load() && meshRateGate(String("BEACON_FLOOD"), 30000)) {
                    char mb[64];
                    snprintf(mb, sizeof(mb), "%s: BEACON_FLOOD:%d",
                             getNodeId().c_str(), (int)e.rssi);
                    sendToSerial1(String(mb), true);
                }
            }
            // Flood suppression must not hide a channel-switch / quiet DoS: those are
            // two integer reads and the emit below is rate-gated per BSSID.
            if (!beaconHasCsaOrQuiet(e.payload, e.len)) return;
        }
    }

    bool wantPwna = g_pwnaEnabled.load();
    bool wantEvil = g_eviltwinEnabled.load();
    bool wantTsf  = g_tsfEnabled.load();
    bool wantOwe  = g_oweEnabled.load();
    bool wantCsaQuiet = g_csaQuietEnabled.load();
    if (!wantPwna && !wantEvil && !wantTsf && !wantOwe && !wantCsaQuiet) return;
    const uint8_t *p = e.payload;
    const uint8_t *bssid = p + 16;
    uint64_t tsf = 0;
    for (int i = 0; i < 8; ++i) tsf |= ((uint64_t)p[24 + i]) << (8 * i);
    uint16_t beaconInt = (uint16_t)p[32] | ((uint16_t)p[33] << 8);
    const uint8_t *ie = p + 36;
    uint16_t ieLen = e.len - 36;

    if (wantCsaQuiet) {
        static PsramMap<uint64_t, uint32_t> s_csaQuietEmit;
        uint16_t coff = 0;
        const char *cqReason = nullptr;
        unsigned cqVal = 0;
        while (coff + 2 <= ieLen) {
            uint8_t ct = ie[coff];
            uint8_t cl = ie[coff + 1];
            if ((size_t)coff + 2 + cl > (size_t)ieLen) break;
            const uint8_t *cv = ie + coff + 2;
            if (ct == 37 && cl >= 3 && cv[2] >= 50) { cqReason = "CSA_SPOOF"; cqVal = cv[2]; break; }
            if (ct == 60 && cl >= 4 && cv[3] >= 50) { cqReason = "CSA_SPOOF"; cqVal = cv[3]; break; }
            if (ct == 40 && cl >= 6) {
                uint16_t qd = (uint16_t)cv[2] | ((uint16_t)cv[3] << 8);
                if (qd >= 1000) { cqReason = "QUIET_ABUSE"; cqVal = qd; break; }
            }
            coff += 2 + cl;
        }
        if (cqReason && !isSelfMac(bssid)) {
            uint64_t cqk = packMac(bssid);
            uint32_t cqnow = millis();
            auto cqit = s_csaQuietEmit.find(cqk);
            if (cqit == s_csaQuietEmit.end() || (cqnow - cqit->second) > 30000) {
                if (s_csaQuietEmit.size() >= 32) evictOldestTs(s_csaQuietEmit);
                s_csaQuietEmit[cqk] = cqnow;
                char cqb[18];
                snprintf(cqb, sizeof(cqb), "%02X:%02X:%02X:%02X:%02X:%02X",
                         bssid[0],bssid[1],bssid[2],bssid[3],bssid[4],bssid[5]);
                Serial.printf("[DETECT] %s src=%s val=%u ch=%u\n", cqReason, cqb, cqVal, (unsigned)e.channel);
                ::detect_logIncident(String(cqReason) + ":" + cqb + ":" + String(cqVal), nullptr);
                quorum_addReport(String(cqReason), String(cqb), getNodeId(), e.rssi);
                char cqline[200];
                snprintf(cqline, sizeof(cqline),
                         "{\"bssid\":\"%s\",\"reason\":\"%s\",\"value\":%u,\"rssi\":%d,\"ch\":%u,\"ts\":%u}",
                         cqb, cqReason, cqVal, (int)e.rssi, (unsigned)e.channel, (unsigned)cqnow);
                logEventToSD("/beacon_dos.jsonl", String(cqline));
                ::detect_logIncident(String(cqReason) + ":" + cqb + ":" + String(cqVal), nullptr);
                quorum_addReport(String(cqReason), String(cqb), getNodeId(), e.rssi);
                attacker_kick(bssid, cqReason);
                if (meshEnabled && sentinel_isRunning() && g_meshBeacon.load() &&
                    meshRateGate(String("CSAQ_") + cqb, 30000))
                    sendToSerial1(getNodeId() + ": " + cqReason + ":" + cqb + ":" + String(cqVal) +
                                  ":" + String((int)e.rssi), true);
            }
        }
    }

    // Evil-twin-of-us: any non-self BSSID beaconing OUR SSID is a clone of our AP.
    if (wantEvil) {
        char ssidSelf[33] = {0};
        extractSSID(ie, ieLen, ssidSelf, sizeof(ssidSelf));
        if (ssidSelf[0] && isSelfSsid(ssidSelf) && !isSelfMac(bssid) && !isSelfMac(p + 10)) {
            static PsramMap<uint64_t, uint32_t> s_selfCloneSeen;
            uint64_t ck = packMac(bssid);
            uint32_t nowc = millis();
            auto sit = s_selfCloneSeen.find(ck);
            if (sit == s_selfCloneSeen.end() || (nowc - sit->second) > 30000) {
                if (s_selfCloneSeen.size() >= 32) evictOldestTs(s_selfCloneSeen);
                s_selfCloneSeen[ck] = nowc;
                const char *rsn = hasOpenAuth(ie, ieLen) ? "SELF_CLONE_OPEN" : "SELF_CLONE";
                char bb[18];
                snprintf(bb, sizeof(bb), "%02X:%02X:%02X:%02X:%02X:%02X",
                         bssid[0],bssid[1],bssid[2],bssid[3],bssid[4],bssid[5]);
                Serial.printf("[DETECT] EVILTWIN src=%s reason=%s (clone of our AP) ssid=%s rssi=%d ch=%u\n",
                              bb, rsn, ssidSelf, (int)e.rssi, (unsigned)e.channel);
                char lb[220];
                snprintf(lb, sizeof(lb),
                         "{\"bssid\":\"%s\",\"ssid\":\"%s\",\"reason\":\"%s\",\"rssi\":%d,\"ch\":%u,\"ts\":%u}",
                         bb, ssidSelf, rsn, (int)e.rssi, (unsigned)e.channel, (unsigned)nowc);
                logEventToSD("/eviltwin.jsonl", String(lb));
                ::detect_logIncident(String("EVILTWIN:") + bb + ":" + rsn, nullptr);
                quorum_addReport("EVILTWIN", String(bb), getNodeId(), e.rssi);
                attacker_kick(bssid, "EVILTWIN");
                if (meshEnabled && sentinel_isRunning() && g_meshEviltwin.load() && meshRateGate(String("ETW_SELF_") + bb, 30000))
                    sendToSerial1(getNodeId() + ": EVILTWIN:" + bb + ":" + rsn + ":" + String((int)e.rssi) + ":" + ssidSelf, true);
            }
        }

        const char *forgeReason = classifyBeaconForgery(p, e.len);
        if (forgeReason) {
            char ssidLocal[33] = {0};
            extractSSID(ie, ieLen, ssidLocal, sizeof(ssidLocal));
            uint32_t ieH = hashIeSet(ie, ieLen);
            emitBeaconForgery(bssid, ssidLocal, beaconInt, ieH, e.rssi, e.channel, forgeReason);
        }

        // Evil-Portal heuristic — STRICT to avoid FP on legit captive portals
        // (hotels, airports, Starbucks). Require ALL THREE:
        //   1. open auth (no Privacy bit)
        //   2. lure-style SSID (Free WiFi, captive, portal, etc.)
        //   3. Espressif OUI source MAC
        // ESP32 doesn't run consumer/enterprise APs. ESP32 + open + lure SSID =
        // high-confidence Evil-Portal. Generic open+lure (no ESP) is too FP-heavy.
        {
            uint8_t capInfo0 = p[34];
            bool privacy = (capInfo0 & 0x10) != 0;
            if (!privacy && isEspOui(p + 10)) {
                char ssidEvp[33] = {0};
                extractSSID(ie, ieLen, ssidEvp, sizeof(ssidEvp));
                if (containsLureSsid(ssidEvp)) {
                    uint32_t ieH = hashIeSet(ie, ieLen);
                    emitBeaconForgery(bssid, ssidEvp, beaconInt, ieH, e.rssi, e.channel,
                                      "FORGE_EVIL_PORTAL_ESP");
                }
            }
        }

        // Behavioral fallback: per-src-MAC SSID rotation. Real APs broadcast ONE
        // SSID per BSSID. >=3 distinct SSIDs from same src MAC in 30s = bait,
        // catches tool/tool even if they evolve their template.
        //
        // Skip if Multi-BSSID IE (tag 71) is present — 802.11v/ax feature lets
        // one AP advertise multiple SSIDs from one BSSID legitimately.
        static PsramMap<uint64_t, std::pair<uint32_t, PsramSet<String>>> g_beaconSsidRotate;
        static constexpr size_t MAX_BEACON_ROTATE_MAP = 64;
        static constexpr uint32_t BEACON_ROTATE_WIN_MS = 5000;
        static constexpr uint8_t  BEACON_ROTATE_THRESH = 12;
        bool hasMBSSID = false;
        {
            uint16_t mo = 0;
            while (mo + 2 <= ieLen) {
                uint8_t t = ie[mo];
                uint8_t l = ie[mo + 1];
                if ((size_t)mo + 2 + l > (size_t)ieLen) break;
                if (t == 71) { hasMBSSID = true; break; }  // Multi-BSSID element
                mo += 2 + l;
            }
        }
        char ssidLocal2[33] = {0};
        extractSSID(ie, ieLen, ssidLocal2, sizeof(ssidLocal2));
        if (!hasMBSSID && ssidLocal2[0]) {
            uint64_t srcK = packMac(p + 10);
            uint32_t now2 = millis();
            std::lock_guard<std::recursive_mutex> lkR(g_mtx);
            auto rit = g_beaconSsidRotate.find(srcK);
            if (rit == g_beaconSsidRotate.end() || (now2 - rit->second.first) > BEACON_ROTATE_WIN_MS) {
                if (g_beaconSsidRotate.size() >= MAX_BEACON_ROTATE_MAP) {
                    evictOldestBy(g_beaconSsidRotate, [](const auto &v) { return v.first; });
                }
                g_beaconSsidRotate[srcK] = {now2, PsramSet<String>{String(ssidLocal2)}};
            } else {
                rit->second.second.insert(String(ssidLocal2));
                if (rit->second.second.size() == BEACON_ROTATE_THRESH) {
                    uint32_t ieH = hashIeSet(ie, ieLen);
                    emitBeaconForgery(p + 10, ssidLocal2, beaconInt, ieH, e.rssi, e.channel,
                                      "FORGE_SSID_ROTATE");
                }
            }
        }
    }

    if (isPwnagotchiBeacon(p, e.len)) {
        if (!wantPwna) return;
        std::lock_guard<std::recursive_mutex> lkP(g_mtx);
        pwnagotchiObserve(bssid, e.rssi, ie, ieLen);
        return;
    }

    if (!wantEvil && !wantOwe) return;

    char ssid[33] = {0};
    extractSSID(ie, ieLen, ssid, sizeof(ssid));
    uint32_t ieHash = hashIeSet(ie, ieLen);
    bool isOpen = hasOpenAuth(ie, ieLen);
    uint8_t oweTransBssid[6] = {0};
    bool hasOweTrans = extractOweTransition(ie, ieLen, oweTransBssid);

    if (isLaaBssid) return;

    uint64_t k = packMac(bssid);
    uint32_t now = millis();

    std::lock_guard<std::recursive_mutex> lk(g_mtx);
    static constexpr size_t MAX_AP_BASELINE = 96;
    if (g_apBaseline.size() >= MAX_AP_BASELINE && g_apBaseline.find(k) == g_apBaseline.end()) {
        uint32_t oldestTs = UINT32_MAX;
        uint64_t oldestK = 0;
        for (const auto &kv : g_apBaseline) {
            if (kv.second.lastSeen < oldestTs) {
                oldestTs = kv.second.lastSeen;
                oldestK = kv.first;
            }
        }
        if (oldestK) g_apBaseline.erase(oldestK);
    }
    auto it = g_apBaseline.find(k);
    if (it == g_apBaseline.end()) {
        ApBaseline b{};
        b.lastTSF = tsf;
        b.lastTSFSampleMs = now;
        b.beaconInterval = beaconInt;
        b.ieHash = ieHash;
        if (ssid[0] == 0 || ssidIsValid(ssid, strlen(ssid))) strncpy(b.ssid, ssid, sizeof(b.ssid) - 1);
        b.channel = e.channel;
        b.rssi = e.rssi;
        b.isOpen = isOpen;
        b.hasOweTransition = hasOweTrans;
        if (hasOweTrans) memcpy(b.oweTransitionBssid, oweTransBssid, 6);
        b.lastSeen = now;
        b.chanA = e.channel;
        b.chanAMs = now;
        g_apBaseline[k] = b;

        uint8_t hbuf[10];
        memcpy(hbuf, bssid, 6);
        memcpy(hbuf + 6, &ieHash, 4);
        g_localBloom.add(fnv1a(hbuf, 10));
        return;
    }

    ApBaseline &b = it->second;

    // Evil-twin: same BSSID advertising two DS/HT channels that keep alternating (both radios live); a legit CSA move stamps only the new channel.
    bool twinMultich = false;
    if (wantTsf) {
        uint8_t ch = beaconAdvertisedChannel(ie, ieLen);
        if (ch) {
            uint8_t prevNewest = (b.chanAMs >= b.chanBMs) ? 1 : 2;
            uint8_t stamped = 0;
            if (ch == b.chanA)      { b.chanAMs = now; stamped = 1; }
            else if (ch == b.chanB) { b.chanBMs = now; stamped = 2; }
            else if (b.chanA == 0)  { b.chanA = ch; b.chanAMs = now; stamped = 1; }
            else if (b.chanB == 0)  { b.chanB = ch; b.chanBMs = now; stamped = 2; }
            else if (b.chanAMs <= b.chanBMs) { b.chanA = ch; b.chanAMs = now; stamped = 1; }
            else                             { b.chanB = ch; b.chanBMs = now; stamped = 2; }
            bool bothFresh = b.chanA && b.chanB && b.chanA != b.chanB &&
                             (now - b.chanAMs < 5000UL) && (now - b.chanBMs < 5000UL);
            if (bothFresh && stamped != prevNewest) {
                if ((now - b.tsfViolWindowMs) > 15000UL) b.tsfViolStreak = 0;
                b.tsfViolWindowMs = now;
                if (b.tsfViolStreak < 255) b.tsfViolStreak++;
            } else if (!bothFresh) {
                b.tsfViolStreak = 0;
            }
            bool emitOk = (b.lastMultichEmitMs == 0) || ((now - b.lastMultichEmitMs) >= 300000UL);
            if (bothFresh && b.tsfViolStreak >= 4 && emitOk && !g_beaconFloodActive) {
                twinMultich = true;
                b.lastMultichEmitMs = now;
            }
        }
    }

    // Freshness gate: if baseline sample is stale (>30s old) we cannot trust
    // a TSF compare — channel-hop gap, AP rekey, or buffer-reorder dominates.
    bool baselineStale = (b.lastTSFSampleMs == 0) || ((now - b.lastTSFSampleMs) > 30000UL);

    // TSF_RESTART: TSF jumped back to ~0 (cloned-AP reboot / re-init).
    bool tsfRestart = !baselineStale && (tsf < b.lastTSF) && ((b.lastTSF - tsf) > 1000000000ULL);
    bool tsfNonMono = twinMultich;

    struct SsidWatch {
        uint32_t winStartMs{};
        uint32_t firstSeenMs{};
        uint8_t streak{};
        PsramSet<uint32_t> ouis;
        PsramSet<uint32_t> baseOuis;
        PsramSet<uint64_t> bssids;
        uint32_t lastFiredMs{};
    };
    static PsramMap<uint64_t, SsidWatch> g_ssidWatch;
    static constexpr size_t MAX_SSID_TRACK = 48;
    static constexpr uint32_t SSID_COLLISION_WIN_MS = 60000;
    static constexpr uint32_t SSID_FIRE_COOLDOWN_MS = 600000;
    static constexpr uint8_t  SSID_PERSIST_STREAK = 2;
    static constexpr size_t   MAX_TWIN_BSSIDS = 4;
    static constexpr uint32_t SSID_LEARN_MS = 300000;
    static constexpr size_t   MAX_BASE_OUIS = 8;

    bool ssidCollision = false;
    uint32_t collisionOuiCount = 0;
    uint32_t bssidOui = ((uint32_t)bssid[0] << 16) | ((uint32_t)bssid[1] << 8) | (uint32_t)bssid[2];

    // KARMA/MANA also advertise the harvested SSIDs by BEACON, not only by probe
    // response (Bruce karma_attack.cpp:1400 sendBeaconFrames, hostapd-mana likewise).
    // Same signature either way: one BSSID carrying multiple distinct SSIDs.
    if (g_karmaEnabled.load() && ssid[0] != 0 && !isSelfSsid(ssid)) {
        karma_observeProbeResp(bssid, ssid, e.rssi);
    }
    if (ssid[0] != 0 && !isSelfSsid(ssid)) {
        uint64_t ssidHash = fnv1a(reinterpret_cast<const uint8_t*>(ssid), strlen(ssid));
        auto sit = g_ssidWatch.find(ssidHash);
        if (sit == g_ssidWatch.end()) {
            if (g_ssidWatch.size() >= MAX_SSID_TRACK) {
                uint32_t oldestTs = UINT32_MAX;
                uint64_t oldestK = 0;
                for (const auto &kv : g_ssidWatch) {
                    if (kv.second.winStartMs < oldestTs) { oldestTs = kv.second.winStartMs; oldestK = kv.first; }
                }
                if (oldestK) g_ssidWatch.erase(oldestK);
            }
            SsidWatch sw{};
            sw.winStartMs = now;
            sw.firstSeenMs = now;
            sw.streak = 0;
            sw.lastFiredMs = 0;
            sw.ouis.insert(bssidOui);
            sw.baseOuis.insert(bssidOui);
            sw.bssids.insert(k);
            g_ssidWatch[ssidHash] = sw;
        } else {
            SsidWatch &sw = sit->second;
            if ((now - sw.winStartMs) > SSID_COLLISION_WIN_MS) {
                sw.winStartMs = now;
                sw.ouis.clear();
                sw.bssids.clear();
            }
            sw.ouis.insert(bssidOui);
            sw.bssids.insert(k);
            collisionOuiCount = sw.ouis.size();
            if ((now - sw.firstSeenMs) < SSID_LEARN_MS) {
                if (sw.baseOuis.size() < MAX_BASE_OUIS) sw.baseOuis.insert(bssidOui);
                sw.streak = 0;
            } else {
                bool newVendor = sw.baseOuis.find(bssidOui) == sw.baseOuis.end();
                bool ouiMismatch = newVendor && collisionOuiCount >= 2 && sw.bssids.size() <= MAX_TWIN_BSSIDS;
                bool cooldownPassed = (sw.lastFiredMs == 0) || ((now - sw.lastFiredMs) >= SSID_FIRE_COOLDOWN_MS);
                if (ouiMismatch && cooldownPassed) {
                    if (sw.streak < 255) sw.streak++;
                    if (sw.streak >= SSID_PERSIST_STREAK) {
                        ssidCollision = true;
                        sw.lastFiredMs = now;
                        sw.streak = 0;
                        if (sw.baseOuis.size() < MAX_BASE_OUIS) sw.baseOuis.insert(bssidOui);
                    }
                } else if (!ouiMismatch) {
                    sw.streak = 0;
                }
            }
        }
    }

    uint32_t cooldownMs = (tsfNonMono || tsfRestart || ssidCollision) ? 300000UL : 60000UL;
    bool cooldownOk = (b.lastEvilEmitMs == 0) || ((now - b.lastEvilEmitMs) >= cooldownMs);

    // Suppress evil-twin emit during an active beacon flood: SSID collisions and
    // TSF anomalies under flood are spam artifacts (random BSSIDs reusing SSIDs),
    // not a real twin. BEACON_FLOOD already reported the attack.
    bool anySignal = tsfNonMono || tsfRestart || ssidCollision;
    bool meshWorthy = tsfNonMono || ssidCollision;
    if (anySignal && cooldownOk && !g_beaconFloodActive) {
        EvilTwinEvent ev{};
        memcpy(ev.bssid, bssid, 6);
        strncpy(ev.ssid, ssid, sizeof(ev.ssid) - 1);
        ev.oldTSF = b.lastTSF;
        ev.newTSF = tsf;
        ev.oldIeHash = b.ieHash;
        ev.newIeHash = ieHash;
        ev.oldBeaconInt = b.beaconInterval;
        ev.newBeaconInt = beaconInt;
        ev.rssi = e.rssi;
        ev.channel = e.channel;
        ev.ts = now;
        if (ssidCollision) strncpy(ev.reason, "SSID_COLLISION", sizeof(ev.reason) - 1);
        else if (tsfNonMono) strncpy(ev.reason, "TWIN_MULTICH", sizeof(ev.reason) - 1);
        else strncpy(ev.reason, "TSF_RESTART", sizeof(ev.reason) - 1);

        g_evilTwinLog.push_back(ev);
        if (g_evilTwinLog.size() > MAX_ET_LOG) g_evilTwinLog.erase(g_evilTwinLog.begin());

        char bs[18];
        snprintf(bs, sizeof(bs), "%02X:%02X:%02X:%02X:%02X:%02X",
                 bssid[0],bssid[1],bssid[2],bssid[3],bssid[4],bssid[5]);
        char jsonLine[320];
        snprintf(jsonLine, sizeof(jsonLine),
                 "{\"bssid\":\"%s\",\"ssid\":\"%s\",\"reason\":\"%s\",\"ouis\":%u,\"rssi\":%d,\"ch\":%u,\"ts\":%u}",
                 bs, ev.ssid, ev.reason, (unsigned)collisionOuiCount,
                 (int)ev.rssi, (unsigned)ev.channel, (unsigned)now);
        logEventToSD("/eviltwin.jsonl", String(jsonLine));
        Serial.printf("[DETECT] EVILTWIN src=%s reason=%s ssid=%s ouis=%u rssi=%d ch=%u\n",
                      bs, ev.reason, ev.ssid, (unsigned)collisionOuiCount,
                      (int)ev.rssi, (unsigned)ev.channel);
        String bsStr(bs);
        if (meshWorthy) {
            bool isTsfReason = tsfNonMono && !ssidCollision;
            bool meshFlag = isTsfReason ? g_meshTsf.load() : g_meshEviltwin.load();
            if (meshEnabled && sentinel_isRunning() && meshFlag && meshRateGate(String("EVILTWIN_") + bsStr, 10000)) {
                char meshMsg[128];
                snprintf(meshMsg, sizeof(meshMsg), "%s: EVILTWIN:%s:%s:%d:%s",
                         getNodeId().c_str(), bs, ev.reason, (int)ev.rssi, ev.ssid);
                sendToSerial1(String(meshMsg), true);
            }
            ::detect_logIncident(String("EVILTWIN:") + bsStr + ":" + ev.reason, nullptr);
            quorum_addReport("EVILTWIN", bsStr, getNodeId(), ev.rssi);
        }
        b.lastEvilEmitMs = now;
        b.tsfViolStreak = 0;
        b.tsfViolWindowMs = 0;
    }

    // OWE transition abuse: open beacon on SSID that matches an OWE-tagged BSSID without
    // being its declared transition partner.
    if (isOpen && !hasOweTrans) {
        for (const auto &kv : g_apBaseline) {
            const ApBaseline &other = kv.second;
            if (other.hasOweTransition && strcmp(other.ssid, ssid) == 0) {
                if (memcmp(other.oweTransitionBssid, bssid, 6) != 0) {
                    OweAbuseEvent ev{};
                    memcpy(ev.openBssid, bssid, 6);
                    unpackMac(kv.first, ev.oweBssid);
                    strncpy(ev.ssid, ssid, sizeof(ev.ssid) - 1);
                    ev.rssi = e.rssi;
                    ev.channel = e.channel;
                    ev.ts = now;
                    g_oweAbuseLog.push_back(ev);
                    if (g_oweAbuseLog.size() > MAX_OWE_LOG) g_oweAbuseLog.erase(g_oweAbuseLog.begin());
                    char obBuf[18], owbBuf[18];
                    snprintf(obBuf, sizeof(obBuf), "%02X:%02X:%02X:%02X:%02X:%02X",
                             bssid[0],bssid[1],bssid[2],bssid[3],bssid[4],bssid[5]);
                    snprintf(owbBuf, sizeof(owbBuf), "%02X:%02X:%02X:%02X:%02X:%02X",
                             ev.oweBssid[0],ev.oweBssid[1],ev.oweBssid[2],ev.oweBssid[3],ev.oweBssid[4],ev.oweBssid[5]);
                    const char *safeSsid = ssidIsValid(ssid, strlen(ssid)) ? ssid : "";
                    char lineBuf[260];
                    snprintf(lineBuf, sizeof(lineBuf),
                             "{\"open_bssid\":\"%s\",\"owe_bssid\":\"%s\",\"ssid\":\"%s\",\"rssi\":%d,\"ch\":%u,\"ts\":%u}",
                             obBuf, owbBuf, safeSsid, (int)e.rssi, (unsigned)e.channel, (unsigned)now);
                    logEventToSD("/owe_abuse.jsonl", String(lineBuf));
                    Serial.printf("[DETECT] OWE_ABUSE src=%s owe_ap=%s ssid=%s rssi=%d ch=%u\n",
                                  obBuf, owbBuf, safeSsid, (int)e.rssi, (unsigned)e.channel);
                    ::detect_logIncident(String("OWE_ABUSE:") + obBuf + ":" + safeSsid, nullptr);
                    if (meshEnabled && sentinel_isRunning() && g_meshOwe.load() && meshRateGate(String("OWE_ABUSE_") + obBuf, 30000))
                        sendToSerial1(getNodeId() + ": OWE_ABUSE:" + obBuf + ":" + safeSsid + ":" + String((int)e.rssi), true);
                    break;
                }
            }
        }
    }

    // Update baseline state
    b.lastTSF = tsf;
    b.lastTSFSampleMs = now;
    b.beaconInterval = beaconInt;
    b.ieHash = ieHash;
    if (ssid[0] == 0 || ssidIsValid(ssid, strlen(ssid))) strncpy(b.ssid, ssid, sizeof(b.ssid) - 1);
    b.channel = e.channel;
    b.rssi = e.rssi;
    b.isOpen = isOpen;
    b.hasOweTransition = hasOweTrans;
    if (hasOweTrans) memcpy(b.oweTransitionBssid, oweTransBssid, 6);
    b.lastSeen = now;
}

// Beacon-forgery emitter — fires once per (BSSID, reason) per session to avoid spam.
static void emitBeaconForgery(const uint8_t *bssid, const char *ssid, uint16_t bi,
                              uint32_t ieHash, int8_t rssi, uint8_t channel,
                              const char *reason) {
    uint64_t k = packMac(bssid);
    uint32_t reasonBit = 0;
    uint8_t reasonIdx = 0;
    if      (strcmp(reason, "FORGE_TSF_STATIC") == 0) { reasonBit = 0x01; reasonIdx = 0; }
    else if (strcmp(reason, "FORGE_BI_1000")    == 0) { reasonBit = 0x02; reasonIdx = 1; }
    else if (strcmp(reason, "FORGE_SRC_MCAST")  == 0) { reasonBit = 0x04; reasonIdx = 2; }
    else if (strcmp(reason, "FORGE_CSA_FF")     == 0) { reasonBit = 0x08; reasonIdx = 3; }
    else if (strcmp(reason, "FORGE_QUIET_ELEM") == 0) { reasonBit = 0x10; reasonIdx = 4; }
    else if (strcmp(reason, "FORGE_SSID_ROTATE") == 0) { reasonBit = 0x20; reasonIdx = 5; }
    else if (strcmp(reason, "FORGE_EVIL_PORTAL")  == 0) { reasonBit = 0x40; reasonIdx = 6; }
    else if (strcmp(reason, "FORGE_EVIL_PORTAL_ESP") == 0) { reasonBit = 0x80; reasonIdx = 7; }
    else if (strcmp(reason, "FORGE_KARMA_BRUCE") == 0) { reasonBit = 0x100; reasonIdx = 8; }
    std::lock_guard<std::recursive_mutex> lk(g_mtx);

    // GLOBAL per-reason rate gate. Beacon spam randomizes BSSID every frame, so the
    // per-BSSID dedup below never triggers -> without this, a flood causes one
    // SD-write + String-alloc PER beacon (hundreds/sec) -> heap exhaustion -> crash.
    // Collapse a flood to one emit per cooldown while still flagging the attack.
    static uint32_t s_lastEmitMs[9] = {0};
    uint32_t nowMs = millis();
    if (s_lastEmitMs[reasonIdx] != 0 && (nowMs - s_lastEmitMs[reasonIdx]) < 5000) return;

    auto it = g_beaconForgeFired.find(k);
    if (it != g_beaconForgeFired.end() && (it->second & reasonBit)) return;  // already reported
    if (g_beaconForgeFired.size() >= MAX_BEACON_FORGE_MAP) {
        // Evict an arbitrary entry; this set is bounded for memory safety only.
        g_beaconForgeFired.erase(g_beaconForgeFired.begin());
    }
    g_beaconForgeFired[k] |= reasonBit;
    s_lastEmitMs[reasonIdx] = nowMs;

    EvilTwinEvent ev{};
    memcpy(ev.bssid, bssid, 6);
    strncpy(ev.ssid, ssid, sizeof(ev.ssid) - 1);
    ev.oldBeaconInt = 0;
    ev.newBeaconInt = bi;
    ev.oldIeHash = 0;
    ev.newIeHash = ieHash;
    ev.rssi = rssi;
    ev.channel = channel;
    ev.ts = millis();
    strncpy(ev.reason, reason, sizeof(ev.reason) - 1);
    g_evilTwinLog.push_back(ev);
    if (g_evilTwinLog.size() > MAX_ET_LOG) g_evilTwinLog.erase(g_evilTwinLog.begin());

    char bs[18];
    snprintf(bs, sizeof(bs), "%02X:%02X:%02X:%02X:%02X:%02X",
             bssid[0],bssid[1],bssid[2],bssid[3],bssid[4],bssid[5]);
    char jsonLine[280];
    snprintf(jsonLine, sizeof(jsonLine),
             "{\"bssid\":\"%s\",\"ssid\":\"%s\",\"reason\":\"%s\",\"bi\":%u,\"ie\":%u,\"rssi\":%d,\"ch\":%u,\"ts\":%u}",
             bs, ev.ssid, ev.reason, (unsigned)bi, (unsigned)ieHash,
             (int)rssi, (unsigned)channel, (unsigned)ev.ts);
    logEventToSD("/eviltwin.jsonl", String(jsonLine));
    String bsStr(bs);
    ::detect_logIncident(String("BEACON_FORGE:") + bs + ":" + reason + ":" + String((int)rssi), nullptr);
    if (meshEnabled && sentinel_isRunning() && g_meshEviltwin.load() && meshRateGate(String("BEACON_FORGE_REASON_") + reason, 30000)) {
        char meshMsg[80];
        snprintf(meshMsg, sizeof(meshMsg), "%s: BEACON_FORGE:%s:%s:%d",
                 getNodeId().c_str(), bs, reason, (int)rssi);
        sendToSerial1(String(meshMsg), true);
    }
    quorum_addReport("BEACON_FORGE", bsStr, getNodeId(), rssi);
}

// =============================================================================
// Assoc-Sleep / tool assoc attack — sends assoc-request frames with the
// PM (power-management) bit set in frame-control byte 1, from random STA MACs
// to a target AP, every 200ms (WiFiScan.cpp:7987-8112). Distinguishes from
// legit clients because real STAs negotiate sleep AFTER association.
// Detection: per-BSSID, count distinct src MACs sending assoc-req with PM bit
// in a 5s window. >=4 distinct = alert.
// =============================================================================
struct AssocSleepWindow {
    uint32_t windowStartMs{};
    PsramSet<uint64_t> distinctSrc;
    uint16_t frames{};
    int8_t bestRssi{};
    uint8_t channel{};
    bool alerted{};
};
static PsramMap<uint64_t, AssocSleepWindow> g_assocSleep;
static constexpr size_t MAX_ASSOC_SLEEP_MAP = 32;
static constexpr uint16_t ASSOC_SLEEP_WIN_MS = 5000;
static constexpr uint8_t  ASSOC_SLEEP_THRESH = 4;   // distinct spoofed src (multi-client)
static constexpr uint16_t ASSOC_SLEEP_FRAMES = 8;   // PM-bit assoc-req rate (catches 1-MAC flood)
static std::atomic<bool> g_assocSleepEnabled{true};

struct DeauthRateEntry {
    uint32_t winStartMs;
    uint16_t count;
    bool alerted;
    // Per-tool behavioral trackers (see docs/detector-verification.md §1)
    uint16_t lastSeqNum;     // last sequence number (seqCtrl>>4)
    uint8_t  sawtoothHits;   // consecutive 0..63 incrementing seqs (bettercap)
    uint8_t  lastSubtype;    // 0x0C deauth / 0x0A disassoc
    uint8_t  altHits;        // consecutive deauth<->disassoc alternations (mdk4)
    uint8_t  reason7Hits;    // reason=7 + dur=0x013A frames (aireplay)
    uint16_t deauthReason;   // 0xFFFF = unseen
    uint16_t disassocReason; // 0xFFFF = unseen
    bool     toolAlerted;    // emitted a per-tool forge alert this window
    uint32_t lastFrameMs;
    uint32_t lastEpoch;      // channel dwell the previous frame arrived in
    uint32_t gapSumMs;
    uint16_t gapSamples;
};
static PsramMap<uint64_t, DeauthRateEntry> g_deauthRate;
static constexpr size_t MAX_DEAUTH_RATE_MAP = 64;
static constexpr uint32_t DEAUTH_FLOOD_WIN_MS = 10000;
static constexpr uint16_t DEAUTH_FLOOD_THRESH = 20;
static constexpr uint32_t DEAUTH_RATE_GAP_MS = 150;   // slowest verified injector sends every 40ms
static constexpr uint16_t DEAUTH_RATE_MIN_GAPS = 8;
static constexpr uint32_t DEAUTH_ALERT_COOLDOWN_MS = 60000;
static std::atomic<uint32_t> g_deauthRetryDrops{0};
static std::atomic<uint32_t> g_chanEpoch{0};          // bumped when the RX channel changes

// Classify a deauth/disassoc frame against verified per-tool source fingerprints.
// Returns a static tool tag or nullptr. Single-frame static checks only.
//   reason: frame reason code   seqCtrl: raw seq-control field
//   durLE: duration field (bytes 2-3, little-endian)   subtype: 0x0C or 0x0A
static const char *classifyDeauthTool(uint16_t reason, uint16_t seqCtrl, uint16_t durLE) {
    // ESP32Marauder WiFiScan.h:491 — reason=2, seqCtrl=0xFFF0 (fixed)
    if (reason == 0x0002 && seqCtrl == 0xFFF0) return "MARAUDER";
    if (reason == 0x000E) return "MICHAEL_TKIP";
    // reason=7+dur=0x013A is aireplay; bettercap is reason=6+dur=0 — both behavioral.
    return nullptr;
}

static void handleDeauthFrame(const DetectFrameEvent &e) {
    if (e.len < 26) return;
    const uint8_t *p = e.payload;
    if (p[1] & 0x08) { g_deauthRetryDrops.fetch_add(1, std::memory_order_relaxed); return; }  // retransmit
    const uint8_t *dst = p + 4;
    const uint8_t *src = p + 10;
    bool selfSrc = isSelfMac(src);
    bool sentinelHop = ::sentinel_isRunning();
    if (!selfSrc) g_lastRealDeauthMs.store(millis());
    uint16_t durLE   = (uint16_t)p[2]  | ((uint16_t)p[3]  << 8);
    uint16_t seqCtrl = (uint16_t)p[22] | ((uint16_t)p[23] << 8);
    uint16_t seqNum  = seqCtrl >> 4;
    uint8_t  subtype = (p[0] >> 4) & 0x0F;   // 0x0C deauth, 0x0A disassoc
    uint16_t reason  = (uint16_t)p[24] | ((uint16_t)p[25] << 8);
    bool isBroadcast = (dst[0] == 0xFF && dst[1] == 0xFF && dst[2] == 0xFF &&
                        dst[3] == 0xFF && dst[4] == 0xFF && dst[5] == 0xFF);
    const char *toolTag = classifyDeauthTool(reason, seqCtrl, durLE);
    bool forgeFingerprint = (toolTag != nullptr);
    if (forgeFingerprint) g_lastForgedDeauthMs.store(millis());
    if (::g_detectVerbose.load()) {
        Serial.printf("[VERIFY-DEAUTH] src=%02X:%02X:%02X:%02X:%02X:%02X subtype=0x%02X reason=%u seq=0x%04X dur=0x%04X bcast=%d tool=%s selfSrc=%d\n",
                      src[0],src[1],src[2],src[3],src[4],src[5], subtype, reason, seqCtrl, durLE,
                      isBroadcast?1:0, toolTag?toolTag:"-", selfSrc?1:0);
    }
    uint32_t now = millis();
    std::lock_guard<std::recursive_mutex> lk(g_mtx);
    bool pairBurst = false;
    {
        uint64_t pairK = packMac(src) ^ (packMac(dst) * 0x9E3779B97F4A7C15ULL);
        auto pit = g_deauthPair.find(pairK);
        if (pit == g_deauthPair.end() || (now - pit->second.winStartMs) > DEAUTH_PAIR_WIN_MS) {
            if (g_deauthPair.size() >= MAX_DEAUTH_PAIR_MAP) {
                uint32_t oldest = UINT32_MAX;
                uint64_t oldestK = 0;
                for (const auto &kv : g_deauthPair) if (kv.second.winStartMs < oldest) { oldest = kv.second.winStartMs; oldestK = kv.first; }
                g_deauthPair.erase(oldestK);
            }
            DeauthPairEntry ne{};
            ne.winStartMs = now;
            ne.count = 1;
            g_deauthPair[pairK] = ne;
        } else {
            DeauthPairEntry &pe = pit->second;
            if (pe.count < 65535) pe.count++;
            pairBurst = pe.count >= DEAUTH_PAIR_THRESH;
        }
    }
    bool attribBurst = pairBurst || forgeFingerprint;
    if (!selfSrc || forgeFingerprint) {
        detect_witnessDeauth(src, dst, e.rssi, e.channel, forgeFingerprint);
        deauthNotePeer(packMac(src), now, attribBurst);
        deauthNotePeer(packMac(p + 16), now, attribBurst);
        if (!isBroadcast) deauthNotePeer(packMac(dst), now, attribBurst);
    }
    uint64_t k = packMac(src);
    auto it = g_deauthRate.find(k);
    if (it == g_deauthRate.end() || (now - it->second.winStartMs) > DEAUTH_FLOOD_WIN_MS) {
        if (g_deauthRate.size() >= MAX_DEAUTH_RATE_MAP) {
            uint32_t oldest = UINT32_MAX; uint64_t oldestK = 0;
            for (const auto &kv : g_deauthRate) if (kv.second.winStartMs < oldest) { oldest = kv.second.winStartMs; oldestK = kv.first; }
            g_deauthRate.erase(oldestK);
        }
        DeauthRateEntry ne{};
        ne.winStartMs = now;
        ne.count = 1;
        ne.alerted = false;
        ne.lastSeqNum = seqNum;
        ne.lastSubtype = subtype;
        ne.lastFrameMs = now;
        ne.lastEpoch = g_chanEpoch.load(std::memory_order_relaxed);
        ne.deauthReason   = (subtype == 0x0C) ? reason : 0xFFFF;
        ne.disassocReason = (subtype == 0x0A) ? reason : 0xFFFF;
        g_deauthRate[k] = ne;
    } else {
        DeauthRateEntry &r = it->second;
        if (r.count < 65535) r.count++;
        uint32_t epoch = g_chanEpoch.load(std::memory_order_relaxed);
        if (epoch == r.lastEpoch && r.gapSamples < 65535) {
            r.gapSumMs += (now - r.lastFrameMs);
            r.gapSamples++;
        }
        r.lastFrameMs = now;
        r.lastEpoch = epoch;
        // bettercap: seq walks 0..63 then resets (wifi_deauth.go:14). Count monotonic increments.
        if (seqNum == (uint16_t)(r.lastSeqNum + 1) && seqNum <= 0x003F) {
            if (r.sawtoothHits < 255) r.sawtoothHits++;
        } else if (seqNum != r.lastSeqNum) {
            r.sawtoothHits = 0;
        }
        r.lastSeqNum = seqNum;
        // mdk4 mode d: alternating deauth(0x0C) <-> disassoc(0x0A) pairs (deauth.c:443-466).
        if ((subtype == 0x0C || subtype == 0x0A) && subtype != r.lastSubtype) {
            if (r.altHits < 255) r.altHits++;
        }
        r.lastSubtype = subtype;
        if (subtype == 0x0C) r.deauthReason = reason;
        else if (subtype == 0x0A) r.disassocReason = reason;
        if (reason == 0x0007 && durLE == 0x013A) {
            if (r.reason7Hits < 255) r.reason7Hits++;
        }
        if (!r.toolAlerted && !(selfSrc && sentinelHop)) {
            const char *behavTool = nullptr;
            if (r.altHits >= 6) {
                // mdk4 varies reason per subtype; ESP deauthers reuse one reason
                bool bothSeen = r.deauthReason != 0xFFFF && r.disassocReason != 0xFFFF;
                behavTool = (bothSeen && r.deauthReason != r.disassocReason)
                                ? "MDK4" : "ESP_DEAUTHER";
            }
            else if (r.reason7Hits >= 12) behavTool = "AIREPLAY";
            else if (r.sawtoothHits >= 8) behavTool = "BETTERCAP";
            if (behavTool) {
                r.toolAlerted = true;
                char sb[18];
                snprintf(sb, sizeof(sb), "%02X:%02X:%02X:%02X:%02X:%02X",
                         src[0],src[1],src[2],src[3],src[4],src[5]);
                Serial.printf("[DETECT] DEAUTH_FORGE tool=%s src=%s (behavioral)\n", behavTool, sb);
                char lb[200];
                snprintf(lb, sizeof(lb),
                         "{\"src\":\"%s\",\"tool\":\"%s\",\"class\":\"behavioral\",\"rssi\":%d,\"ch\":%u,\"ts\":%u}",
                         sb, behavTool, (int)e.rssi, (unsigned)e.channel, (unsigned)now);
                logEventToSD("/deauth_flood.jsonl", String(lb));
                if (meshEnabled && (sentinel_isRunning() || deauthDetectionEnabled.load()) && g_meshDeauth.load() && meshRateGate(String("DEAUTH_TOOL_") + sb, 30000)) {
                    char mb[80];
                    snprintf(mb, sizeof(mb), "%s: DEAUTH_FORGE:%s:%s:%d",
                             getNodeId().c_str(), sb, behavTool, (int)e.rssi);
                    sendToSerial1(String(mb), true);
                }
                ::detect_logIncident(String("DEAUTH_FORGE:") + sb + ":" + behavTool, nullptr);
                quorum_addReport("DEAUTH_FORGE", String(sb), getNodeId(), e.rssi);
                attacker_kick(src, "DEAUTH_FORGE");
            }
        }
        uint32_t meanGap = r.gapSamples ? (r.gapSumMs / r.gapSamples) : UINT32_MAX;
        bool floodRate = r.count >= DEAUTH_FLOOD_THRESH && r.gapSamples >= DEAUTH_RATE_MIN_GAPS &&
                         meanGap <= DEAUTH_RATE_GAP_MS;
        bool suppressSelfBurst = selfSrc && sentinelHop && !forgeFingerprint &&
                                 (r.count < (DEAUTH_FLOOD_THRESH * 2));
        bool bcastAttack = isBroadcast && pairBurst && !selfSrc;
        static PsramMap<uint64_t, uint32_t> g_deauthFloodEmit;
        auto fem = g_deauthFloodEmit.find(k);
        bool floodEmitOk = (fem == g_deauthFloodEmit.end()) || ((now - fem->second) >= DEAUTH_ALERT_COOLDOWN_MS);
        if (!r.alerted && (floodRate || bcastAttack) && !suppressSelfBurst && floodEmitOk) {
            r.alerted = true;
            if (g_deauthFloodEmit.size() >= MAX_DEAUTH_RATE_MAP) evictOldestTs(g_deauthFloodEmit);
            g_deauthFloodEmit[k] = now;
            char srcBuf[18];
            snprintf(srcBuf, sizeof(srcBuf), "%02X:%02X:%02X:%02X:%02X:%02X",
                     src[0],src[1],src[2],src[3],src[4],src[5]);
            String srcS(srcBuf);
            Serial.printf("[DETECT] DEAUTH_FLOOD src=%s count=%u in %ums gap=%ums/%u retrydrop=%u (reason=%u seq=0x%04X bcast=%d%s)\n",
                          srcBuf, r.count, (unsigned)(now - r.winStartMs),
                          (unsigned)(r.gapSamples ? r.gapSumMs / r.gapSamples : 0), (unsigned)r.gapSamples,
                          (unsigned)g_deauthRetryDrops.load(std::memory_order_relaxed),
                          (unsigned)reason, seqCtrl, (int)isBroadcast,
                          selfSrc ? " IMPERSONATION" : "");
            char lineBuf[380];
            snprintf(lineBuf, sizeof(lineBuf),
                     "{\"src\":\"%s\",\"count\":%u,\"win_ms\":%u,\"gap_ms\":%u,\"gap_n\":%u,\"reason\":%u,\"seq\":%u,\"bcast\":%s,\"rssi\":%d,\"ch\":%u,\"ts\":%u}",
                     srcBuf, (unsigned)r.count, (unsigned)(now - r.winStartMs),
                     (unsigned)(r.gapSamples ? r.gapSumMs / r.gapSamples : 0), (unsigned)r.gapSamples,
                     (unsigned)reason, (unsigned)seqCtrl, isBroadcast ? "true" : "false",
                     (int)e.rssi, (unsigned)e.channel, (unsigned)now);
            logEventToSD("/deauth_flood.jsonl", String(lineBuf));
            if (meshEnabled && (sentinel_isRunning() || deauthDetectionEnabled.load()) && g_meshDeauth.load() && meshRateGate(String("DEAUTH_FLOOD_") + srcS, 30000)) {
                char meshBuf[80];
                snprintf(meshBuf, sizeof(meshBuf), "%s: DEAUTH_FLOOD:%s:%u:%d",
                         getNodeId().c_str(), srcBuf, (unsigned)r.count, (int)e.rssi);
                sendToSerial1(String(meshBuf), true);
            }
            ::detect_logIncident(String("DEAUTH_FLOOD:") + srcS + ":" + String(r.count), nullptr);
            quorum_addReport("DEAUTH_FLOOD", srcS, getNodeId(), e.rssi);
            attacker_kick(src, "DEAUTH_FLOOD");
        }
    }
    if (forgeFingerprint) {
        static PsramMap<uint64_t, uint32_t> g_forgeLastEmit;
        static constexpr size_t MAX_FORGE_EMIT_MAP = 64;
        uint64_t fk = packMac(src);
        auto fit = g_forgeLastEmit.find(fk);
        bool emitOk = (fit == g_forgeLastEmit.end()) || ((now - fit->second) > 10000);
        if (emitOk) {
            if (g_forgeLastEmit.size() >= MAX_FORGE_EMIT_MAP) evictOldestTs(g_forgeLastEmit);
            g_forgeLastEmit[fk] = now;
            char srcBuf[18];
            snprintf(srcBuf, sizeof(srcBuf), "%02X:%02X:%02X:%02X:%02X:%02X",
                     src[0],src[1],src[2],src[3],src[4],src[5]);
            String srcS(srcBuf);
            Serial.printf("[DETECT] DEAUTH_FORGE tool=%s src=%s (reason=%u seq=0x%04X dur=0x%04X%s)\n",
                          toolTag, srcBuf, (unsigned)reason, seqCtrl, durLE,
                          selfSrc ? " IMPERSONATION" : "");
            char lineBuf[260];
            snprintf(lineBuf, sizeof(lineBuf),
                     "{\"src\":\"%s\",\"tool\":\"%s\",\"class\":\"static\",\"reason\":%u,\"seq\":%u,\"dur\":%u,\"self_impersonation\":%s,\"rssi\":%d,\"ch\":%u,\"ts\":%u}",
                     srcBuf, toolTag, (unsigned)reason, (unsigned)seqCtrl, (unsigned)durLE,
                     selfSrc ? "true" : "false", (int)e.rssi, (unsigned)e.channel, (unsigned)now);
            logEventToSD("/deauth_flood.jsonl", String(lineBuf));
            ::detect_logIncident(String("DEAUTH_FORGE:") + srcS + ":" + toolTag, nullptr);
            quorum_addReport("DEAUTH_FORGE", srcS, getNodeId(), e.rssi);
            attacker_kick(src, "DEAUTH_FORGE");
            // Mesh forwarding is separate/additional.
            if (meshEnabled && (sentinel_isRunning() || deauthDetectionEnabled.load()) && g_meshDeauth.load() && meshRateGate(String("DEAUTH_FORGE_") + srcS, 30000)) {
                char meshBuf[96];
                snprintf(meshBuf, sizeof(meshBuf), "%s: DEAUTH_FORGE:%s:%s:%d",
                         getNodeId().c_str(), srcBuf, toolTag, (int)e.rssi);
                sendToSerial1(String(meshBuf), true);
            }
        }
    }
}

static void handleAssocReq(const DetectFrameEvent &e) {
    if (!g_assocSleepEnabled.load() && !g_pmkidEnabled.load()) return;
    if (e.len < 28) return;
    if ((e.payload[1] & 0x10) == 0) return;
    const uint8_t *src   = e.payload + 10;
    const uint8_t *bssid = e.payload + 16;
    uint64_t bssK = packMac(bssid);
    uint64_t srcK = packMac(src);
    uint32_t now = millis();
    std::lock_guard<std::recursive_mutex> lk(g_mtx);
    auto it = g_assocSleep.find(bssK);
    if (it == g_assocSleep.end() || (now - it->second.windowStartMs) > ASSOC_SLEEP_WIN_MS) {
        if (g_assocSleep.size() >= MAX_ASSOC_SLEEP_MAP) evictOldestBy(g_assocSleep, [](const auto &w) { return w.windowStartMs; });
        AssocSleepWindow w{};
        w.windowStartMs = now;
        w.bestRssi = e.rssi;
        w.channel = e.channel;
        w.alerted = false;
        w.frames = 1;
        w.distinctSrc.insert(srcK);
        g_assocSleep[bssK] = w;
        return;
    }
    AssocSleepWindow &w = it->second;
    w.distinctSrc.insert(srcK);
    if (w.frames < 65535) w.frames++;
    if (e.rssi > w.bestRssi) w.bestRssi = e.rssi;
    // Fire on PM-bit assoc-req RATE (1-MAC flood) OR distinct-src fan-out (multi-client).
    if (w.alerted || (w.frames < ASSOC_SLEEP_FRAMES && w.distinctSrc.size() < ASSOC_SLEEP_THRESH)) return;
    w.alerted = true;
    char bsBuf[18];
    snprintf(bsBuf, sizeof(bsBuf), "%02X:%02X:%02X:%02X:%02X:%02X",
             bssid[0],bssid[1],bssid[2],bssid[3],bssid[4],bssid[5]);
    String bs(bsBuf);
    char lineBuf[260];
    snprintf(lineBuf, sizeof(lineBuf),
             "{\"bssid\":\"%s\",\"distinct_src\":%u,\"win_ms\":%u,\"rssi\":%d,\"ch\":%u,\"reason\":\"FORGE_ASSOC_SLEEP\",\"ts\":%u}",
             bsBuf, (unsigned)w.distinctSrc.size(), (unsigned)ASSOC_SLEEP_WIN_MS,
             (int)w.bestRssi, (unsigned)w.channel, (unsigned)now);
    logEventToSD("/assoc_sleep.jsonl", String(lineBuf));
    if (meshEnabled && sentinel_isRunning() && g_meshAssocSleep.load() && meshRateGate(String("ASSOC_SLEEP_") + bs, 30000)) {
        char meshBuf[80];
        snprintf(meshBuf, sizeof(meshBuf), "%s: ASSOC_SLEEP:%s:%u:%d",
                 getNodeId().c_str(), bsBuf, (unsigned)w.distinctSrc.size(), (int)w.bestRssi);
        sendToSerial1(String(meshBuf), true);
    }
    Serial.printf("[DETECT] ASSOC_SLEEP bssid=%s distinct_src=%u frames=%u ch=%u rssi=%d\n",
                  bsBuf, (unsigned)w.distinctSrc.size(), (unsigned)w.frames,
                  (unsigned)w.channel, (int)w.bestRssi);
    ::detect_logIncident(String("ASSOC_SLEEP:") + bs + ":" + String((unsigned)w.distinctSrc.size()), nullptr);
    quorum_addReport("ASSOC_SLEEP", bs, getNodeId(), w.bestRssi);
}

// =============================================================================
// Probe-flood / tool probe attack fingerprint
// tool probe-attack template (esp32_tool/WiFiScan.cpp:7763-7823):
//   - Seq ctrl = 0x01 0x00 (raw byte 22=0x01, byte 23=0x00) FIXED, never increments
//   - Post-SSID IE: HT Capabilities (tag 0x2D, len 0x1A) — unusual in probe-req
//   - 165 frames per tick from rotating random src MACs
// tool probe-flood does not use this signature (lower rate, varies).
// Detection here: per-BSSID running rate of seq=0x0001 probe-reqs containing 0x2D.
// =============================================================================
struct ProbeFloodWindow {
    uint32_t windowStartMs;
    uint16_t hits;         // probe-req frames matching tool fingerprint
    int8_t   bestRssi;
    uint8_t  channel;
    bool     alerted;
    char     ssid[33];
};
static PsramMap<uint64_t, ProbeFloodWindow> g_probeFlood;  // key = packMac(srcMac & 0xFEFFFFFFFFFF) — collapse LAA
static constexpr size_t MAX_PROBE_FLOOD_MAP = 64;
static constexpr uint16_t PROBE_FLOOD_WIN_MS = 5000;
static constexpr uint16_t PROBE_FLOOD_THRESH = 10;
static std::atomic<bool> g_probeFloodEnabled{true};
static std::atomic<uint16_t> g_probeSingleMacThresh{60};   // 1 src >= N probes/5s
// Deauth Detector targeted-alert threshold: N unicast deauths to one dst / window. NVS "deauTgt".
std::atomic<uint16_t> g_deauthTargetedThresh{DEAUTH_TARGETED_THRESHOLD};
static std::atomic<uint16_t> g_probeRandTotalThresh{80};   // randomized flood total/5s
static std::atomic<uint16_t> g_probeRandDistinctThresh{60};// randomized flood distinct MAC/5s

// Behavioral fallback: distinct src MACs probing identical SSID in 5s window.
// Catches probe-flood variants that don't use the fixed seq=0x0001 fingerprint.
struct ProbeBehaveWindow {
    uint32_t windowStartMs{};
    PsramSet<uint64_t> distinctSrc;
    int8_t bestRssi{};
    uint8_t channel{};
    bool alerted{};
    char ssid[33]{};
};
static PsramMap<uint64_t, ProbeBehaveWindow> g_probeBehave;
static constexpr size_t MAX_PROBE_BEHAVE_MAP = 64;
static constexpr uint16_t PROBE_BEHAVE_WIN_MS = 5000;
// Threshold from academic IDS research: >40 distinct MACs probing same SSID in 5s
// is the suspicious-scanner-sweep range. Below that = busy-venue normal.
static constexpr uint8_t  PROBE_BEHAVE_THRESH = 40;

static void probeBehaveCheck(const uint8_t *src, const char *ssid, int8_t rssi,
                             uint8_t channel, uint32_t now) {
    if (!ssid || !ssid[0]) return;
    if (isSelfSsid(ssid)) return;
    uint64_t key = 0;
    for (int i = 0; i < 32 && ssid[i]; ++i) key = key * 131 + (uint8_t)ssid[i];
    std::lock_guard<std::recursive_mutex> lk(g_mtx);
    auto it = g_probeBehave.find(key);
    if (it == g_probeBehave.end() || (now - it->second.windowStartMs) > PROBE_BEHAVE_WIN_MS) {
        if (g_probeBehave.size() >= MAX_PROBE_BEHAVE_MAP) evictOldestBy(g_probeBehave, [](const auto &w) { return w.windowStartMs; });
        ProbeBehaveWindow w{};
        w.windowStartMs = now; w.bestRssi = rssi; w.channel = channel; w.alerted = false;
        strncpy(w.ssid, ssid, sizeof(w.ssid) - 1);
        w.distinctSrc.insert(packMac(src));
        g_probeBehave[key] = w;
        return;
    }
    ProbeBehaveWindow &w = it->second;
    w.distinctSrc.insert(packMac(src));
    if (rssi > w.bestRssi) w.bestRssi = rssi;
    if (w.alerted || w.distinctSrc.size() < PROBE_BEHAVE_THRESH) return;
    w.alerted = true;
    char lineBuf[260];
    snprintf(lineBuf, sizeof(lineBuf),
             "{\"ssid\":\"%s\",\"distinct_src\":%u,\"win_ms\":%u,\"rssi\":%d,\"ch\":%u,\"reason\":\"PROBE_FLOOD_BEHAVIORAL\",\"ts\":%u}",
             w.ssid, (unsigned)w.distinctSrc.size(), (unsigned)PROBE_BEHAVE_WIN_MS,
             (int)w.bestRssi, (unsigned)w.channel, (unsigned)now);
    logEventToSD("/probe_flood.jsonl", String(lineBuf));
    ::detect_logIncident(String("PROBE_FLOOD:") + w.ssid + ":" + String((unsigned)w.distinctSrc.size()), nullptr);
    ::detect_logIncident(String("PROBE_FLOOD_BEHAVE:") + w.ssid + ":src=" +
                         String((unsigned)w.distinctSrc.size()) + ":" + String((int)w.bestRssi), nullptr);
    char rateKeyBuf[40];
    snprintf(rateKeyBuf, sizeof(rateKeyBuf), "PROBE_BEHAVE_%08X", (uint32_t)key);
    if (meshEnabled && meshRateGate(String(rateKeyBuf), 30000)) {
        char meshBuf[120];
        snprintf(meshBuf, sizeof(meshBuf), "%s: PROBE_FLOOD_BEHAVE:%s:src=%u:%d",
                 getNodeId().c_str(), w.ssid, (unsigned)w.distinctSrc.size(), (int)w.bestRssi);
        sendToSerial1(String(meshBuf), true);
    }
    quorum_addReport("PROBE_FLOOD", String(w.ssid), getNodeId(), w.bestRssi);
}

// Global probe-rate flood: RANDOMIZED (mdk4 unique-MAC) or SINGLE_MAC (Marauder)
struct ProbeGlobalWin {
    uint32_t winMs{};
    uint16_t total{};
    bool alerted{};
    PsramMap<uint64_t,uint16_t> srcCount;
    PsramMap<uint64_t,uint8_t> srcStreak;
    uint32_t lastEmitMs{};
};
static ProbeGlobalWin g_probeGlobal;
static constexpr uint32_t PROBE_FLOOD_QUIET_MS = 60000;
static constexpr uint8_t  PROBE_SINGLE_MIN_STREAK = 2;
static constexpr size_t   MAX_PROBE_STREAK_MAP = 32;
static void probeGlobalCheck(const uint8_t *src, int8_t rssi, uint8_t channel, uint32_t now) {
    if (now - g_probeGlobal.winMs > 5000) {
        uint16_t thr = g_probeSingleMacThresh.load();
        for (auto it = g_probeGlobal.srcStreak.begin(); it != g_probeGlobal.srcStreak.end(); ) {
            auto c = g_probeGlobal.srcCount.find(it->first);
            if (c == g_probeGlobal.srcCount.end() || c->second < thr) it = g_probeGlobal.srcStreak.erase(it);
            else ++it;
        }
        for (const auto &kv : g_probeGlobal.srcCount) {
            if (kv.second < thr) continue;
            if (g_probeGlobal.srcStreak.size() >= MAX_PROBE_STREAK_MAP &&
                g_probeGlobal.srcStreak.find(kv.first) == g_probeGlobal.srcStreak.end()) continue;
            uint8_t &s = g_probeGlobal.srcStreak[kv.first];
            if (s < 255) s++;
        }
        g_probeGlobal.winMs = now; g_probeGlobal.total = 0; g_probeGlobal.alerted = false; g_probeGlobal.srcCount.clear();
    }
    if (g_probeGlobal.total < 65535) g_probeGlobal.total++;
    uint64_t sk = packMac(src);
    uint16_t &sc = g_probeGlobal.srcCount[sk];
    if (sc < 65535) sc++;
    if (g_probeGlobal.srcCount.size() > 512) evictOldestTs(g_probeGlobal.srcCount);
    if (g_probeGlobal.alerted) return;
    bool randomized = g_probeGlobal.total >= g_probeRandTotalThresh.load() && g_probeGlobal.srcCount.size() >= g_probeRandDistinctThresh.load();
    auto st = g_probeGlobal.srcStreak.find(sk);
    bool singleMac = sc >= g_probeSingleMacThresh.load() &&
                     st != g_probeGlobal.srcStreak.end() && st->second >= PROBE_SINGLE_MIN_STREAK;
    if (!randomized && !singleMac) return;
    g_probeGlobal.alerted = true;
    if (g_probeGlobal.lastEmitMs != 0 && (now - g_probeGlobal.lastEmitMs) < PROBE_FLOOD_QUIET_MS) return;
    g_probeGlobal.lastEmitMs = now;
    const char *kind = randomized ? "RANDOMIZED" : "SINGLE_MAC";
    String what = randomized
        ? String((unsigned)g_probeGlobal.total) + ":" + String((unsigned)g_probeGlobal.srcCount.size())
        : macStr(src) + ":" + String((unsigned)sc);
    Serial.printf("[DETECT] PROBE_FLOOD %s src=%s src_probes=%u total=%u distinct=%u in 5s ch=%u rssi=%d\n",
                  kind, macStr(src).c_str(), (unsigned)sc, (unsigned)g_probeGlobal.total,
                  (unsigned)g_probeGlobal.srcCount.size(), (unsigned)channel, (int)rssi);
    ::detect_logIncident(String("PROBE_FLOOD:") + kind + ":" + what, nullptr);
    quorum_addReport("PROBE_FLOOD", String(kind), getNodeId(), rssi);
    if (meshEnabled && meshRateGate(String("PROBE_FLOOD_") + kind, 30000)) {
        sendToSerial1(getNodeId() + ": PROBE_FLOOD:" + kind + ":" + what + ":" + String((int)rssi), true);
    }
}

static void handleProbeReq(const DetectFrameEvent &e) {
    if (!g_probeFloodEnabled.load()) return;
    if (e.len < 26) return;
    const uint8_t *p = e.payload;
    if (isSelfMac(p + 10)) return;
    const uint8_t *ieB = p + 24;
    uint16_t ieLenB = e.len - 24;
    char ssidB[33] = {0};
    if (ieLenB >= 2 && ieB[0] == 0) {
        uint8_t l = ieB[1];
        if (l <= 32 && (size_t)2 + l <= (size_t)ieLenB) {
            memcpy(ssidB, ieB + 2, l);
            ssidB[l] = 0;
        }
    }
    size_t ssidLenB = strlen(ssidB);
    bool ssidRandom = ssidLenB && ssidLooksRandom(ssidB, ssidLenB);
    bool ssidOk = ssidB[0] && ssidIsValid(ssidB, ssidLenB) && !ssidRandom;
    if (!ssidRandom) probeGlobalCheck(p + 10, e.rssi, e.channel, millis());
    if (ssidOk) probeBehaveCheck(p + 10, ssidB, e.rssi, e.channel, millis());

    // tool template: seq ctrl bytes 22-23 = 0x01 0x00 (= seqCtrl LE 0x0001).
    uint16_t seqCtrl = (uint16_t)p[22] | ((uint16_t)p[23] << 8);
    if (seqCtrl != 0x0001) return;

    // Single-frame emit: src MAC is re-randomized every frame (WiFiScan.cpp:5919), so
    // per-source cooldown is useless — gate globally.
    {
        static uint32_t s_probeForgeEmit = 0;
        uint32_t tnow = millis();
        if (s_probeForgeEmit == 0 || (tnow - s_probeForgeEmit) > 30000) {
            s_probeForgeEmit = tnow;
            char sb[18];
            snprintf(sb, sizeof(sb), "%02X:%02X:%02X:%02X:%02X:%02X",
                     p[10],p[11],p[12],p[13],p[14],p[15]);
            Serial.printf("[DETECT] PROBE_FLOOD MARAUDER src=%s ssid=%s seq=0x%04X ch=%u rssi=%d\n",
                          sb, ssidB, seqCtrl, (unsigned)e.channel, (int)e.rssi);
            char lb[220];
            snprintf(lb, sizeof(lb),
                     "{\"src\":\"%s\",\"ssid\":\"%s\",\"tool\":\"MARAUDER\",\"seq\":%u,\"reason\":\"PROBE_TEMPLATE\",\"rssi\":%d,\"ch\":%u,\"ts\":%u}",
                     sb, ssidB, (unsigned)seqCtrl, (int)e.rssi, (unsigned)e.channel, (unsigned)tnow);
            logEventToSD("/probe_flood.jsonl", String(lb));
            ::detect_logIncident(String("PROBE_FLOOD:MARAUDER:") + sb + ":" + ssidB, nullptr);
            quorum_addReport("PROBE_FLOOD", String("MARAUDER"), getNodeId(), e.rssi);
            attacker_kick(p + 10, "PROBE_FLOOD");
            if (meshEnabled && g_meshProbeFlood.load() && meshRateGate("PROBE_FLOOD_MARAUDER", 30000)) {
                sendToSerial1(getNodeId() + ": PROBE_FLOOD:MARAUDER:" + String(sb) +
                              ":" + String((int)e.rssi), true);
            }
        }
    }

    // Probe-request IE start = 24. seqCtrl=0x0001 alone is the Marauder fingerprint;
    // HT-IE is not always present (don't require it — verified vs current template).
    const uint8_t *ie = p + 24;
    uint16_t ieLen = e.len - 24;

    const uint8_t *src = p + 10;
    char ssid[33] = {0};
    if (ieLen >= 2 && ie[0] == 0) {
        uint8_t l = ie[1];
        if (l <= 32 && (size_t)2 + l <= (size_t)ieLen) {
            memcpy(ssid, ie + 2, l);
            ssid[l] = 0;
        }
    }
    if (isSelfSsid(ssid)) return;

    uint64_t key = 0;
    for (int i = 0; i < 32 && ssid[i]; ++i) key = key * 131 + (uint8_t)ssid[i];
    if (key == 0) key = 0xDEADBEEFUL;  // anonymous bucket for empty SSID

    uint32_t now = millis();
    std::lock_guard<std::recursive_mutex> lk(g_mtx);
    auto it = g_probeFlood.find(key);
    if (it == g_probeFlood.end() || (now - it->second.windowStartMs) > PROBE_FLOOD_WIN_MS) {
        if (g_probeFlood.size() >= MAX_PROBE_FLOOD_MAP) evictOldestBy(g_probeFlood, [](const auto &w) { return w.windowStartMs; });
        ProbeFloodWindow w{};
        w.windowStartMs = now;
        w.hits = 1;
        w.bestRssi = e.rssi;
        w.channel = e.channel;
        w.alerted = false;
        strncpy(w.ssid, ssid, sizeof(w.ssid) - 1);
        g_probeFlood[key] = w;
        return;
    }
    ProbeFloodWindow &w = it->second;
    if (w.hits < 65535) w.hits++;
    if (e.rssi > w.bestRssi) w.bestRssi = e.rssi;
    if (w.alerted || w.hits < PROBE_FLOOD_THRESH) return;
    w.alerted = true;
    String msg = String("{\"ssid\":\"") + w.ssid +
                 "\",\"hits\":" + String(w.hits) +
                 ",\"win_ms\":" + String(PROBE_FLOOD_WIN_MS) +
                 ",\"src_sample\":\"" + macStr(src) +
                 "\",\"rssi\":" + String(w.bestRssi) +
                 ",\"ch\":" + String(w.channel) +
                 ",\"reason\":\"FORGE_PROBE_FLOOD\"" +
                 ",\"ts\":" + String(now) + "}";
    logEventToSD("/probe_flood.jsonl", msg);
    ::detect_logIncident(String("PROBE_FLOOD:") + w.ssid + ":" + String(w.hits), nullptr);
    if (meshEnabled && sentinel_isRunning() && g_meshProbeFlood.load() && meshRateGate("PROBE_FLOOD_" + String((uint32_t)key, HEX), 30000)) {
        sendToSerial1(getNodeId() + ": PROBE_FLOOD:" + w.ssid + ":" + String(w.hits) + ":" + String(w.bestRssi), true);
    }
    quorum_addReport("PROBE_FLOOD", String(w.ssid), getNodeId(), w.bestRssi);
}

// =============================================================================
// SSID Confusion (CVE-2023-52424)
// =============================================================================
static void handleProbeResp(const DetectFrameEvent &e) {
    if (!g_ssidConfusionEnabled.load() && !g_karmaEnabled.load()) return;
    if (e.len < 36) return;
    const uint8_t *p = e.payload;
    const uint8_t *bssid = p + 16;
    const uint8_t *ie = p + 36;
    uint16_t ieLen = e.len - 36;
    char ssid[33] = {0};
    if (!extractSSID(ie, ieLen, ssid, sizeof(ssid))) return;
    if (ssid[0] == 0) return;
    if (!ssidIsValid(ssid, strlen(ssid))) return;

    if (g_karmaEnabled.load()) {
        karma_observeProbeResp(bssid, ssid, e.rssi);
        karma_checkBaitMatch(ssid, bssid, e.rssi);
    }
    if (!g_ssidConfusionEnabled.load()) return;

    uint64_t k = packMac(bssid);
    uint32_t now = millis();

    std::lock_guard<std::recursive_mutex> lk(g_mtx);
    auto it = g_apBaseline.find(k);
    if (it == g_apBaseline.end()) {
        if (::g_detectVerbose.load())
            Serial.printf("[VERIFY-SCN] no baseline for %s resp_ssid=%s\n", macStr(bssid).c_str(), ssid);
        return;
    }
    ApBaseline &b = it->second;
    if (b.ssid[0] == 0) {
        if (::g_detectVerbose.load())
            Serial.printf("[VERIFY-SCN] baseline has empty ssid for %s\n", macStr(bssid).c_str());
        return;
    }
    if (::g_detectVerbose.load())
        Serial.printf("[VERIFY-SCN] %s beacon_ssid=%s resp_ssid=%s match=%d\n",
                      macStr(bssid).c_str(), b.ssid, ssid, strcmp(b.ssid, ssid) == 0);
    if (strcmp(b.ssid, ssid) == 0) {
        strncpy(b.respSsid, ssid, sizeof(b.respSsid) - 1);
        return;
    }
    // Mismatch: probe-response SSID differs from beacon SSID for same BSSID
    SsidConfusionEvent ev{};
    memcpy(ev.bssid, bssid, 6);
    strncpy(ev.beaconSsid, b.ssid, sizeof(ev.beaconSsid) - 1);
    strncpy(ev.respSsid, ssid, sizeof(ev.respSsid) - 1);
    ev.rssi = e.rssi;
    ev.channel = e.channel;
    ev.ts = now;
    g_ssidConfusionLog.push_back(ev);
    if (g_ssidConfusionLog.size() > MAX_SC_LOG) g_ssidConfusionLog.erase(g_ssidConfusionLog.begin());

    char bsBuf[18];
    snprintf(bsBuf, sizeof(bsBuf), "%02X:%02X:%02X:%02X:%02X:%02X",
             bssid[0],bssid[1],bssid[2],bssid[3],bssid[4],bssid[5]);
    String bs(bsBuf);
    char lineBuf[280];
    snprintf(lineBuf, sizeof(lineBuf),
             "{\"bssid\":\"%s\",\"beacon_ssid\":\"%s\",\"resp_ssid\":\"%s\",\"rssi\":%d,\"ch\":%u,\"ts\":%u}",
             bsBuf, ssidIsValid(b.ssid, strlen(b.ssid)) ? b.ssid : "",
             ssidIsValid(ssid, strlen(ssid)) ? ssid : "", (int)e.rssi, (unsigned)e.channel, (unsigned)now);
    logEventToSD("/ssid_confusion.jsonl", String(lineBuf));
    Serial.printf("[DETECT] SSID_CONFUSION src=%s beacon_ssid=%s resp_ssid=%s rssi=%d ch=%u\n",
                  bsBuf, b.ssid, ssid, (int)e.rssi, (unsigned)e.channel);
    ::detect_logIncident(String("SSID_CONFUSION:") + bsBuf + ":" + String((int)e.rssi), nullptr);
    if (meshEnabled) {
        if (g_meshSsidConf.load() && meshRateGate(String("SSIDCONF_") + bs, 30000)) {
            char meshBuf[80];
            snprintf(meshBuf, sizeof(meshBuf), "%s: SSID_CONFUSION:%s:%d",
                     getNodeId().c_str(), bsBuf, (int)e.rssi);
            sendToSerial1(String(meshBuf), true);
        }
    }
    quorum_addReport("SSIDCONF", bs, getNodeId(), e.rssi);
    strncpy(b.respSsid, ssid, sizeof(b.respSsid) - 1);
}

// =============================================================================
// SAE / Dragonblood DoS
// =============================================================================
static void handleAuthSae(const DetectFrameEvent &e) {
    // 802.11 auth: fixed body at +24 = algo(2) seq(2) status(2)
    if (e.len < 30) return;
    const uint8_t *p = e.payload;
    uint16_t algo = (uint16_t)p[24] | ((uint16_t)p[25] << 8);
    if (::g_detectVerbose.load()) {
        uint16_t vseq = (uint16_t)p[26] | ((uint16_t)p[27] << 8);
        Serial.printf("[VERIFY-AUTH] algo=%u seq=%u ch=%u rssi=%d saeOn=%d\n",
                      algo, vseq, (unsigned)e.channel, (int)e.rssi, (int)g_saeEnabled.load());
    }

    if (algo == 0) {
        const uint8_t *src   = p + 10;
        const uint8_t *bss   = p + 16;
        if (isSelfMac(src)) return;
        uint64_t bk = packMac(bss);
        uint64_t sk = packMac(src);
        uint32_t tnow = millis();
        std::lock_guard<std::recursive_mutex> lk(g_mtx);
        auto ai = g_authFlood.find(bk);
        if (ai == g_authFlood.end() || (tnow - ai->second.windowStartMs) > AUTH_FLOOD_WIN_MS) {
            if (g_authFlood.size() >= MAX_AUTH_FLOOD_MAP) {
                uint32_t oldest = UINT32_MAX; uint64_t oldestK = 0;
                for (const auto &kv : g_authFlood) if (kv.second.windowStartMs < oldest) { oldest = kv.second.windowStartMs; oldestK = kv.first; }
                g_authFlood.erase(oldestK);
            }
            AuthFloodWindow w{};
            w.windowStartMs = tnow; w.frames = 1; w.bestRssi = e.rssi;
            w.channel = e.channel; w.alerted = false; w.distinctSrc.insert(sk);
            g_authFlood[bk] = w;
            return;
        }
        AuthFloodWindow &w = ai->second;
        if (w.frames < 65535) w.frames++;
        w.distinctSrc.insert(sk);
        if (e.rssi > w.bestRssi) w.bestRssi = e.rssi;
        if (!w.alerted && w.distinctSrc.size() >= AUTH_FLOOD_DISTINCT_SRC &&
            w.frames >= AUTH_FLOOD_FRAMES) {
            w.alerted = true;
            char bsBuf[18];
            snprintf(bsBuf, sizeof(bsBuf), "%02X:%02X:%02X:%02X:%02X:%02X",
                     bss[0],bss[1],bss[2],bss[3],bss[4],bss[5]);
            String bs(bsBuf);
            Serial.printf("[DETECT] AUTH_FLOOD bssid=%s distinct_src=%u frames=%u in %ums\n",
                          bsBuf, (unsigned)w.distinctSrc.size(), (unsigned)w.frames,
                          (unsigned)(tnow - w.windowStartMs));
            ::detect_logIncident(String("AUTH_FLOOD:") + bs + ":" + String((unsigned)w.distinctSrc.size()) + ":" + String((int)w.bestRssi), nullptr);
            char lb[260];
            snprintf(lb, sizeof(lb),
                     "{\"bssid\":\"%s\",\"distinct_src\":%u,\"frames\":%u,\"win_ms\":%u,\"rssi\":%d,\"ch\":%u,\"reason\":\"AUTH_DOS\",\"ts\":%u}",
                     bsBuf, (unsigned)w.distinctSrc.size(), (unsigned)w.frames,
                     (unsigned)AUTH_FLOOD_WIN_MS, (int)w.bestRssi, (unsigned)w.channel, (unsigned)tnow);
            logEventToSD("/sae_dos.jsonl", String(lb));
            if (meshEnabled && sentinel_isRunning() && g_meshAuth.load() && meshRateGate(String("AUTH_FLOOD_") + bs, 30000)) {
                char mb[80];
                snprintf(mb, sizeof(mb), "%s: AUTH_FLOOD:%s:%u:%d",
                         getNodeId().c_str(), bsBuf, (unsigned)w.distinctSrc.size(), (int)w.bestRssi);
                sendToSerial1(String(mb), true);
            }
            quorum_addReport("AUTH_FLOOD", bs, getNodeId(), w.bestRssi);
            attacker_kick(bss, "AUTH_FLOOD");
        }
        return;
    }

    if (!g_saeEnabled.load()) return;
    if (algo != 3) return;
    uint16_t seq = (uint16_t)p[26] | ((uint16_t)p[27] << 8);
    const uint8_t *bssid = p + 16;
    if (bssid[0] & 0x02) return;
    uint64_t k = packMac(bssid);
    uint32_t now = millis();
    uint16_t win = g_saeWindow.load();

    std::lock_guard<std::recursive_mutex> lk(g_mtx);
    if (g_saeCounters.size() >= 512 && g_saeCounters.find(k) == g_saeCounters.end()) {
        for (auto it = g_saeCounters.begin(); it != g_saeCounters.end(); ) {
            if (now - it->second.windowStart > win) it = g_saeCounters.erase(it);
            else ++it;
        }
    }
    SaeCounter &c = g_saeCounters[k];
    if (c.windowStart == 0 || now - c.windowStart > win) {
        c.windowStart = now;
        c.commits = 0;
        c.confirms = 0;
        c.alerted = false;
    }
    if (seq == 1) c.commits++;
    else if (seq == 2) c.confirms++;
    uint16_t unmatched = (c.commits > c.confirms) ? (c.commits - c.confirms) : 0;
    if (!c.alerted && unmatched >= g_saeUnmatchedThresh.load()) {
        c.alerted = true;
        SaeDosEvent ev{};
        memcpy(ev.bssid, bssid, 6);
        ev.unmatchedCommits = unmatched;
        ev.rssi = e.rssi;
        ev.channel = e.channel;
        ev.windowStart = c.windowStart;
        ev.ts = now;
        g_saeDosLog.push_back(ev);
        if (g_saeDosLog.size() > MAX_SAE_LOG) g_saeDosLog.erase(g_saeDosLog.begin());

        char bsBuf[18];
        snprintf(bsBuf, sizeof(bsBuf), "%02X:%02X:%02X:%02X:%02X:%02X",
                 bssid[0],bssid[1],bssid[2],bssid[3],bssid[4],bssid[5]);
        String bs(bsBuf);
        char lineBuf[260];
        snprintf(lineBuf, sizeof(lineBuf),
                 "{\"bssid\":\"%s\",\"unmatched_commits\":%u,\"rssi\":%d,\"ch\":%u,\"window_start\":%u,\"ts\":%u}",
                 bsBuf, (unsigned)unmatched, (int)e.rssi, (unsigned)e.channel,
                 (unsigned)c.windowStart, (unsigned)now);
        logEventToSD("/sae_dos.jsonl", String(lineBuf));
        Serial.printf("[DETECT] SAE_DOS bssid=%s unmatched=%u commits=%u confirms=%u ch=%u rssi=%d\n",
                      bsBuf, (unsigned)unmatched, (unsigned)c.commits, (unsigned)c.confirms,
                      (unsigned)e.channel, (int)e.rssi);
        ::detect_logIncident(String("SAE_DOS:") + bs + ":" + String((unsigned)unmatched), nullptr);
        if (meshEnabled && sentinel_isRunning() && g_meshSae.load() && meshRateGate(String("SAE_DOS_") + bs, 10000)) {
            char meshBuf[80];
            snprintf(meshBuf, sizeof(meshBuf), "%s: SAE_DOS:%s:%u",
                     getNodeId().c_str(), bsBuf, (unsigned)unmatched);
            sendToSerial1(String(meshBuf), true);
        }
        quorum_addReport("SAE_DOS", bs, getNodeId(), e.rssi);
        attacker_kick(bssid, "SAE_DOS");
    }
}
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
