lukeswitz/AntiHunter/Antihunter/full/src/triangulation.cpp

#include "triangulation.h"
#include "scanner.h"
#include "hardware.h"
#include "detect.h"
#include <math.h>
#include <atomic>
#include <algorithm>
#include <iterator>
#include <numeric>
#include <NimBLEDevice.h>
#include <NimBLEScan.h>
#include <NimBLEAdvertisedDevice.h>

extern NimBLEScan *pBLEScan;
#include <TinyGPSPlus.h>
#include <esp_timer.h>

extern String macFmt6(const uint8_t *m);
extern bool parseMac6(const String &in, uint8_t out[6]);
extern std::atomic<bool> stopRequested;
extern ScanMode currentScanMode;
extern TinyGPSPlus gps;
extern float gpsLat, gpsLon;
extern std::atomic<bool> gpsValid;
extern TriangulationAccumulator triAccum;
extern bool triangulationOrchestratorAssigned;

// Triang
static TaskHandle_t calibrationTaskHandle = nullptr;
static TaskHandle_t coordinatorSetupTaskHandle = nullptr;
static std::atomic<bool> triSetupAbort{false};
ClockDiscipline clockDiscipline = {0.0, 0, 0, false, 0, false};
const size_t MAX_TRIANGULATION_NODES = 15;
const size_t MAX_SYNC_STATUS = 15;
const size_t MAX_ACK_INFO = 20;

std::map<String, uint32_t> nodePropagationDelays;
std::vector<NodeSyncStatus> nodeSyncStatus;
std::vector<TriangulationNode> triangulationNodes;
std::mutex triangulationMutex;
APFinalResult apFinalResult = {false, 0.0, 0.0, 0.0, 0.0, 0, ""};
String calculateTriangulation();
static std::atomic<uint64_t> g_triTarget{0};

static inline uint64_t triPack(const uint8_t *m) {
    uint64_t v = 0;
    for (int i = 0; i < 6; i++) v |= (uint64_t)m[i] << (8 * i);
    return v;
}

void triangulationSetTarget(const uint8_t *mac) {
    g_triTarget.store(mac ? triPack(mac) : 0ULL, std::memory_order_relaxed);
}

void triangulationGetTarget(uint8_t *out) {
    const uint64_t v = g_triTarget.load(std::memory_order_relaxed);
    for (int i = 0; i < 6; i++) out[i] = (uint8_t)((v >> (8 * i)) & 0xFF);
}

bool triangulationTargetMatches(const uint8_t *mac) {
    return g_triTarget.load(std::memory_order_relaxed) == triPack(mac);
}

bool triangulationTargetIsSet() {
    return g_triTarget.load(std::memory_order_relaxed) != 0ULL;
}

String triangulationTargetStr() {
    uint8_t cur[6];
    triangulationGetTarget(cur);
    return macFmt6(cur);
}

uint32_t triangulationStart = 0;
uint32_t triangulationDuration = 0;
std::atomic<bool> triangulationActive(false);
bool triangulationInitiator = false;
char triangulationTargetIdentity[10] = {0};
DynamicReportingSchedule reportingSchedule;
static size_t triLastChildCount = 0;
std::vector<TriangulateAckInfo> triangulateAcks;
std::vector<String> triangulateReportedNodes;
String triangulationCoordinator = "";
uint32_t ackCollectionStart = 0;
uint32_t stopSentTimestamp = 0;
bool waitingForFinalReports = false;
const uint32_t FINAL_REPORT_TIMEOUT_MS = 15000;
static volatile bool triStopCameFromMesh = false;
static std::atomic<bool> triOperatorStop(false);
static uint32_t lastTriangulationStopTime = 0;
const uint32_t TRIANGULATION_DEBOUNCE_MS = 20000;


RFEnvironment currentRFEnvironment = RF_ENV_INDOOR;

// Path loss defaults calibrated for 6 dBi RX antenna, indoor
PathLossCalibration pathLoss = {
    -28.0,   // rssi0_wifi (dBm @ 1m, measured avg: -28.3)
    -47.0,   // rssi0_ble (dBm @ 1m, measured avg: -47.2)
    3.2,     // n_wifi (path loss exponent)
    3.0,     // n_ble (path loss exponent, research shows 2.0-4.0 indoors)
    false    // calibrated flag
};

DistanceTuning distanceTuning = {
    1.0f,
    1.0f,
    false
};

void setRFEnvironment(RFEnvironment env) {
    if (env > RF_ENV_INDUSTRIAL) env = RF_ENV_INDOOR;
    currentRFEnvironment = env;
    const RFEnvironmentPreset& preset = RF_PRESETS[env];
    pathLoss.n_wifi = preset.n_wifi;
    pathLoss.n_ble = preset.n_ble;
    pathLoss.rssi0_wifi = preset.rssi0_wifi;
    pathLoss.rssi0_ble = preset.rssi0_ble;
    adaptivePathLoss.n_wifi = preset.n_wifi;
    adaptivePathLoss.n_ble = preset.n_ble;
    adaptivePathLoss.rssi0_wifi = preset.rssi0_wifi;
    adaptivePathLoss.rssi0_ble = preset.rssi0_ble;
    Serial.printf("[TRIANGULATE] RF environment set to %d (n_wifi=%.1f, n_ble=%.1f)\n",
                  env, preset.n_wifi, preset.n_ble);
}

// Helpers

float estimateRangeM(int8_t rssi, bool isWiFi) {
    if (rssi <= RSSI_SENSITIVITY_FLOOR || rssi >= 0) return -1.0f;
    float rssi0 = isWiFi ? adaptivePathLoss.rssi0_wifi : adaptivePathLoss.rssi0_ble;
    float n = isWiFi ? adaptivePathLoss.n_wifi : adaptivePathLoss.n_ble;
    float d = pow(10.0f, (rssi0 - (float)rssi) / (10.0f * n));
    if (distanceTuning.enabled) {
        d *= isWiFi ? distanceTuning.wifi_multiplier : distanceTuning.ble_multiplier;
    }
    return (d < 0.1f) ? 0.1f : d;
}

float estimateRangeSigmaM(int8_t rssi, bool isWiFi) {
    float d = estimateRangeM(rssi, isWiFi);
    if (d < 0.0f) return -1.0f;
    float n = isWiFi ? adaptivePathLoss.n_wifi : adaptivePathLoss.n_ble;
    float sigmaDb = RF_PRESETS[currentRFEnvironment].sigma_db;
    if (!isWiFi) sigmaDb = sqrtf(sigmaDb * sigmaDb + BLE_TXPOWER_SIGMA_DB * BLE_TXPOWER_SIGMA_DB);
    if (!pathLoss.calibrated) sigmaDb = sqrtf(sigmaDb * sigmaDb + PATHLOSS_UNCALIBRATED_SIGMA_DB * PATHLOSS_UNCALIBRATED_SIGMA_DB);
    return d * (logf(10.0f) / (10.0f * n)) * sigmaDb;
}

bool rssiUsable(int8_t rssi) {
    return rssi > RSSI_SENSITIVITY_FLOOR && rssi < 0;
}

float rssiToDistance(const TriangulationNode &node, bool isWiFi) {
    float rssi0 = isWiFi ? adaptivePathLoss.rssi0_wifi : adaptivePathLoss.rssi0_ble;
    float n = isWiFi ? adaptivePathLoss.n_wifi : adaptivePathLoss.n_ble;

    float distance = pow(10.0f, (rssi0 - node.filteredRssi) / (10.0f * n));

    if (distanceTuning.enabled) {
        float multiplier = isWiFi ? distanceTuning.wifi_multiplier : distanceTuning.ble_multiplier;
        distance *= multiplier;
    }

    if (distance < 0.1f) distance = 0.1f;
    return distance;
}

void nodeUpdateDistance(TriangulationNode &node) {
    bool primaryIsWiFi = !node.isBLE;
    float d1 = rssiToDistance(node, primaryIsWiFi);
    float s1 = rssiDistanceSigma(node, d1, primaryIsWiFi);

    if (!node.hasBLE || node.bleRssi >= 0 || !rssiUsable(node.bleRssi)) {
        node.distanceEstimate = d1;
        node.distanceSigma = s1;
        return;
    }

    TriangulationNode bleView = node;
    bleView.filteredRssi = (float)node.bleRssi;
    bleView.rssiHistory.clear();
    float d2 = rssiToDistance(bleView, false);
    float s2 = rssiDistanceSigma(bleView, d2, false);

    float w1 = 1.0f / (s1 * s1);
    float w2 = 1.0f / (s2 * s2);
    node.distanceEstimate = (d1 * w1 + d2 * w2) / (w1 + w2);
    node.distanceSigma = sqrtf(1.0f / (w1 + w2));
}

float rssiDistanceSigma(const TriangulationNode &node, float distance, bool isWiFi) {
    float n = isWiFi ? adaptivePathLoss.n_wifi : adaptivePathLoss.n_ble;
    float shadowDb = RF_PRESETS[currentRFEnvironment].sigma_db;

    if (node.rssiHistory.size() >= 3) {
        float mean = std::accumulate(node.rssiHistory.begin(), node.rssiHistory.end(), 0.0f);
        mean /= node.rssiHistory.size();
        float variance = 0.0f;
        for (int8_t r : node.rssiHistory) {
            float d = (float)r - mean;
            variance += d * d;
        }
        variance /= node.rssiHistory.size();
        shadowDb = max(shadowDb, sqrtf(variance));
    }

    float sigmaDb = shadowDb;
    if (!isWiFi) {
        sigmaDb = sqrtf(shadowDb * shadowDb + BLE_TXPOWER_SIGMA_DB * BLE_TXPOWER_SIGMA_DB);
    }
    if (!pathLoss.calibrated) {
        sigmaDb = sqrtf(sigmaDb * sigmaDb + PATHLOSS_UNCALIBRATED_SIGMA_DB * PATHLOSS_UNCALIBRATED_SIGMA_DB);
    }

    float sigma = distance * (logf(10.0f) / (10.0f * n)) * sigmaDb;
    return max(0.5f, sigma);
}

float getAverageHDOP(const std::vector<TriangulationNode> &nodes) {
    if (nodes.empty()) return 99.9;
    
    float totalHDOP = 0.0;
    int validCount = 0;
    
    for (const auto& node : nodes) {
        if (node.hasGPS && node.hdop > 0.0 && node.hdop < 50.0) {
            totalHDOP += node.hdop;
            validCount++;
        }
    }
    
    if (validCount == 0) return 99.9;
    return totalHDOP / validCount;
}

float calculateGDOP(const std::vector<TriangulationNode> &nodes, double estLat, double estLon) {
    if (nodes.size() < 3) return 999.9f;

    double a = 0.0, b = 0.0, c = 0.0;
    int used = 0;

    for (const auto &node : nodes) {
        if (!node.hasGPS) continue;
        double east, north;
        geodeticToENU(node.lat, node.lon, estLat, estLon, east, north);
        double r = sqrt(east * east + north * north);
        if (r < 0.5) continue;
        double ux = east / r;
        double uy = north / r;
        a += ux * ux;
        b += ux * uy;
        c += uy * uy;
        used++;
    }

    if (used < 3) return 999.9f;

    double det = a * c - b * b;
    if (fabs(det) < 1e-9) return 999.9f;

    double trace = (a + c) / det;
    if (trace <= 0.0) return 999.9f;

    float gdop = (float)sqrt(trace);
    if (gdop > 999.9f) gdop = 999.9f;
    return gdop;
}

void initNodeKalmanFilter(TriangulationNode &node) {
    node.kalmanFilter.estimate = (float)node.rssi;
    node.kalmanFilter.errorCovariance = 10.0;
    node.kalmanFilter.processNoise = 0.5;
    node.kalmanFilter.measurementNoise = 4.0;
    node.kalmanFilter.initialized = true;
    node.filteredRssi = (float)node.rssi;
}

float kalmanFilterRSSI(TriangulationNode &node, int8_t measurement) {
    if (!node.kalmanFilter.initialized) {
        initNodeKalmanFilter(node);
        return (float)measurement;
    }
    
    if (node.rssiHistory.size() > 5) {
        float variance = 0.0;
        float mean = std::accumulate(node.rssiHistory.begin(), node.rssiHistory.end(), 0.0f);
        mean /= node.rssiHistory.size();

        for (int8_t rssi : node.rssiHistory) {
            float diff = rssi - mean;
            variance += diff * diff;
        }
        variance /= node.rssiHistory.size();
        
        node.kalmanFilter.measurementNoise = max(2.0f, variance);
    }
    
    float prediction = node.kalmanFilter.estimate;
    float predictionCovariance = node.kalmanFilter.errorCovariance + node.kalmanFilter.processNoise;
    float kalmanGain = predictionCovariance / (predictionCovariance + node.kalmanFilter.measurementNoise);
    float estimate = prediction + kalmanGain * ((float)measurement - prediction);
    float errorCovariance = (1.0 - kalmanGain) * predictionCovariance;
    
    node.kalmanFilter.estimate = estimate;
    node.kalmanFilter.errorCovariance = errorCovariance;
    
    return estimate;
}

float calculateSignalQuality(const TriangulationNode &node) {
    if (node.rssiHistory.size() < 3) {
        // Even with few samples, factor in hit count for initial quality estimate
        float hitFactor = min(1.0f, (float)node.hitCount / 15.0f);
        return 0.3f + (hitFactor * 0.2f);  // Range 0.3-0.5 based on hits
    }

    float variance = 0.0;
    float mean = std::accumulate(node.rssiHistory.begin(), node.rssiHistory.end(), 0.0f);
    mean /= node.rssiHistory.size();

    for (int8_t rssi : node.rssiHistory) {
        float diff = rssi - mean;
        variance += diff * diff;
    }
    variance /= node.rssiHistory.size();

    float stability = 1.0 / (1.0 + sqrt(variance));
    float strength = (node.filteredRssi + 100.0) / 100.0;
    strength = constrain(strength, 0.0, 1.0);

    // Hit count factor: more detections = higher confidence in this node's data
    // Saturates at ~15 hits (typical good detection count during scan)
    float hitFactor = min(1.0f, (float)node.hitCount / 15.0f);

    // Weight: 40% stability, 30% signal strength, 30% hit count
    // Node with strongest signal AND most hits gets highest weight
    return (stability * 0.4f + strength * 0.3f + hitFactor * 0.3f);
}

bool performWeightedTrilateration(const std::vector<TriangulationNode> &nodes,
                                   float &estLat, float &estLon, float &confidence,
                                   float &uncertaintyM) {
    struct Obs { double e, n, d, w; };
    std::vector<Obs> obs;
    obs.reserve(nodes.size());

    double refLat = 0.0, refLon = 0.0;
    int gpsCount = 0;
    for (const auto &node : nodes) {
        if (!node.hasGPS) continue;
        refLat += node.lat;
        refLon += node.lon;
        gpsCount++;
    }
    if (gpsCount < 3) return false;
    refLat /= gpsCount;
    refLon /= gpsCount;

    for (const auto &node : nodes) {
        if (!node.hasGPS) continue;
        if (node.distanceEstimate <= 0.0f) continue;
        double sigma = (node.distanceSigma > 0.0f) ? node.distanceSigma : 1.0;
        Obs o;
        geodeticToENU(node.lat, node.lon, refLat, refLon, o.e, o.n);
        o.d = node.distanceEstimate;
        o.w = 1.0 / (sigma * sigma);
        obs.push_back(o);
    }

    if (obs.size() < 3) return false;

    double x = 0.0, y = 0.0, wsum = 0.0;
    for (const auto &o : obs) {
        x += o.e * o.w;
        y += o.n * o.w;
        wsum += o.w;
    }
    if (wsum <= 0.0) return false;
    x /= wsum;
    y /= wsum;

    auto costAt = [&obs](double px, double py) {
        double c = 0.0;
        for (const auto &o : obs) {
            double dx = px - o.e;
            double dy = py - o.n;
            double r = sqrt(dx * dx + dy * dy);
            if (r < 1e-6) r = 1e-6;
            double residual = r - o.d;
            c += o.w * residual * residual;
        }
        return c;
    };

    double lambda = 1e-3;
    double cost = costAt(x, y);

    for (int iter = 0; iter < TRILATERATION_MAX_ITER; iter++) {
        double jtwj00 = 0.0, jtwj01 = 0.0, jtwj11 = 0.0;
        double jtwr0 = 0.0, jtwr1 = 0.0;

        for (const auto &o : obs) {
            double dx = x - o.e;
            double dy = y - o.n;
            double r = sqrt(dx * dx + dy * dy);
            if (r < 1e-6) r = 1e-6;
            double residual = r - o.d;
            double gx = dx / r;
            double gy = dy / r;

            jtwj00 += o.w * gx * gx;
            jtwj01 += o.w * gx * gy;
            jtwj11 += o.w * gy * gy;
            jtwr0 += o.w * gx * residual;
            jtwr1 += o.w * gy * residual;
        }

        bool stepped = false;
        double stepX = 0.0, stepY = 0.0;

        for (int attempt = 0; attempt < 12; attempt++) {
            double a = jtwj00 * (1.0 + lambda);
            double b = jtwj01;
            double c = jtwj11 * (1.0 + lambda);
            double det = a * c - b * b;
            if (fabs(det) < 1e-12) {
                lambda *= 10.0;
                if (lambda > 1e12) break;
                continue;
            }

            stepX = -(c * jtwr0 - b * jtwr1) / det;
            stepY = -(a * jtwr1 - b * jtwr0) / det;

            double trial = costAt(x + stepX, y + stepY);
            if (trial <= cost) {
                x += stepX;
                y += stepY;
                cost = trial;
                lambda = max(1e-7, lambda * 0.3);
                stepped = true;
                break;
            }
            lambda *= 10.0;
            if (lambda > 1e12) break;
        }

        if (!stepped) break;
        if (sqrt(stepX * stepX + stepY * stepY) < TRILATERATION_STEP_TOL_M) break;
    }

    if (!isfinite(x) || !isfinite(y)) return false;

    double jtwj00 = 0.0, jtwj01 = 0.0, jtwj11 = 0.0;
    double chi2 = 0.0;
    for (const auto &o : obs) {
        double dx = x - o.e;
        double dy = y - o.n;
        double r = sqrt(dx * dx + dy * dy);
        if (r < 1e-6) r = 1e-6;
        double residual = r - o.d;
        double gx = dx / r;
        double gy = dy / r;
        jtwj00 += o.w * gx * gx;
        jtwj01 += o.w * gx * gy;
        jtwj11 += o.w * gy * gy;
        chi2 += o.w * residual * residual;
    }

    double det = jtwj00 * jtwj11 - jtwj01 * jtwj01;
    if (fabs(det) < 1e-12) return false;

    int dof = (int)obs.size() - 2;
    double scale = (dof > 0) ? max(1.0, chi2 / dof) : 1.0;

    double c00 = scale * jtwj11 / det;
    double c11 = scale * jtwj00 / det;
    double c01 = -scale * jtwj01 / det;

    double tr = c00 + c11;
    double diff = sqrt(max(0.0, (c00 - c11) * (c00 - c11) / 4.0 + c01 * c01));
    double eigMax = tr / 2.0 + diff;
    uncertaintyM = (float)sqrt(max(0.0, eigMax));

    double outLat, outLon;
    enuToGeodetic(x, y, refLat, refLon, outLat, outLon);
    estLat = (float)outLat;
    estLon = (float)outLon;

    float rmsResidual = (dof > 0) ? (float)sqrt(chi2 / obs.size()) : 0.0f;
    float fitTerm = 1.0f / (1.0f + rmsResidual);
    float geomTerm = 1.0f / (1.0f + uncertaintyM / 10.0f);
    float countTerm = 1.0f - 1.0f / (float)obs.size();

    confidence = constrain(fitTerm * geomTerm * (0.5f + 0.5f * countTerm), 0.0f, 1.0f);
    return true;
}

void broadcastTimeSyncRequest() {
    if (!rtcAvailable) return;
    if (rtcMutex == NULL) return;
    
    if (xSemaphoreTake(rtcMutex, pdMS_TO_TICKS(50)) != pdTRUE) return;
    
    DateTime now = rtc.now();
    time_t currentTime = now.unixtime();
    
    xSemaphoreGive(rtcMutex);
    
    int64_t correctedMicros = getCorrectedMicroseconds();
    uint16_t subsecond = (correctedMicros % 1000000) / 10000;
    
    String syncMsg = getNodeId() + ": TIME_SYNC_REQ:" + 
                     String((unsigned long)currentTime) + ":" + 
                     String(subsecond) + ":" +
                     String((unsigned long)(correctedMicros & 0xFFFFFFFF));
    
    sendToSerial1(syncMsg, false);
    Serial.printf("[SYNC] Broadcast: %lu.%03u (drift-corrected)\n", currentTime, subsecond);
}

void updateNodeRSSI(TriangulationNode &node, int8_t newRssi) {
    node.rssi = newRssi;
    
    node.rssiRawWindow.push_back(newRssi);
    if (node.rssiRawWindow.size() > 5) {
        node.rssiRawWindow.erase(node.rssiRawWindow.begin());
    }
    
    if (node.rssiRawWindow.size() >= 5) {
        std::vector<int8_t> sorted = node.rssiRawWindow;
        std::sort(sorted.begin(), sorted.end());
        int8_t median = sorted[sorted.size() / 2];
        node.filteredRssi = kalmanFilterRSSI(node, median);
    } else {
        node.filteredRssi = kalmanFilterRSSI(node, newRssi);
    }
    
    node.rssiHistory.push_back(newRssi);
    if (node.rssiHistory.size() > RSSI_HISTORY_SIZE) {
        node.rssiHistory.erase(node.rssiHistory.begin());
    }
    
    node.signalQuality = calculateSignalQuality(node);
    node.lastUpdate = millis();
}

void handleTimeSyncResponse(const String &nodeId, time_t timestamp, uint32_t milliseconds) {
    if (!rtcAvailable) return;
    
    if (xSemaphoreTake(rtcMutex, pdMS_TO_TICKS(50)) != pdTRUE) return;
    DateTime now = rtc.now();
    time_t localTime = now.unixtime();
    xSemaphoreGive(rtcMutex);
    
    int64_t localMicros = getCorrectedMicroseconds();
    
    int32_t timeOffset = (int32_t)(localTime - timestamp);

    int64_t effectiveMicrosOffset;
    {
        std::lock_guard<std::mutex> lock(triangulationMutex);

        uint32_t reportedPropDelay = 0;
        if (nodePropagationDelays.count(nodeId) > 0) {
            reportedPropDelay = nodePropagationDelays[nodeId];
        }

        effectiveMicrosOffset = (int64_t)localMicros - (int64_t)milliseconds - (int64_t)reportedPropDelay;

        auto syncIt = std::find_if(nodeSyncStatus.begin(), nodeSyncStatus.end(),
            [&](const auto& s) { return s.nodeId == nodeId; });
        const bool found = (syncIt != nodeSyncStatus.end());
        if (found) {
            syncIt->rtcTimestamp = timestamp;
            syncIt->millisOffset = (uint32_t)((effectiveMicrosOffset < 0 ? -effectiveMicrosOffset : effectiveMicrosOffset) / 1000);
            syncIt->synced = (abs(timeOffset) == 0 && syncIt->millisOffset < 1);
            syncIt->lastSyncCheck = millis();
        }

        if (!found && nodeSyncStatus.size() < MAX_SYNC_STATUS) {
            NodeSyncStatus newSync;
            newSync.nodeId = nodeId;
            newSync.rtcTimestamp = timestamp;
            newSync.millisOffset = (uint32_t)((effectiveMicrosOffset < 0 ? -effectiveMicrosOffset : effectiveMicrosOffset) / 1000);
            newSync.synced = (abs(timeOffset) == 0 && newSync.millisOffset < 1);
            newSync.lastSyncCheck = millis();
            nodeSyncStatus.push_back(newSync);
        }
    }

    Serial.printf("[SYNC] Node %s: offset=%ldus synced=%d\n",
                  nodeId.c_str(), (long)effectiveMicrosOffset, 
                  (abs(timeOffset) == 0 && abs(effectiveMicrosOffset) < 1000));
}

bool verifyNodeSynchronization(uint32_t maxOffsetMs) {
    if (!triangulationActive) return true;
    
    uint32_t now = millis();
    int syncedCount = 0;
    int totalCount = 0;
    
    for (const auto &sync : nodeSyncStatus) {
        if (now - sync.lastSyncCheck < SYNC_CHECK_INTERVAL) {
            totalCount++;
            if (sync.synced && sync.millisOffset <= maxOffsetMs) {
                syncedCount++;
            }
        }
    }
    
    return (totalCount == 0) || (syncedCount >= (totalCount * 2 / 3));
}

// Traingulation actions

// Unwind initiator/session state when setup is aborted before the scan worker runs.
// Setup already broadcast TRIANGULATE_START, so tell child nodes to stop too.
static void triAbortCleanup(const char *reason) {
    if (triangulationInitiator && !triStopCameFromMesh) {
        sendMeshCommand("@ALL TRIANGULATE_STOP");
        Serial.println("[TRIANGULATE] Abort - STOP broadcast to child nodes");
    }
    triSetupAbort.store(false);
    triOperatorStop.store(false);
    coordinatorSetupTaskHandle = nullptr;
    triangulationActive = false;
    triangulationInitiator = false;
    triangulationDuration = 0;
    waitingForFinalReports = false;
    stopSentTimestamp = 0;
    triangulationOrchestratorAssigned = false;
    triStopCameFromMesh = false;
    {
        std::lock_guard<std::mutex> lock(triangulationMutex);
        triangulateAcks.clear();
        triangulateReportedNodes.clear();
        triangulationNodes.clear();
        nodeSyncStatus.clear();
        nodePropagationDelays.clear();
    }
    reportingSchedule.reset();
    {
        std::lock_guard<std::mutex> lock(antihunter::lastResultsMutex);
        antihunter::lastResults = "Triangulation stopped.";
    }
    lastTriangulationStopTime = millis();
    Serial.printf("[TRIANGULATE] %s\n", reason);
}

// Task that handles ACK collection and cycle start (runs async to avoid blocking web handler)
void coordinatorSetupTask(const void *parameter) {
    int duration = static_cast<int>(reinterpret_cast<intptr_t>(parameter));

    // Wait for child nodes to ACK - give mesh time to relay responses
    triSetupAbort.store(false);
    Serial.println("[TRIANGULATE] Waiting for child node ACKs...");
    {
        std::lock_guard<std::mutex> lock(antihunter::lastResultsMutex);
        antihunter::lastResults = "TRIANGULATING: Waiting for mesh nodes to respond...";
    }
    {
        uint32_t ackWaitStart = millis();
        size_t peers = detect_meshPeerCount();
        size_t expected = peers > triLastChildCount ? peers : triLastChildCount;
        while ((uint32_t)(millis() - ackWaitStart) < 15000) {
            if (triSetupAbort.load()) break;
            size_t have;
            { std::lock_guard<std::mutex> lock(triangulationMutex); have = triangulateAcks.size(); }
            if (expected > 0 && have >= expected) {
                Serial.printf("[TRIANGULATE] All %u known nodes ACKed in %ums - starting early\n",
                              (unsigned)have, (unsigned)(millis() - ackWaitStart));
                break;
            }
            vTaskDelay(pdMS_TO_TICKS(200));
        }
    }
    if (triSetupAbort.load()) { triAbortCleanup("Setup aborted by stop"); vTaskDelete(NULL); }

    // Count total nodes: coordinator + ACK'd children
    int ackedChildren;
    {
        std::lock_guard<std::mutex> lock(triangulationMutex);
        ackedChildren = (int)triangulateAcks.size();
    }
    int totalNodes = 1 + ackedChildren;  // 1 = coordinator
    if ((size_t)ackedChildren > triLastChildCount) triLastChildCount = (size_t)ackedChildren;
    Serial.printf("[TRIANGULATE] ACK collection complete: %d child nodes responded (%d total)\n",
                  ackedChildren, totalNodes);

    // Additional buffer before next broadcast
    vTaskDelay(pdMS_TO_TICKS(1000));

    {
        std::lock_guard<std::mutex> lock(antihunter::lastResultsMutex);
        antihunter::lastResults = ("TRIANGULATING: " + String(totalNodes) + " nodes ready, starting scan...").c_str();
    }

    // Broadcast synchronized cycle start time + node list for slot coordination
    int64_t cycleStartUs = getCorrectedMicroseconds();
    uint32_t cycleStartMs = (uint32_t)(cycleStartUs / 1000LL);

    // Build comma-separated list of node IDs (sorted for consistent slot assignment)
    // Include coordinator itself
    std::vector<String> nodeList;
    String coordinatorId = getNodeId();
    if (coordinatorId.length() > 0) {
        nodeList.push_back(coordinatorId);
    }
    {
        std::lock_guard<std::mutex> lock(triangulationMutex);
        std::transform(triangulateAcks.begin(), triangulateAcks.end(),
                       std::back_inserter(nodeList),
                       [](const TriangulateAckInfo& ack) { return ack.nodeId; });
    }
    std::sort(nodeList.begin(), nodeList.end());

    // Rebuild coordinator's own reporting schedule with all nodes
    reportingSchedule.reset();
    for (const auto& node : nodeList) {
        reportingSchedule.addNode(node);
    }
    reportingSchedule.cycleStartMs = cycleStartMs;

    String nodeListStr = "";
    for (size_t i = 0; i < nodeList.size(); i++) {
        if (i > 0) nodeListStr += ",";
        nodeListStr += nodeList[i];
    }

    String cycleCmd = "@ALL TRI_CYCLE_START:" + String(cycleStartMs) + ":" + nodeListStr;
    sendMeshCommand(cycleCmd);
    Serial.printf("[TRIANGULATE] Cycle start broadcast: %u ms, %d nodes: %s\n",
                  cycleStartMs, nodeList.size(), nodeListStr.c_str());

    vTaskDelay(pdMS_TO_TICKS(500));
    if (triSetupAbort.load()) { triAbortCleanup("Setup aborted by stop"); vTaskDelete(NULL); }

    if (!workerTaskHandle) {
        if (ahCreateTask(listScanTask, "triangulate", 8192,
                reinterpret_cast<void *>(static_cast<intptr_t>(duration)), 1, &workerTaskHandle, 1) != pdPASS) {
            workerTaskHandle = nullptr;
            triAbortCleanup("scan task create failed - aborting setup");
            vTaskDelete(NULL);
        }
    }

    // Set active flag AFTER task is created to prevent UI race condition
    triangulationActive = true;
    triTargetChannel.store(0);
    triTargetRadio.store(0);
    { std::lock_guard<std::mutex> _g(triAccumMutex); triAccum.gpsSamples = 0; triAccum.hasGPS = false; }

    Serial.println("[TRIANGULATE] Mesh sync initiated, scanning active");

    // Clean up - task deletes itself
    coordinatorSetupTaskHandle = nullptr;
    vTaskDelete(NULL);
}

bool startTriangulation(const String &targetMac, int duration, String *err) {
    // Debounce check: prevent rapid restarts
    uint32_t timeSinceLastStop = millis() - lastTriangulationStopTime;
    if (lastTriangulationStopTime > 0 && timeSinceLastStop < TRIANGULATION_DEBOUNCE_MS) {
        uint32_t remainingWait = (TRIANGULATION_DEBOUNCE_MS - timeSinceLastStop) / 1000;
        Serial.printf("[TRIANGULATE] DEBOUNCE: Must wait %us before starting again (last stopped %us ago)\n",
                     remainingWait, timeSinceLastStop / 1000);
        if (err) *err = "Triangulation not started: wait " + String(remainingWait) + "s after the previous run";
        return false;
    }

    if (targetMac.length() == 0) {
        Serial.println("[TRIANGULATE] No target MAC supplied");
        if (err) *err = "Triangulation not started: no target MAC entered";
        return false;
    }

    bool isIdentityId = false;

    if (targetMac.startsWith("T-") && targetMac.length() >= 6 && targetMac.length() <= 9) {
        bool validId = true;
        for (size_t i = 2; i < targetMac.length(); i++) {
            if (!isdigit(targetMac[i])) {
                validId = false;
                break;
            }
        }

        if (validId) {
            isIdentityId = true;
            strncpy(triangulationTargetIdentity, targetMac.c_str(), sizeof(triangulationTargetIdentity) - 1);
            triangulationTargetIdentity[sizeof(triangulationTargetIdentity) - 1] = '\0';
            triangulationSetTarget(nullptr);
            Serial.printf("[TRIANGULATE] Target is identity ID: %s\n", triangulationTargetIdentity);
        }
    }

    if (!isIdentityId) {
        uint8_t macBytes[6];
        if (!parseMac6(targetMac, macBytes)) {
            Serial.printf("[TRIANGULATE] Invalid MAC format: %s\n", targetMac.c_str());
            if (err) *err = "Triangulation not started: invalid target \"" + targetMac +
                            "\" - use AA:BB:CC:DD:EE:FF or a T-<digits> identity";
            return false;
        }
        triangulationSetTarget(macBytes);
        memset(triangulationTargetIdentity, 0, sizeof(triangulationTargetIdentity));
    }

    // // Force stop any existing triangulation first
    // if (triangulationActive) {
    //     Serial.println("[TRIANGULATE] Already active, forcing full stop first...");
    //     stopTriangulation();
    //     vTaskDelay(pdMS_TO_TICKS(2000)); // Wait for complete cleanup

    //     // After stop, re-check debounce since stop updates the timestamp
    //     uint32_t timeSinceStop = millis() - lastTriangulationStopTime;
    //     if (timeSinceStop < TRIANGULATION_DEBOUNCE_MS) {
    //         uint32_t remainingWait = (TRIANGULATION_DEBOUNCE_MS - timeSinceStop) / 1000;
    //         Serial.printf("[TRIANGULATE] DEBOUNCE: Must wait %us after forced stop before starting again\n", remainingWait);
    //         return;
    //     }
    // }

    if (workerTaskHandle) {
        Serial.println("[TRIANGULATE] WARNING: Worker task still exists, stopping...");
        stopRequested = true;

        uint32_t taskStopWait = millis();
        while (workerTaskHandle != nullptr && (millis() - taskStopWait) < 3000) {
            vTaskDelay(pdMS_TO_TICKS(100));
        }

        if (workerTaskHandle != nullptr) {
            Serial.println("[TRIANGULATE] ERROR: Worker task still running after 3s, aborting start");
            if (err) *err = "Triangulation not started: previous scan task still running";
            return false;
        }
        vTaskDelay(pdMS_TO_TICKS(500));
    }
    
    {
        std::lock_guard<std::mutex> lock(antihunter::lastResultsMutex);
        antihunter::lastResults = "TRIANGULATING: Synchronizing time with mesh nodes...";
    }

    {
        std::lock_guard<std::mutex> lock(triangulationMutex);
        triangulationNodes.clear();
        triangulateAcks.clear();  // Clear ACK list for new triangulation
        triangulationNodes.reserve(10);
        nodeSyncStatus.clear();
        nodeSyncStatus.reserve(10);
    }
    triangulationStart = millis();
    triangulationDuration = duration;
    currentScanMode = SCAN_BOTH;
    stopRequested = false;
    triOperatorStop.store(false);
    triangulationInitiator = true;
    reportingSchedule.reset();

    // Clear wait tracking for new session
    triangulateReportedNodes.clear();
    waitingForFinalReports = false;
    stopSentTimestamp = 0;
    ackCollectionStart = millis();

    Serial.printf("[TRIANGULATE] Initiator started for %s (%ds)\n", targetMac.c_str(), duration);

    broadcastTimeSyncRequest();
    vTaskDelay(pdMS_TO_TICKS(2000));

    String myNodeId = getNodeId();
    String cmd = "@ALL TRIANGULATE_START:" + targetMac + ":" + String(duration) + ":" + myNodeId + ":" + String(currentRFEnvironment);
    if (distanceTuning.enabled) {
        cmd += ":" + String(distanceTuning.wifi_multiplier, 2) + ":" + String(distanceTuning.ble_multiplier, 2);
    }
    sendMeshCommand(cmd);

    Serial.printf("[TRIANGULATE] Broadcast sent to mesh nodes (initiator: %s)\n", myNodeId.c_str());

    // Create async task to collect ACKs and start scanning (avoids blocking web handler)
    if (!coordinatorSetupTaskHandle) {
        if (ahCreateTask(reinterpret_cast<TaskFunction_t>(coordinatorSetupTask), "triCoordSetup", 4096,
                reinterpret_cast<void *>(static_cast<intptr_t>(duration)), 2, &coordinatorSetupTaskHandle, 1) != pdPASS) {
            coordinatorSetupTaskHandle = nullptr;
            Serial.println("[TRIANGULATE] Coordinator setup task create failed");
            if (err) *err = "Triangulation not started: coordinator task could not be created";
            return false;
        }
        Serial.println("[TRIANGULATE] Coordinator setup task created (async ACK collection)");
    }
    return true;
}

uint32_t calculateAdaptiveTimeout(uint32_t baseTimeoutMs, float perNodeFactor) {
    // Calculate adaptive timeout based on node count and measured mesh latency
    uint32_t timeout = baseTimeoutMs;

    // Factor in number of nodes (more nodes = more potential for delays)
    uint32_t nodeCount;
    uint32_t maxPropDelay = 0;
    uint32_t delayCount = 0;
    {
        std::lock_guard<std::mutex> lock(triangulationMutex);
        nodeCount = (uint32_t)triangulateAcks.size();

        for (const auto& pair : nodePropagationDelays) {
            uint32_t delay = pair.second;
            if (delay < 1000000) {
                if (delay > maxPropDelay) {
                    maxPropDelay = delay;
                }
                delayCount++;
            }
        }
    }
    if (nodeCount > 0) {
        timeout += (uint32_t)(nodeCount * perNodeFactor);
    }

    if (delayCount > 0) {
        uint32_t latencyMargin = (maxPropDelay / 1000) * 3;
        timeout += latencyMargin;

        Serial.printf("[ADAPTIVE_TIMEOUT] Base=%ums, Nodes=%u (+%.0fms), MaxProp=%uus (+%ums), Total=%ums\n",
                     baseTimeoutMs, nodeCount, nodeCount * perNodeFactor,
                     maxPropDelay, latencyMargin, timeout);
    } else {
        Serial.printf("[ADAPTIVE_TIMEOUT] Base=%ums, Nodes=%u (+%.0fms), No latency data, Total=%ums\n",
                     baseTimeoutMs, nodeCount, nodeCount * perNodeFactor, timeout);
    }

    return timeout;
}

void markTriangulationStopFromMesh() {
    triStopCameFromMesh = true;
}

static std::atomic<bool> triStopInProgress(false);
static TaskHandle_t triStopTaskHandle = nullptr;

static void triStopTask(void *pv) {
    (void)pv;
    stopTriangulation();
    triStopTaskHandle = nullptr;
    vTaskDelete(NULL);
}

// stopTriangulation() blocks 10s+ collecting reports - never run it on async_tcp or the mesh RX task
void requestTriangulationStop() {
    triOperatorStop.store(true);
    if (!triangulationActive && coordinatorSetupTaskHandle == nullptr) {
        stopTriangulation();
        return;
    }
    if (triStopTaskHandle != nullptr || triStopInProgress.load()) {
        Serial.println("[TRIANGULATE] Stop already running - escalating operator abort");
        return;
    }
    if (ahCreateTask(triStopTask, "triStop", 4096, nullptr, 2, &triStopTaskHandle, 1) != pdPASS) {
        triStopTaskHandle = nullptr;
        stopRequested = true;
        Serial.println("[TRIANGULATE] Stop task create failed - signalled scan task instead");
    }
}
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
